DeniseViltes/Tesis/docs/informe/Entregas Parciales/2025-11-14.pdf

# Informe 7/11/2025

### Integrantes

## Sebastián Ezequiel García

Padrón: 103780
sebgarcia@fi.uba.ar

## Denise Oriana Viltes

Padrón: 106943
dviltes@fi.uba.ar

### Tutora

## Dra. Cecilia G. Galarza

cgalar@fi.uba.ar

### Cotutor

## Ing. Juan Zuloaga

jzuloaga@fi.uba.ar

Propuesta de Trabajo Profesional de Ingeniería | Año 2025

## 1. Resultados de la semana

### 1.1. Análisis térmico en el PMOS

### 1.1.1. Resistencia térmica para el encapsulado AO3401A

Se parte de la ecuación de resistencia térmica:

θja = θjc + θcs + θsa

Donde θja es la resistencia térmica entre la juntura y el ambiente, θjc entre juntura y carcasa, θcs entre carcasa y disipador, y θsa entre disipador y ambiente. La que se busca calcular es esta última.
Previamente se debe calcular únicamente θja, dado que θcs se toma como 1,5

◦C
W
por la resistencia de la pasta térmica y θjc se da en la datasheet como 125 ◦C
W .
El parámetro faltante se lo calcula como:

θja =

Tj − Ta

P cmáx

Donde Tj es la temperatura máxima de la juntura, Ta la ambiente y P cmáx la máxima potencia en el transistor. De la hoja de datos se tomó como 150 ◦C y

considerando que se utilice durante el verano, se toma la temperatura ambiente 30 ◦C. Sin embargo, la potencia es prácticamente nula en todo momento

### 1.2. PCB

Exportamos directamente de LTspice el esquemático a Kicad, arreglamos pines y asignamos huellas. Asimismo se agregan test points, y conectores.

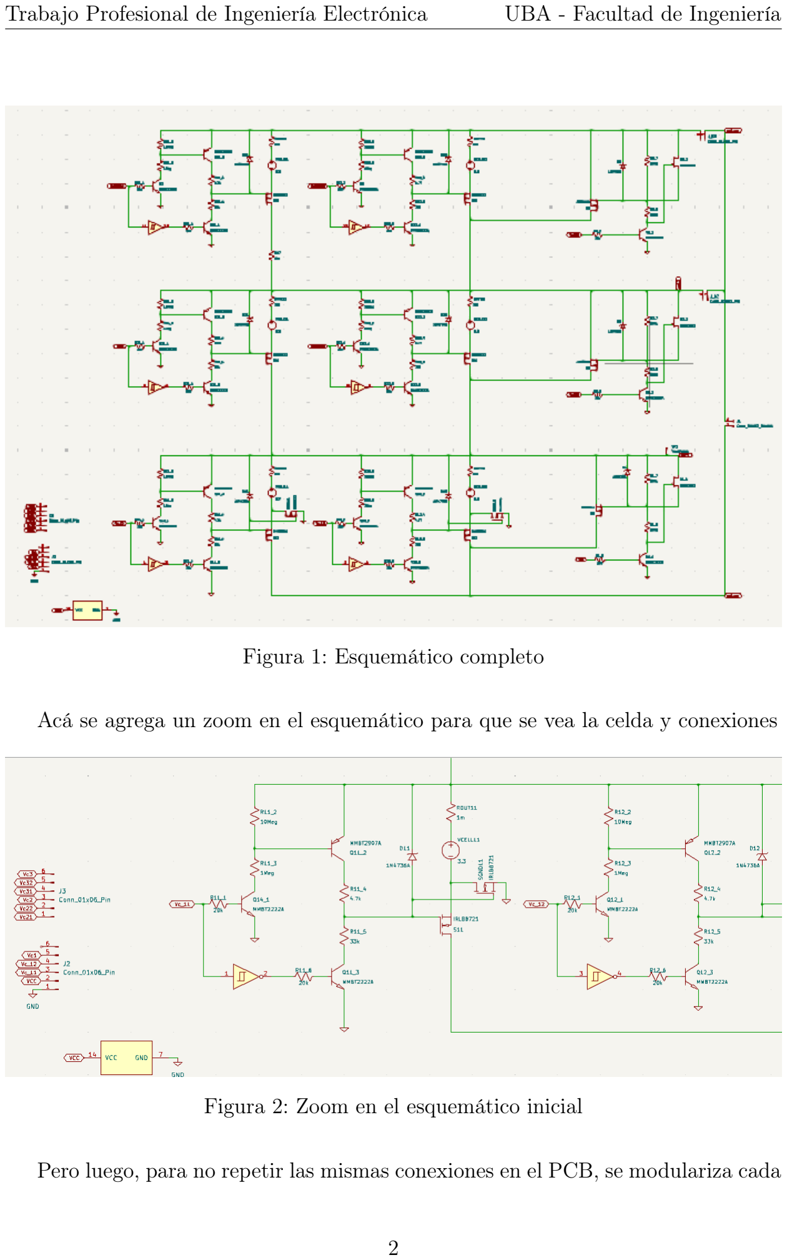
[picture p95: page 3]

Trabajo Profesional de Ingeniería Electrónica | UBA - Facultad de Ingeniería

Figura 1: Esquemático completo

Acá se agrega un zoom en el esquemático para que se vea la celda y conexiones

Figura 2: Zoom en el esquemático inicial

Pero luego, para no repetir las mismas conexiones en el PCB, se modulariza cada

2

Trabajo Profesional de Ingeniería Electrónica | UBA - Facultad de Ingeniería

switch, la propuesta de módulo es:

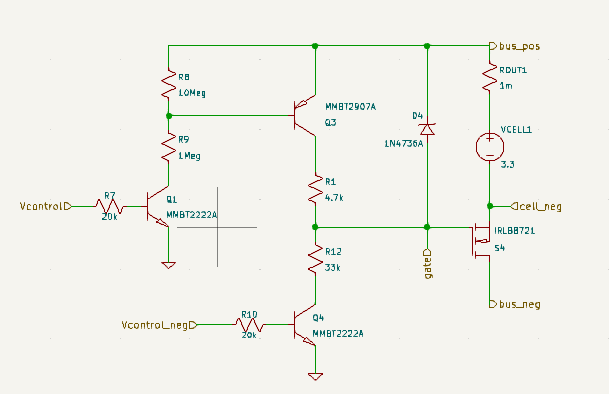
[picture p96: figure]

Figura 3: Módulo para el switch NMOS

3

Trabajo Profesional de Ingeniería Electrónica | UBA - Facultad de Ingeniería

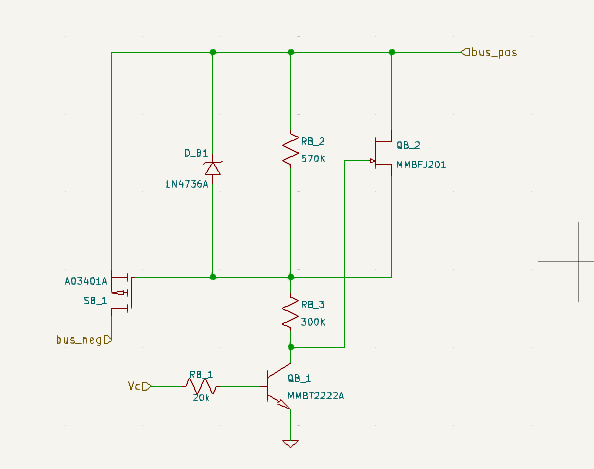
[picture p97: figure]

Figura 4: Módulo para el switch PMOS

4

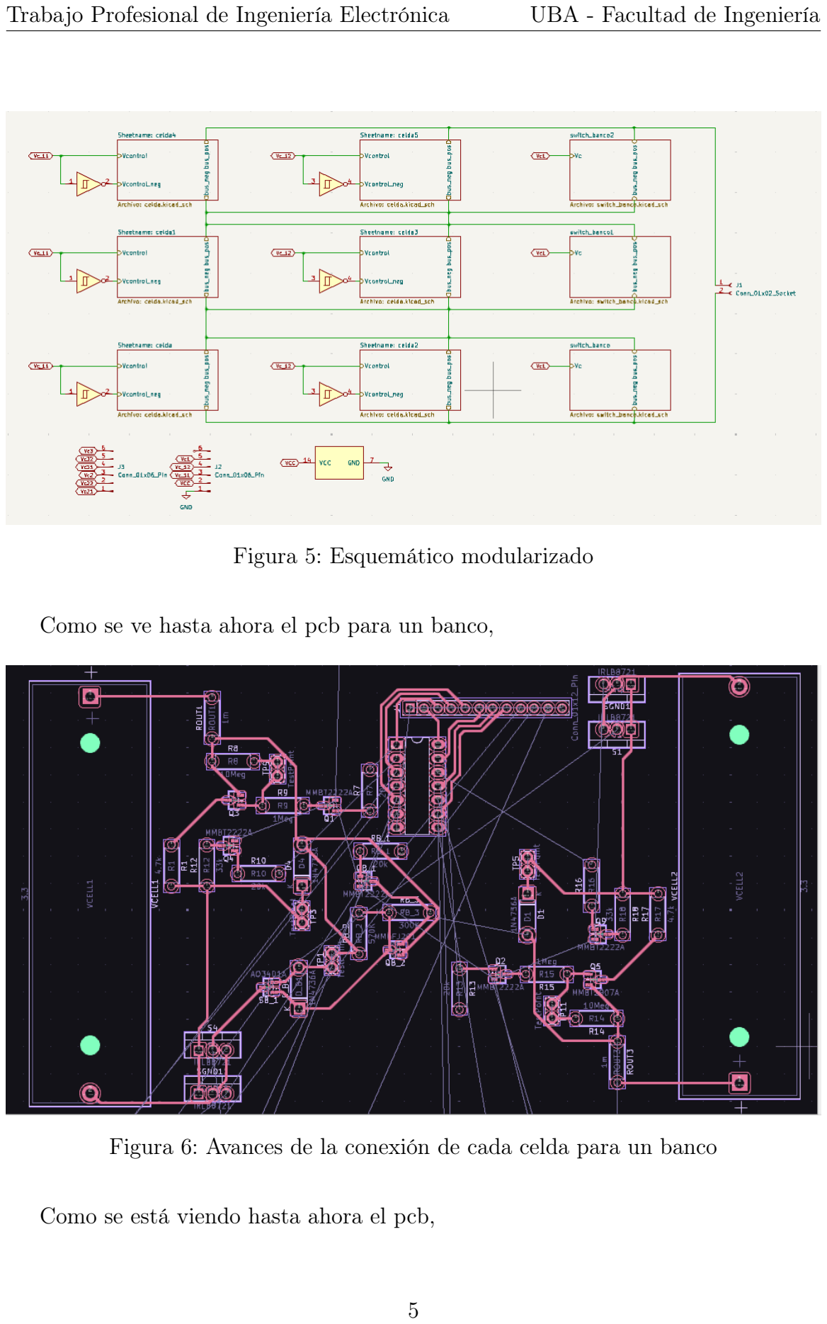
[picture p98: page 6]

Trabajo Profesional de Ingeniería Electrónica | UBA - Facultad de Ingeniería

Figura 5: Esquemático modularizado

Como se ve hasta ahora el pcb para un banco,

Figura 6: Avances de la conexión de cada celda para un banco

Como se está viendo hasta ahora el pcb,

5

Trabajo Profesional de Ingeniería Electrónica | UBA - Facultad de Ingeniería

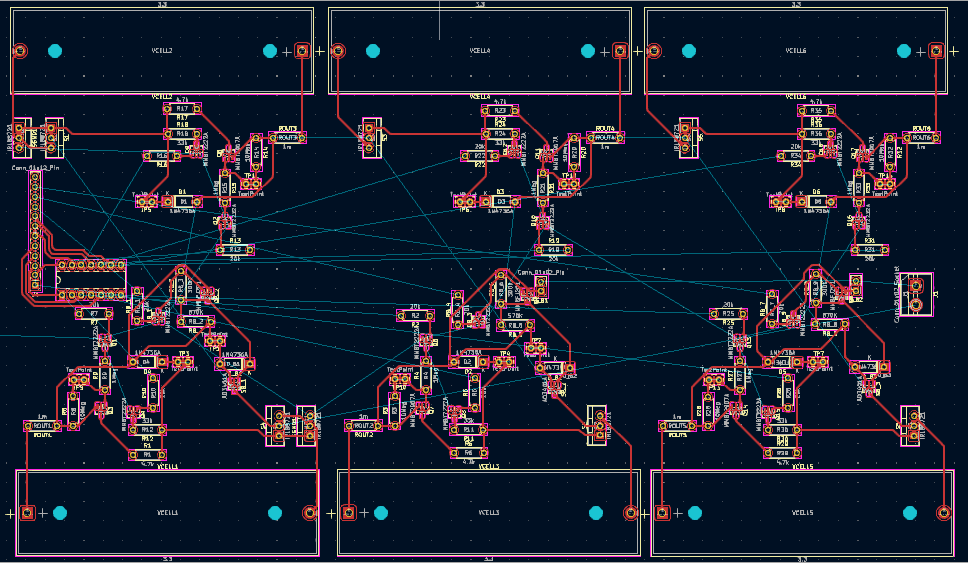
[picture p99: figure]

Figura 7: PCB entero.

6
