DeniseViltes/Tesis/docs/informe/Entregas Parciales/2025-11-28.pdf

# Informe 28/11/2025

### Integrantes

## Sebastián Ezequiel García

Padrón: 103780
sebgarcia@fi.uba.ar

## Denise Oriana Viltes

Padrón: 106943
dviltes@fi.uba.ar

### Tutora

## Dra. Cecilia G. Galarza

cgalar@fi.uba.ar

### Cotutor

## Ing. Juan Zuloaga

jzuloaga@fi.uba.ar

Propuesta de Trabajo Profesional de Ingeniería | Año 2025

## 1. Resultados de la semana

Acomodamos los elementos del pcb para que no quede tan largo, ya si obtener una versión más compacta. Para trabajar más cómodos, pasamos las pistas a un minimos de 0.6mm, siendo la mayoría de 1mm.

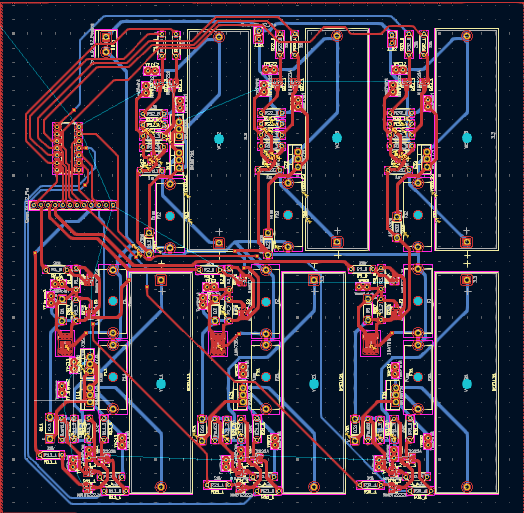
[picture p105: figure]

Figura 1: Nueva organización del pcb

Además cambiamos de capa las conexiones para los componenentes THT que solo podemos soldar de un lado, como los portapilas y portafusibles.

Trabajo Profesional de Ingeniería Electrónica | UBA - Facultad de Ingeniería

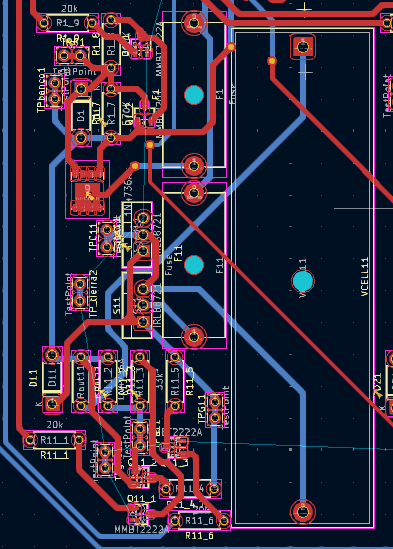
[picture p106: figure]

Figura 2: PCB de la celda 1 2

Trabajo Profesional de Ingeniería Electrónica | UBA - Facultad de Ingeniería

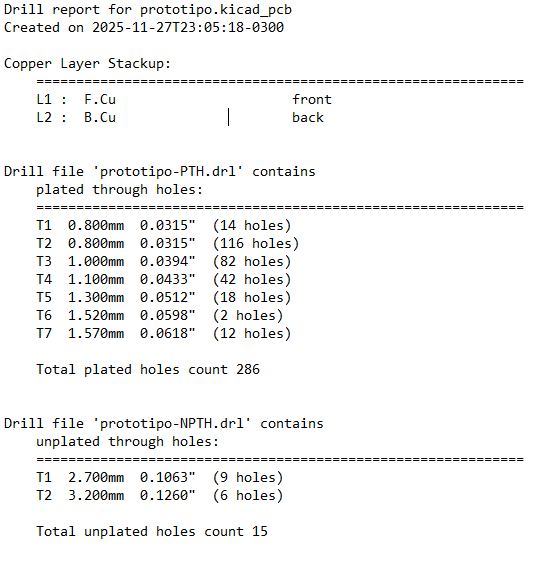
[picture p107: figure]

Figura 3: Resumen de agujeros del pcb

Cambio los agujeros:

1.0 mm ->1.1mm (pines de entrada, test points, jumpers)

2.7mm ->3.2 (portafusibles)

1.57 ->1.6 (portapilas)

3

Trabajo Profesional de Ingeniería Electrónica | UBA - Facultad de Ingeniería

1.52 ->1.6 (bornera)

Cantidad Forma | Tamaño X | Tamaño Y | Revestido
124 | Redondo 1.1000 mm 1.1000 mm PTH
116 | Redondo 0.8000 mm 0.8000 mm PTH
18 | Redondo 1.3000 mm 1.3000 mm PTH
16 | Redondo 0.8000 mm 0.8000 mm PTH
15 | Redondo 3.2000 mm 3.2000 mm NPTH
14 | Redondo 1.6000 mm 1.6000 mm PTH

Cuadro 1: Tabla de distribución de agujeros

4

Trabajo Profesional de Ingeniería Electrónica | UBA - Facultad de Ingeniería

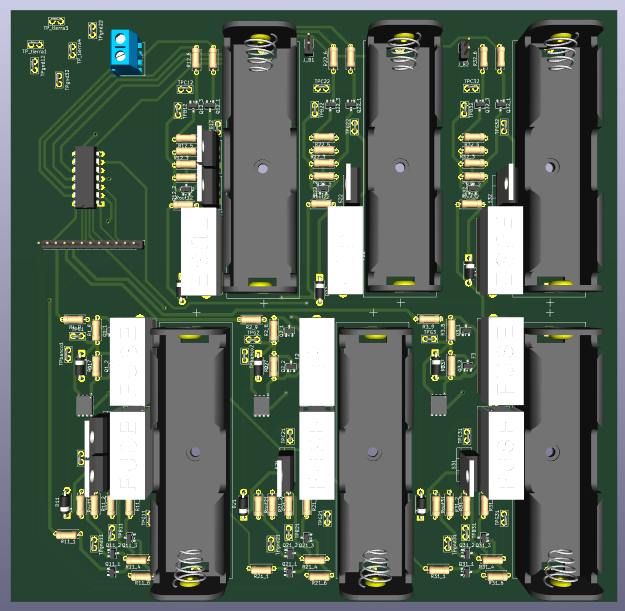
[picture p108: figure]

Figura 4: Vista superior del pcb

5

Trabajo Profesional de Ingeniería Electrónica | UBA - Facultad de Ingeniería

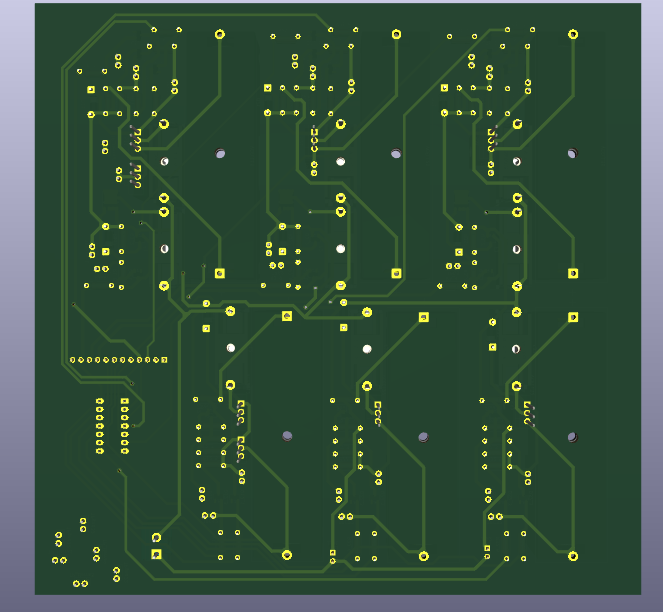
[picture p109: figure]

Figura 5: Vista inferior

6
