DeniseViltes/Tesis/docs/informe/Entregas Parciales/2026-01-16.pdf

# Informe 16/01/2026

Integrantes

## Sebastián Ezequiel García

Padrón: 103780
sebgarcia@fi.uba.ar

## Denise Oriana Viltes

Padrón: 106943
dviltes@fi.uba.ar

Tutora

## Dra. Cecilia G. Galarza

cgalar@fi.uba.ar
Cotutor

## Ing. Juan Zuloaga

jzuloaga@fi.uba.ar

Propuesta de Trabajo Profesional de Ingeniería | Año 2026

Trabajo Profesional de Ingeniería Electrónica | UBA - Facultad de Ingeniería

## 1. Carga en el circuito

Se reemplazaron las celdas por capacitores descargados de 1 µF para hacer la simulación en LTspice. Para la alimentación se pusieron en paralelo una fuente de tensión de 9,9 V y una de corriente de 500 mA.

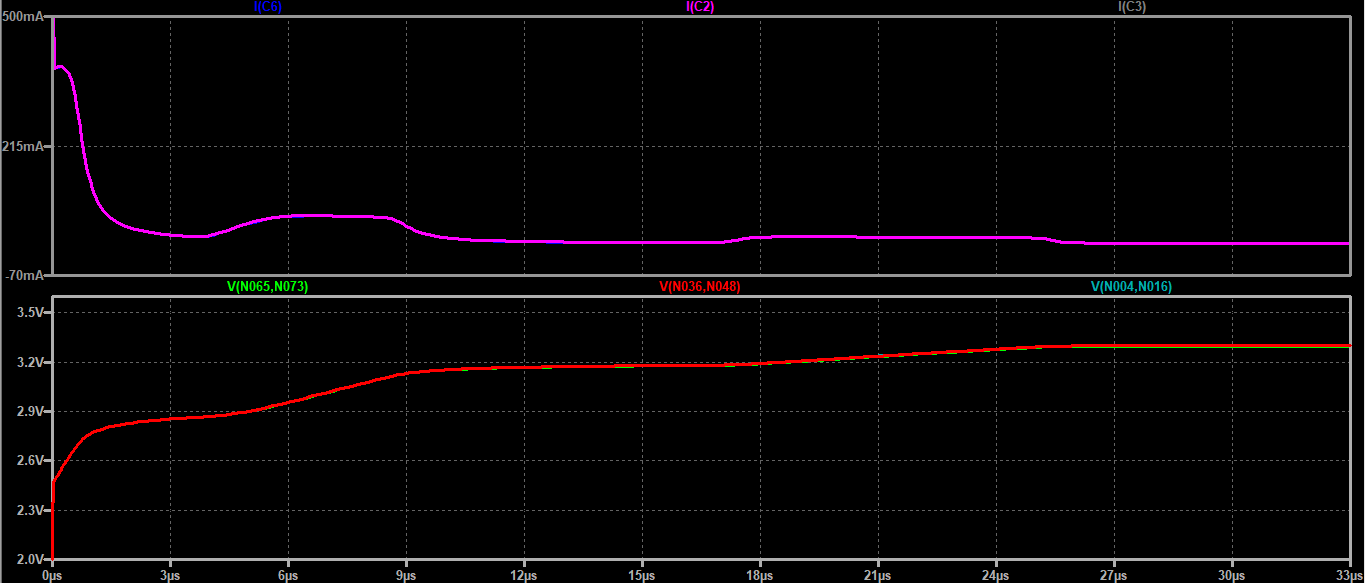
[picture p123: figure]

Figura 1: Resultado de la simulación al poner el circuito en modo carga.

Cabe destacar que se configuraron todos los switches de la celdas encendidos y todos los de los bancos apagados.

1
