DeniseViltes/Tesis/docs/informe/Entregas Parciales/2025-11-7.pdf

# Informe 7/11/2025

### Integrantes

## Sebastián Ezequiel García

Padrón: 103780
sebgarcia@fi.uba.ar

## Denise Oriana Viltes

Padrón: 106943
dviltes@fi.uba.ar

### Tutora

## Dra. Cecilia G. Galarza

cgalar@fi.uba.ar

### Cotutor

## Ing. Juan Zuloaga

jzuloaga@fi.uba.ar

Propuesta de Trabajo Profesional de Ingeniería | Año 2025

## 1. Resultados de la semana

### 1.1. Mosfet en tierra

Se observa menos oscilación, y resultados similares a resistencias altas en tierra con el beneficio de que no altera el comportamiento del circuito.
Primero lo colocacamos con gate y sources conectado a los mismos puntos que el nmos principal, pero deformaba la corriente en las celdas. Cambiamos la conexión poniendo el source a tierra y se adapta perfectamente al comportamiento de la matriz.

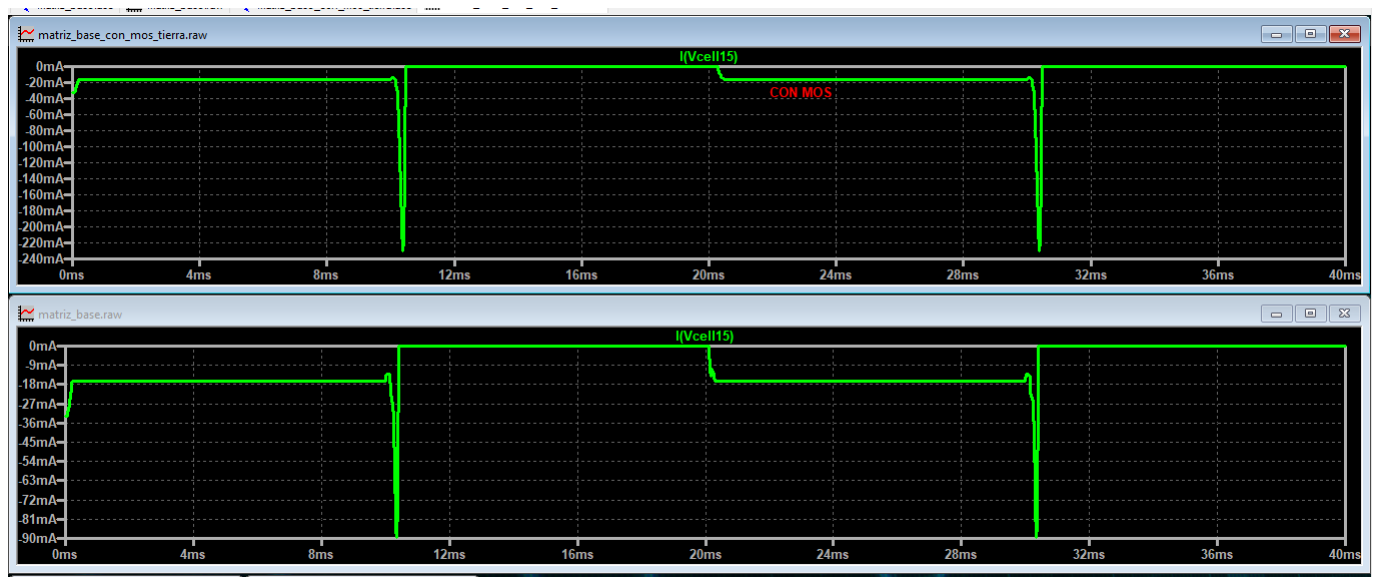
[picture p136: figure]

Figura 1: Corriente en celda intercalada

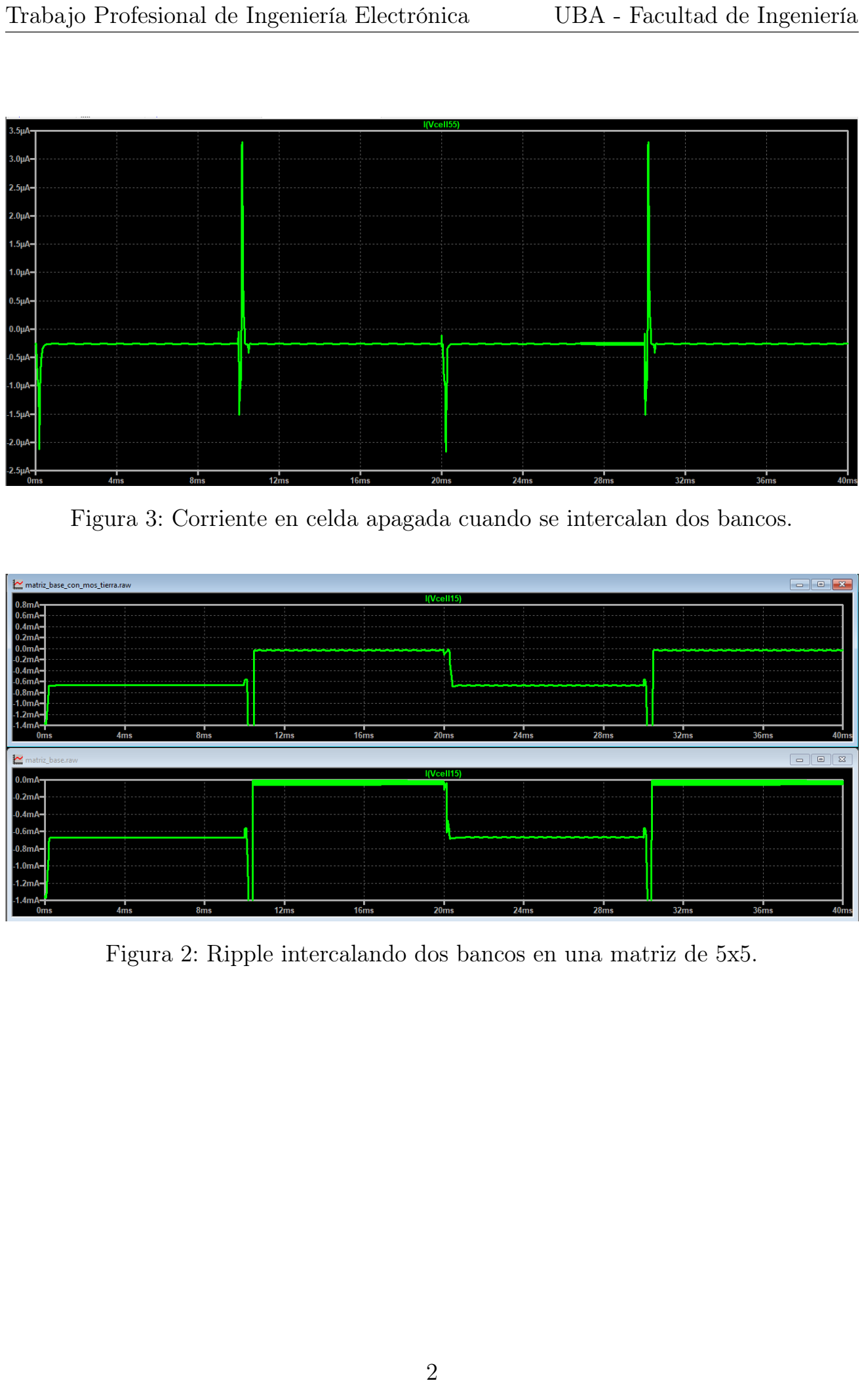
[picture p137: page 3]

Trabajo Profesional de Ingeniería Electrónica | UBA - Facultad de Ingeniería

Figura 3: Corriente en celda apagada cuando se intercalan dos bancos.

Figura 2: Ripple intercalando dos bancos en una matriz de 5x5.

2

Trabajo Profesional de Ingeniería Electrónica | UBA - Facultad de Ingeniería

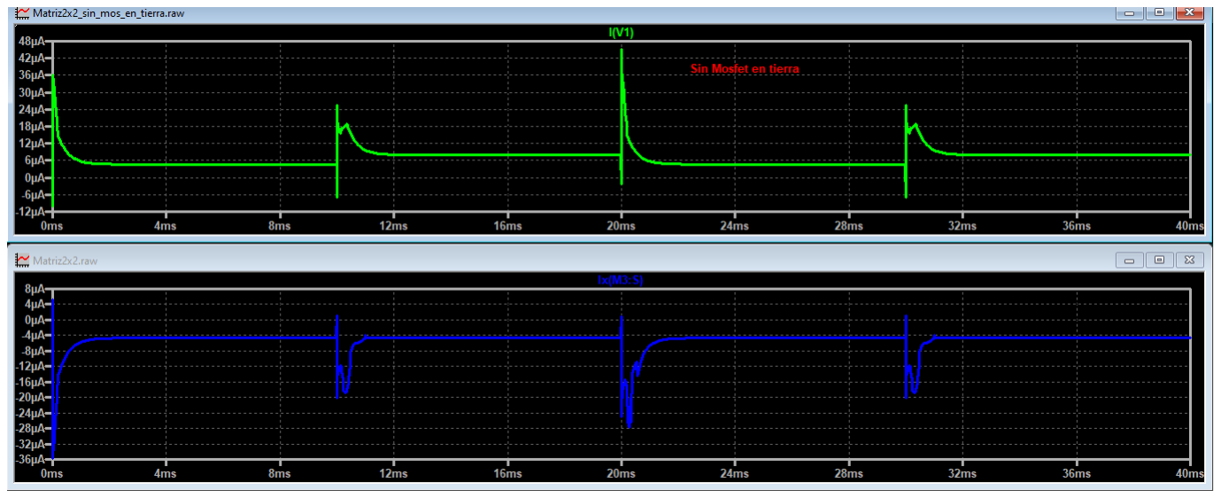
[picture p138: figure]

Figura 4: Corriente en tierra

### 1.2. Comparación de circuito con y sin inversores

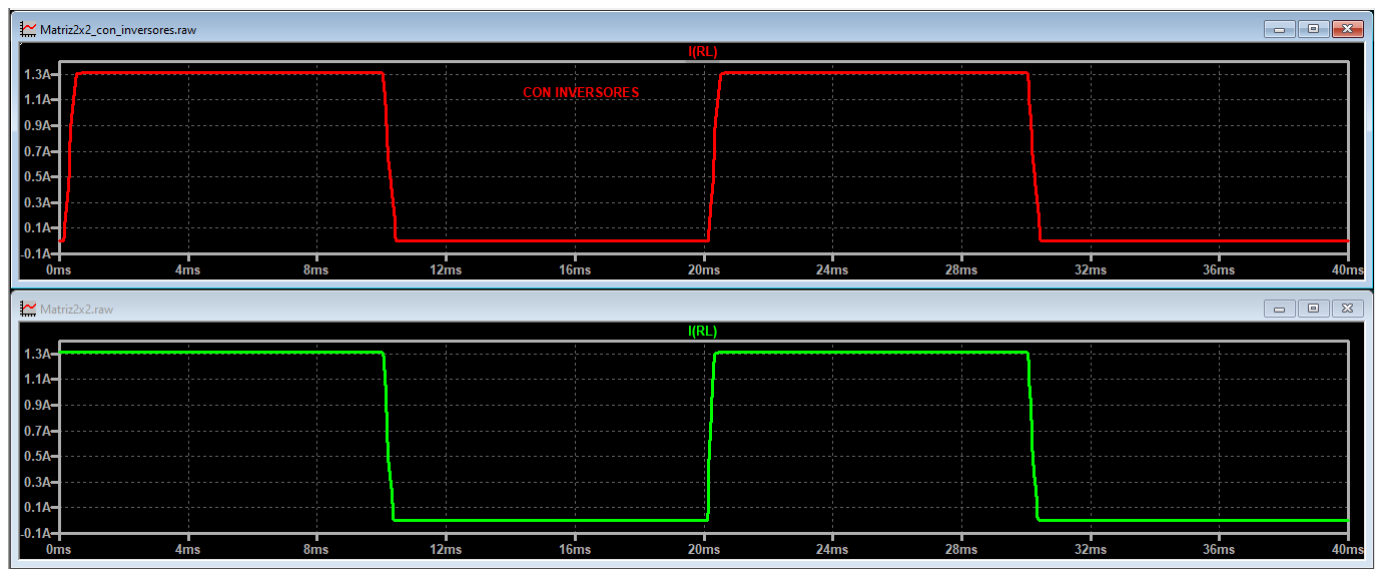
[picture p139: figure]

Figura 5: Corriente con y sin inversores para el banco 1 y 2 coordinados en prendido/apagado.

3

Trabajo Profesional de Ingeniería Electrónica | UBA - Facultad de Ingeniería

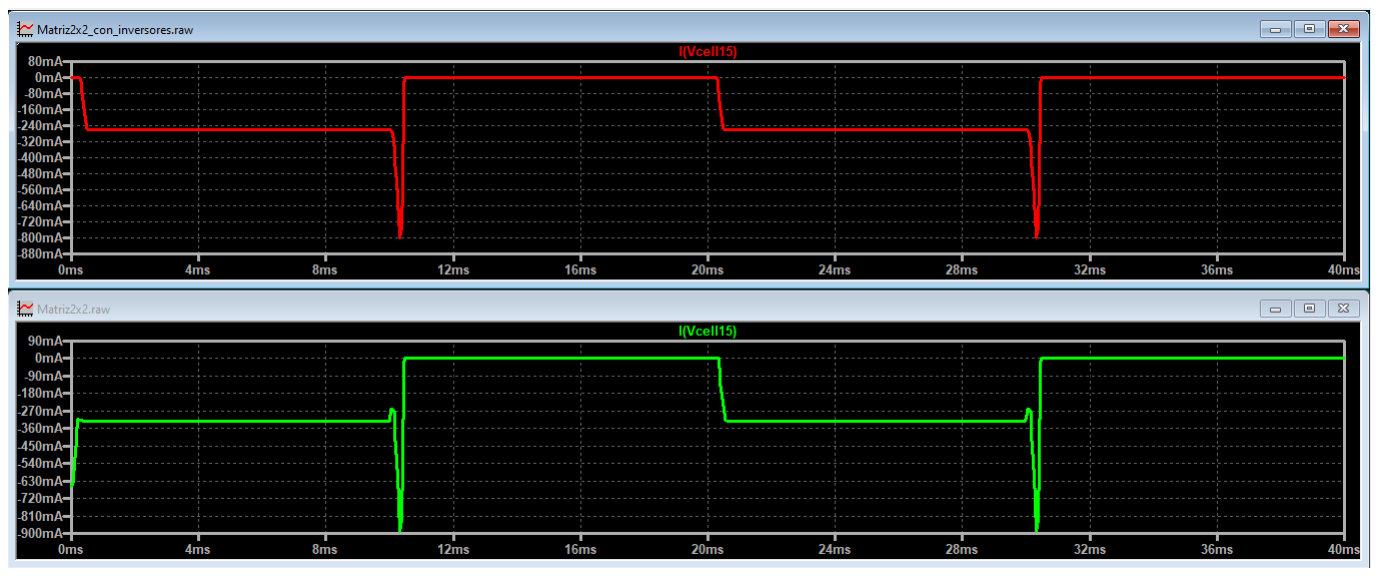
[picture p140: figure]

Figura 6: Corriente en las celdas para los bancos intercalados

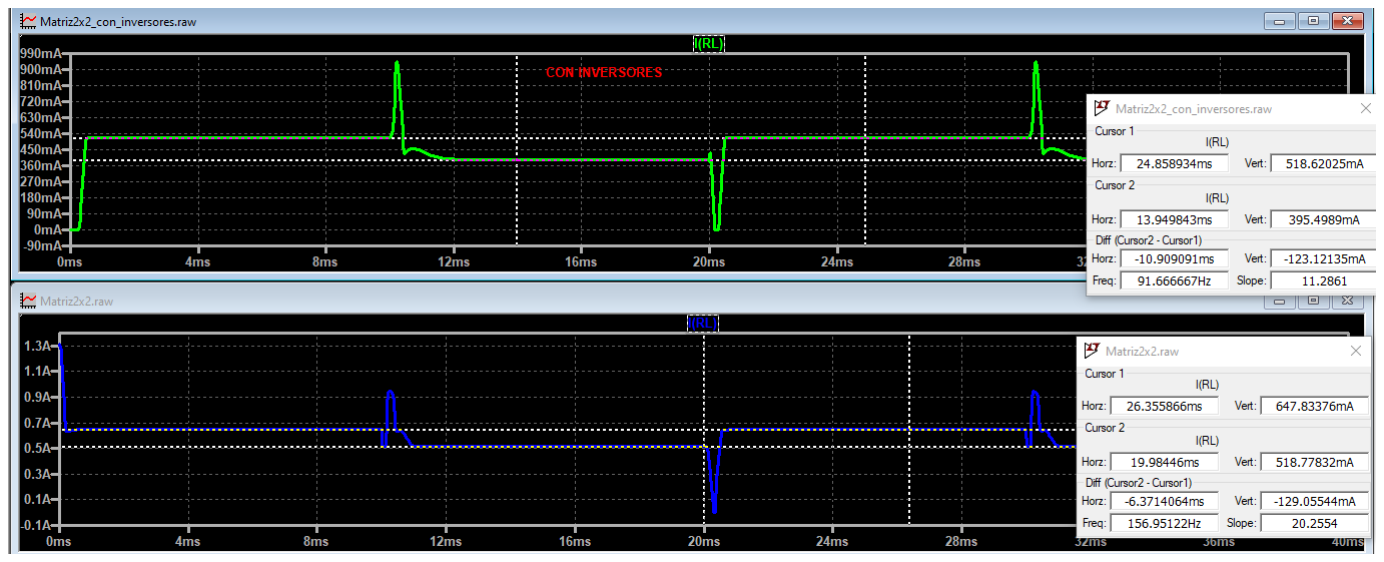
[picture p141: figure]

Figura 7: Corriente en la carga para bancos intercalados

### 1.3. Ripple

En cuanto al ripple que observamos hasta ahora

4

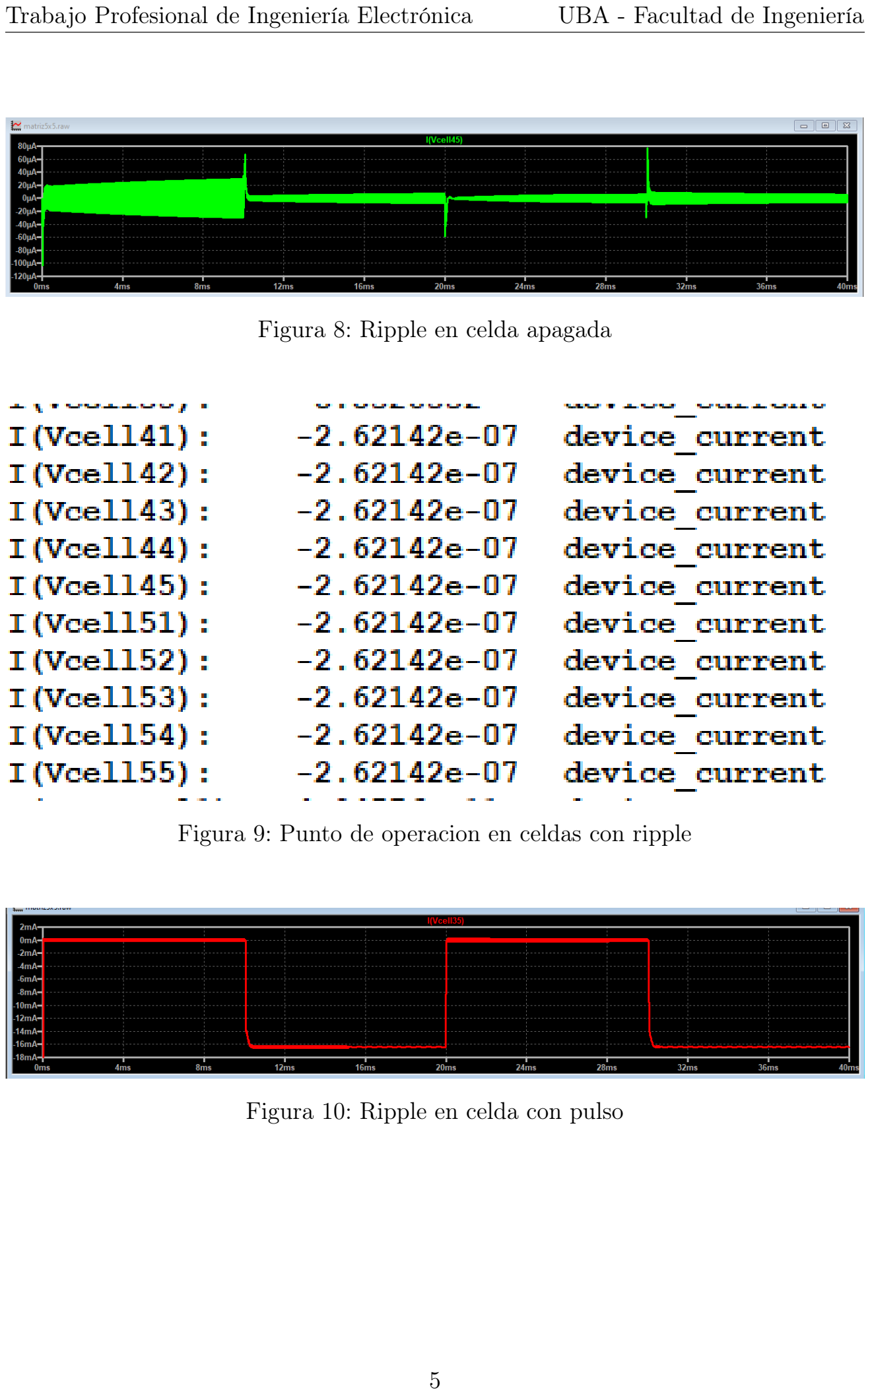
[picture p142: page 6]

Trabajo Profesional de Ingeniería Electrónica | UBA - Facultad de Ingeniería

Figura 8: Ripple en celda apagada

Figura 9: Punto de operacion en celdas con ripple

Figura 10: Ripple en celda con pulso

5

Trabajo Profesional de Ingeniería Electrónica | UBA - Facultad de Ingeniería

Figura 11: Enter Caption

### 1.4. Resistencias en el driver

Se disminuyen en un orden las resistencias en el driver, en el tbj de apagado, para permitir que haya un camino en el nmos pueda descargarse más rápido y asi evitamos poner un delay entre las fuentes del driver (al menos en simulación).

6
