DeniseViltes/Tesis/hardware/Circuito Final/Circuito externo/Pines controlador.xlsx

2 | PC10 | CLK | LATCH | PC11 | 1 | 2 | PC9 | S0 | S1 | PC8 | 1 | UART | Pines GPIO: | Pines ADC:
4 | PC12 | D1 |  | PD2 | 3 | 4 | PB8 |  | S2 | PC6 | 3 | ADC | B0 | OUT_ADC1
6 | VDD |  |  | E5V | 5 | 6 | PB9 |  | salida_adc_4 | PC5 | 5 | GPIO | B1 | bus_pos1
8 | BOOT0 |  |  | GND | 7 | 8 | AVDD |  |  | U5V | 7 | Potencia | B2 | bus_neg1
10 | - |  |  | - | 9 | 10 | GND |  |  | - | 9 | Reset | CLK_S | OUT_ADC2
12 | - |  |  | 3.3V | 11 | 12 | PA5/PB13 | banco4_med | D4 | PA12 | 11 | No usar | CLK_L | bus_pos2
14 | PA13 |  |  | Reset | 13 | 14 | PA6/PB14 | medicion_corriente_descarga | D3 | PA11 | 13 |  | D1 | bus_neg2
16 | PA14 |  |  | 3.3V | 15 | 16 | PA7/PB15 | banco3_med |  | PB12 | 15 |  | D2 | OUT_ADC3
18 | PA15 |  | vcc stm | 5V | 17 | 18 | PB6 |  |  | PB11 | 17 |  | D3 | bus_pos3
20 | GND |  |  | GND | 19 | 20 | PC7 |  |  | GND | 19 |  | D4 | bus_neg3
22 | PB7 |  |  | GND | 21 | 22 | PA9 |  |  | PB2 | 21 |  |  | OUT_ADC4
24 | PC13 | D2 |  | VIN | 23 | 24 | PA8 |  |  | PB1 | 23 |  |  | bus_pos4
26 | PC14 |  |  | - | 25 | 26 | PB10 |  |  | PB15/PA7 | 25 |  |  | bus_neg4
28 | PC15 |  | salida_adc_1 | PA0 | 27 | 28 | PB4 |  |  | PB14/PA6 | 27
30 | PD0 |  | banco1_med | PA1 | 29 | 30 | PB5 |  |  | PB13/PA5 | 29
32 | PD1 |  | ADC4 | PA4 | 31 | 32 | PB3 |  |  | AGND | 31
34 | VDD |  |  | PB0 | 33 | 34 | PA10 | llave de emergencia | salida_adc_3 | PC4 | 33
36 | PC2 | salida_adc_2 | ADC11 | PC1/PB9 | 35 | 36 | PA2 |  |  | - | 35
38 | PC3 | banco2_med | medicion_corriente_de_carga | PC0/PB8 | 37 | 38 | PA3 |  |  | - | 37
