DeniseViltes/Tesis/hardware/Circuito Final/Switch banco - Torre/pines_entrada.xlsx

VCC | CLOCK | GND | BUS NEG | BUS POS | BIT 2 | BIT 1
DATA | LATCH | GND | BUS NEG | BUS POS | SALIDA ADC | BIT 0
