DeniseViltes/Tesis/docs/burocracia/Acta de acuerdo.pdf

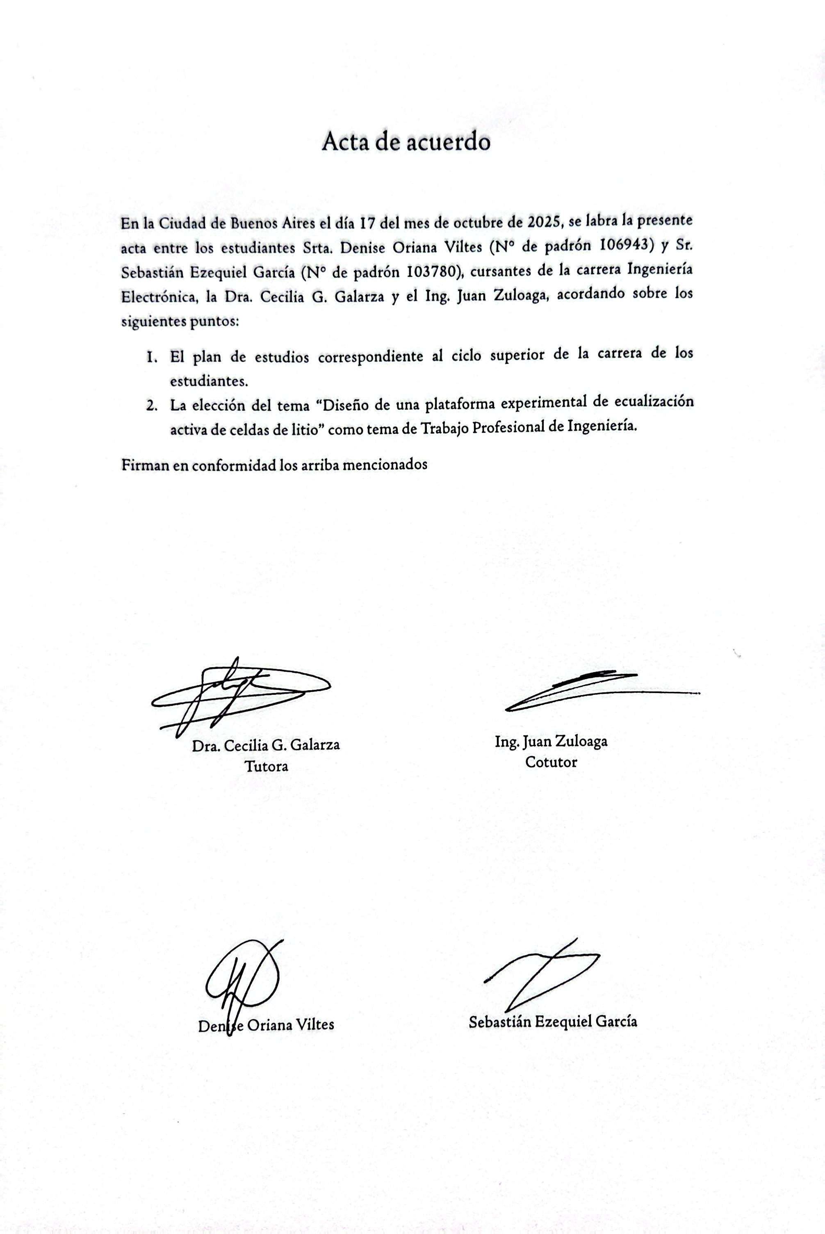
[picture p148: page 1]
