DeniseViltes/Tesis/codigo/firmware/Controlador/BluePill - STM32F103 - Pinout.jpg

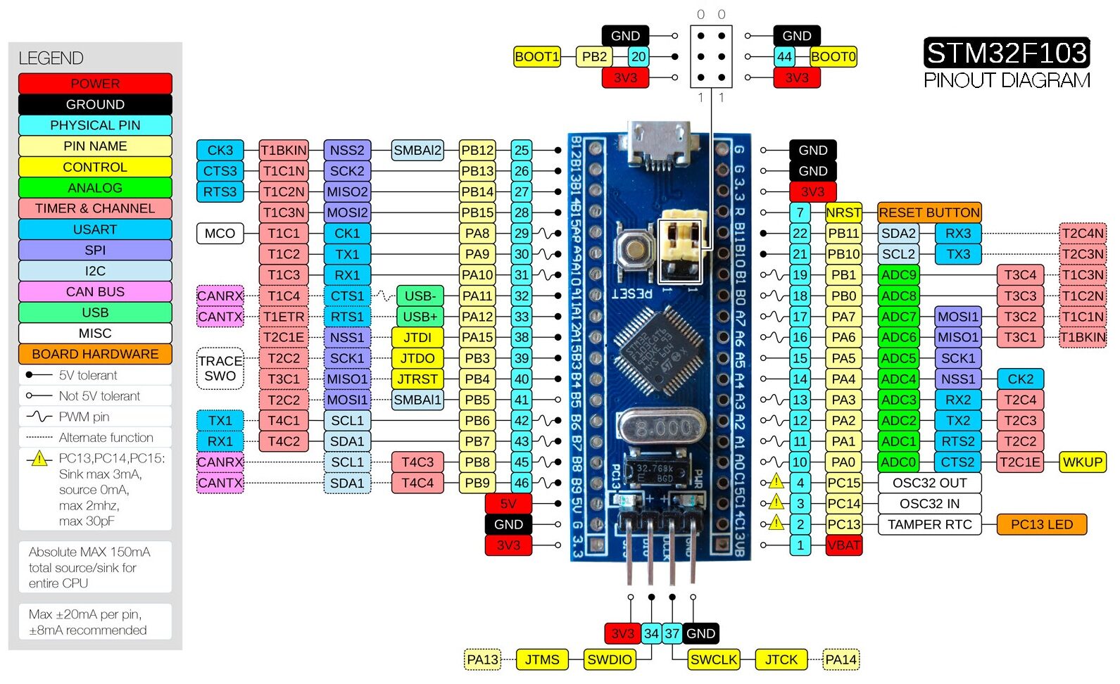
codigo/firmware/Controlador/BluePill - STM32F103 - Pinout.jpg
