DeniseViltes/Tesis/codigo/firmware/Controlador/Prototipo/documentacion/01_funcionamiento_general.png

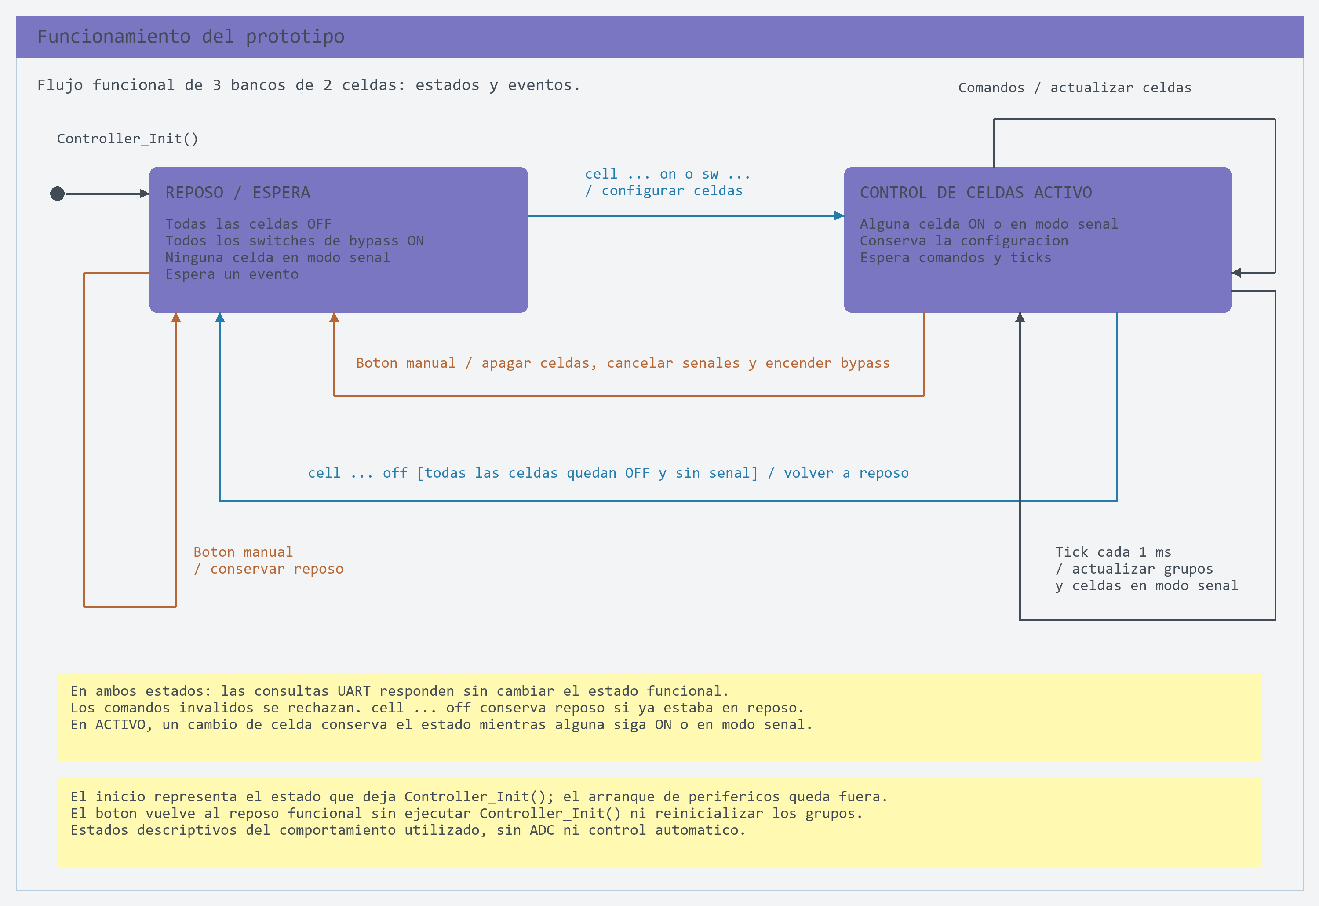
codigo/firmware/Controlador/Prototipo/documentacion/01_funcionamiento_general.png
