DeniseViltes/Tesis/codigo/firmware/Controlador/Prototipo/documentacion/02_estados_celda.png

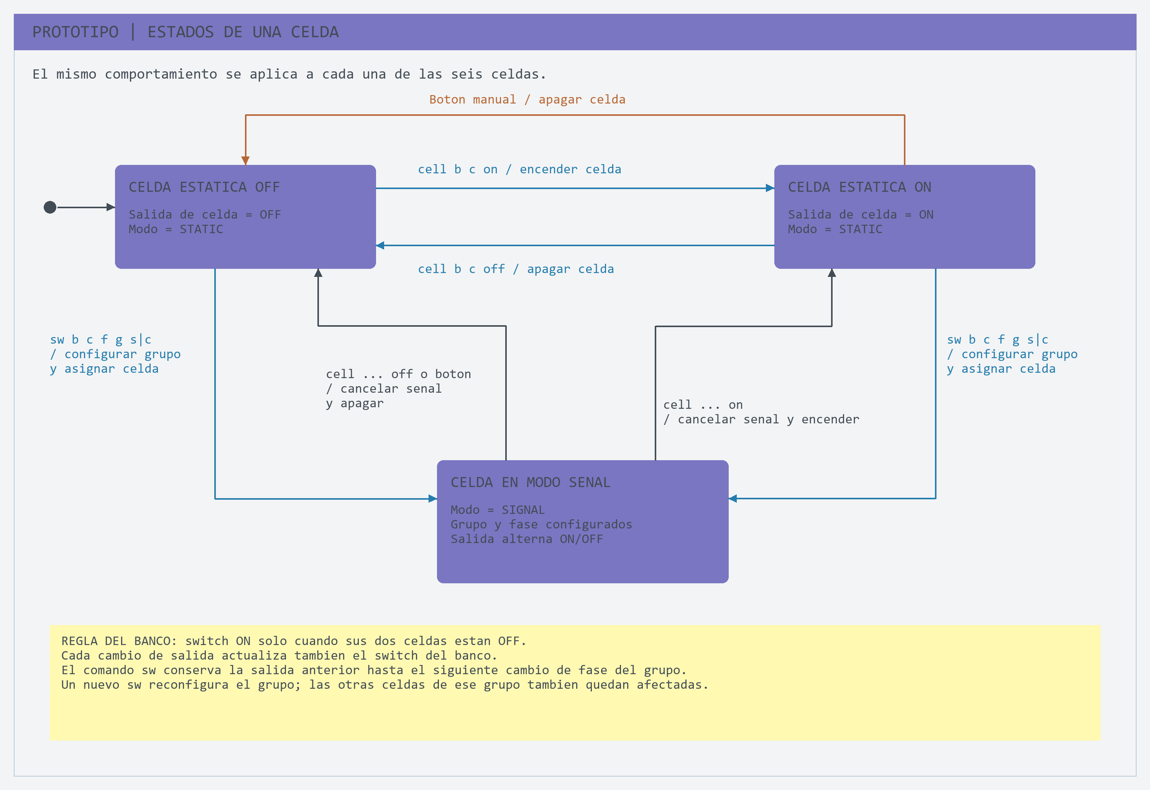
codigo/firmware/Controlador/Prototipo/documentacion/02_estados_celda.png
