DeniseViltes/Tesis/codigo/firmware/Controlador/Prototipo/documentacion/03_generador_grupo.png

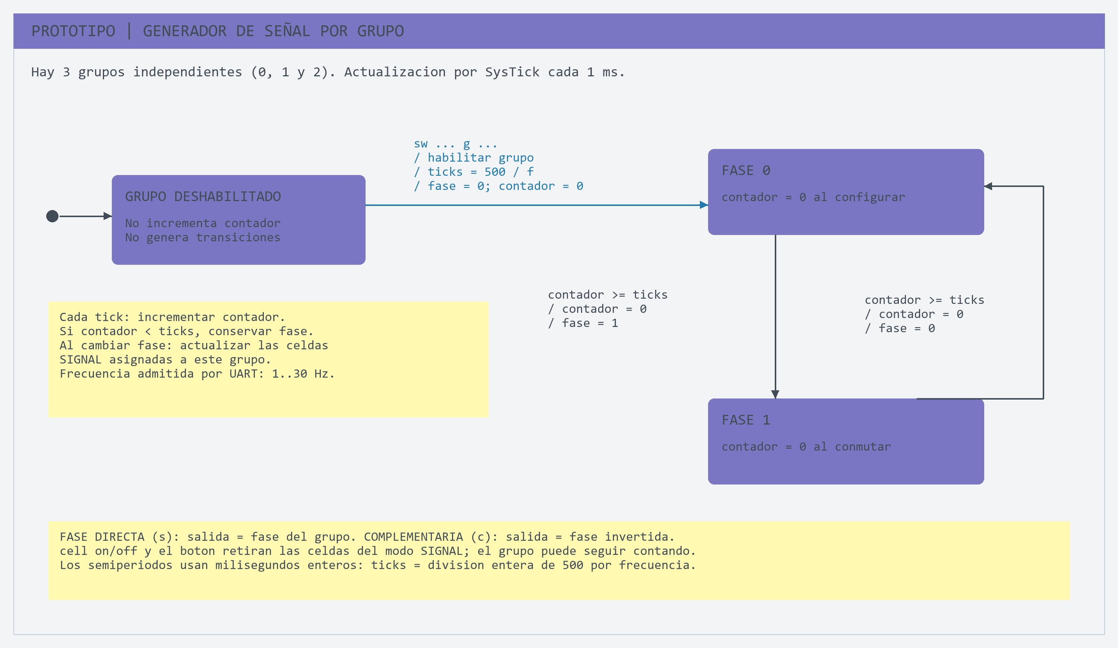
codigo/firmware/Controlador/Prototipo/documentacion/03_generador_grupo.png
