DeniseViltes/Tesis/docs/datasheets/PHiLIP-NUCLEOF103RB-PINOUT.png

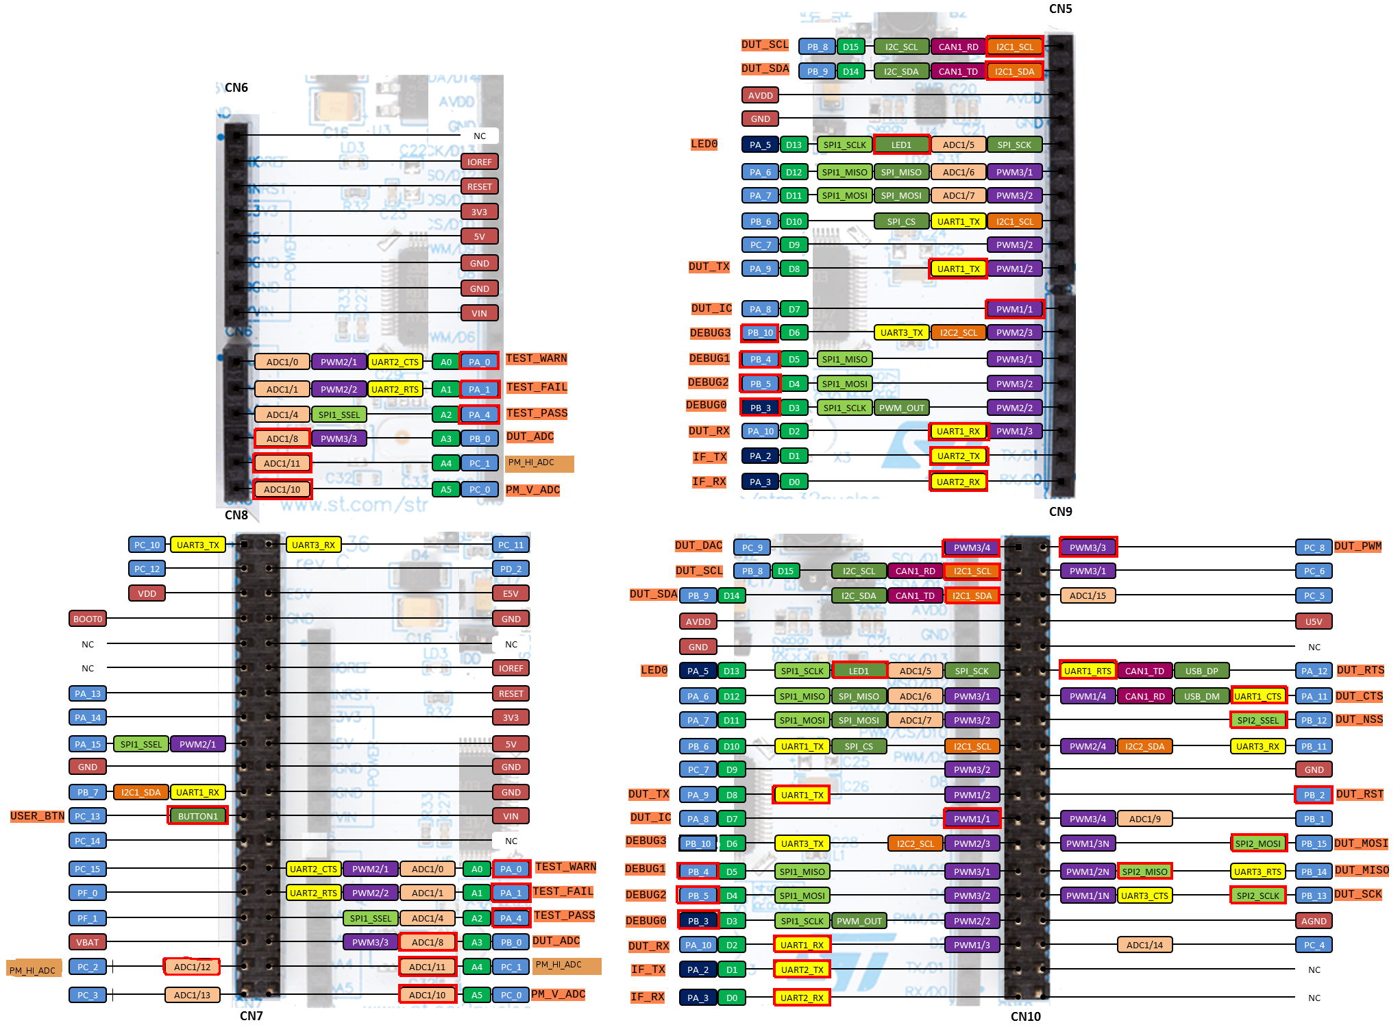
docs/datasheets/PHiLIP-NUCLEOF103RB-PINOUT.png
