DeniseViltes/Tesis/docs/informe/CFA.jpeg

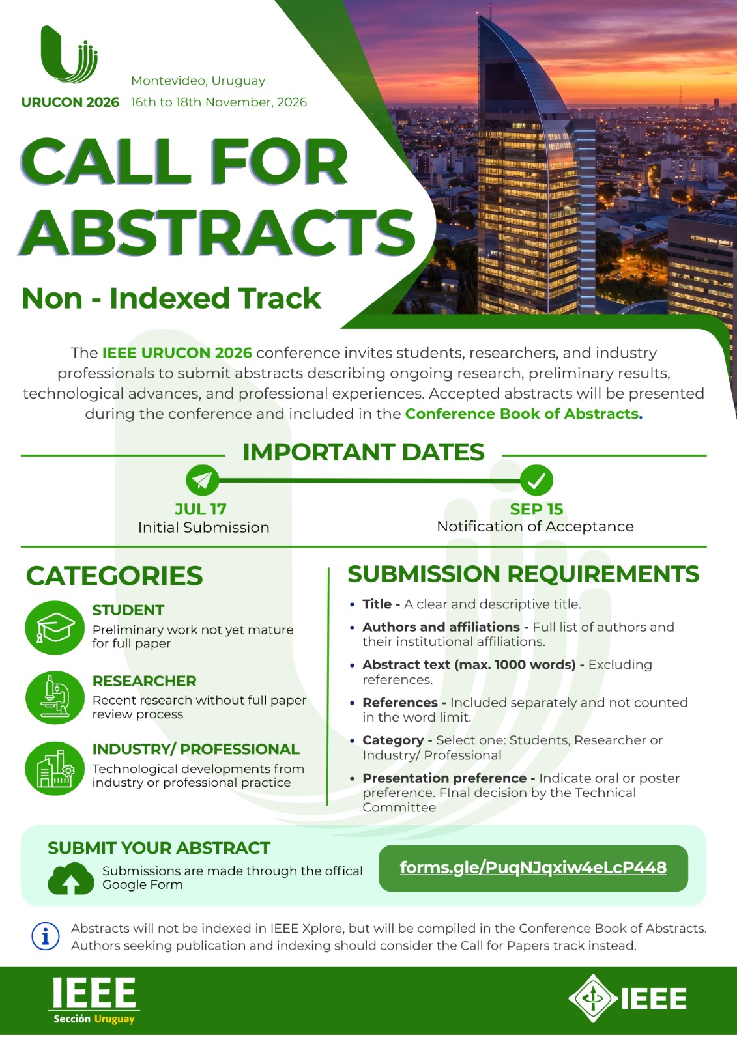
docs/informe/CFA.jpeg
