DeniseViltes/Tesis/docs/informe/Informe_Final/Imágenes/Diseño final/diagrama_logico_SR.png

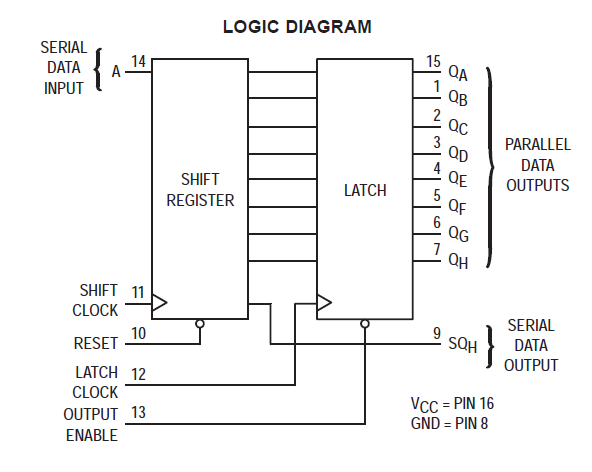
docs/informe/Informe_Final/Imágenes/Diseño final/diagrama_logico_SR.png
