DeniseViltes/Tesis/docs/informe/Informe_Final/Imágenes/Diseño final/pinout SR.png

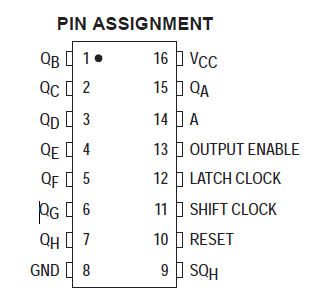
docs/informe/Informe_Final/Imágenes/Diseño final/pinout SR.png
