DeniseViltes/Tesis/docs/Papers/para leer/Captura_2.jpg

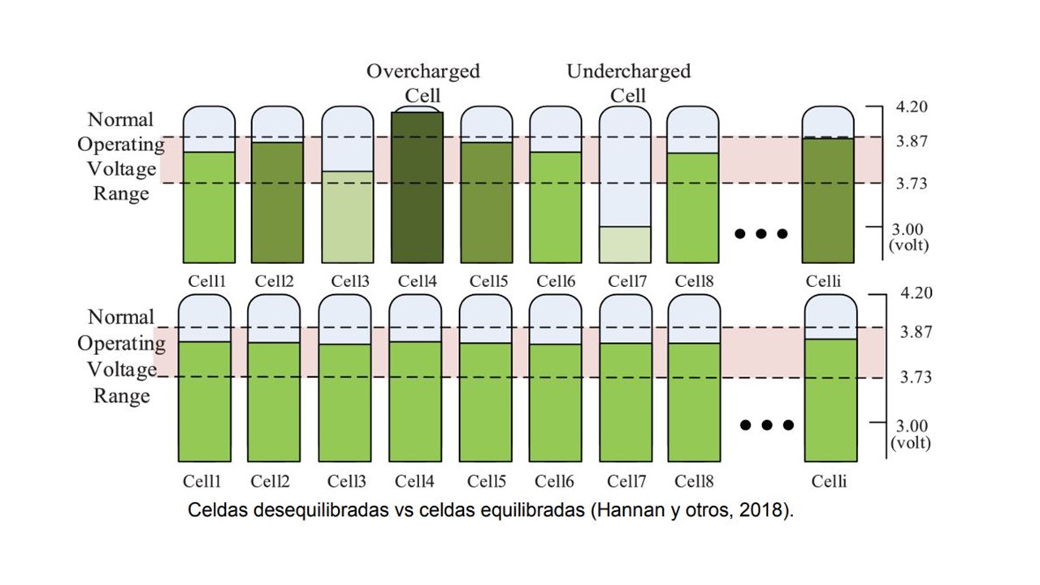
docs/Papers/para leer/Captura_2.jpg
