DeniseViltes/Tesis/hardware/PCB/Modelos 3D/Cable plano dimensiones 3D.png

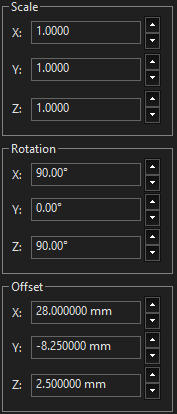
hardware/PCB/Modelos 3D/Cable plano dimensiones 3D.png
