DeniseViltes/Tesis/hardware/PCB/Modelos 3D/Fusible dimensiones 3D.png

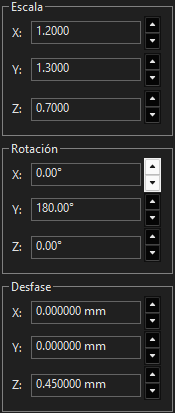
hardware/PCB/Modelos 3D/Fusible dimensiones 3D.png
