DeniseViltes/Tesis/Ltspice/proyectos/circuito_modular/version_2x2-b1on_b2on.png

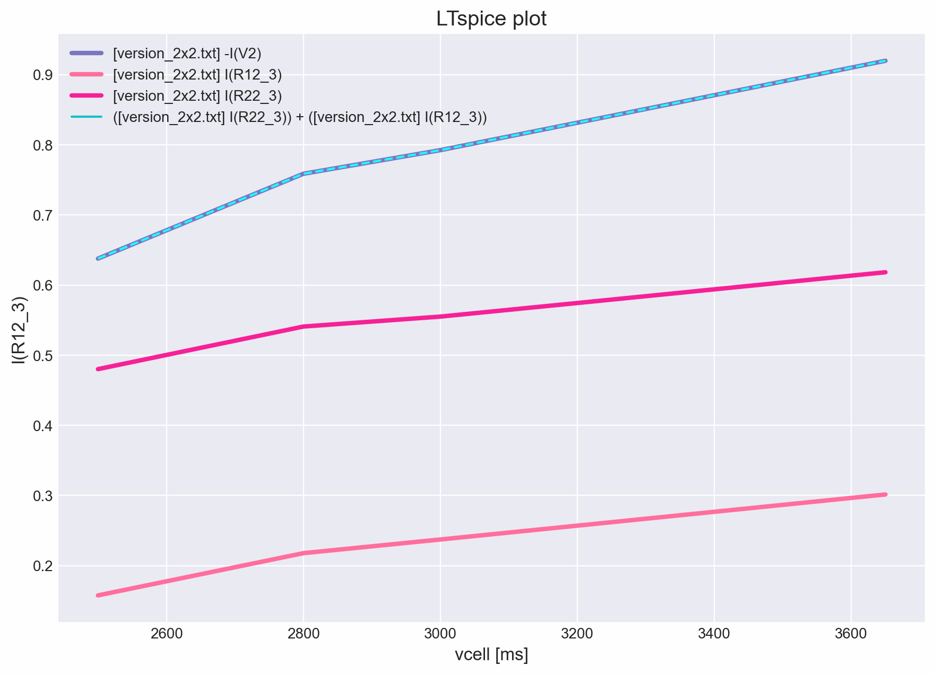
Ltspice/proyectos/circuito_modular/version_2x2-b1on_b2on.png
