DeniseViltes/Tesis/Ltspice/proyectos/matriz_2x2/runs/fugas_en_tierra/corriente_en_celda.png

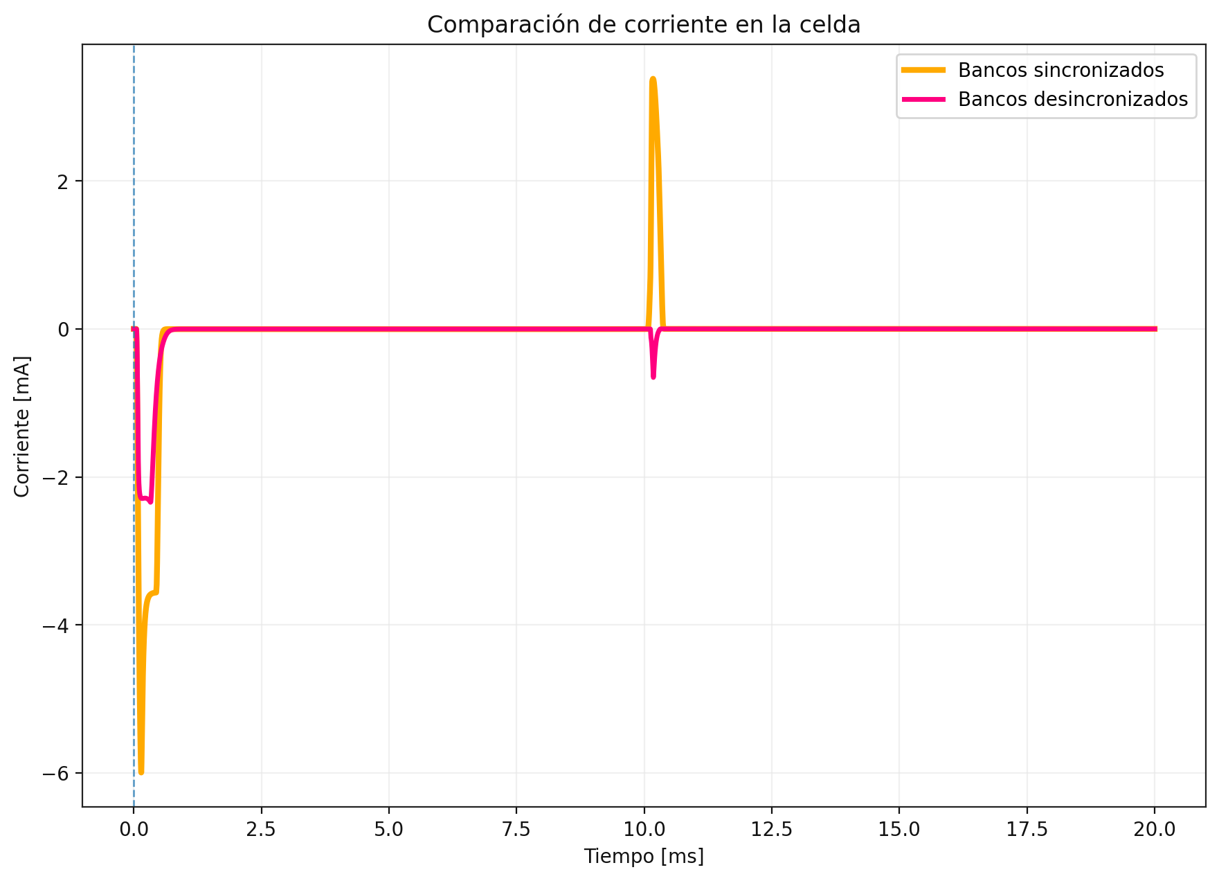
Ltspice/proyectos/matriz_2x2/runs/fugas_en_tierra/corriente_en_celda.png
