DeniseViltes/Tesis/Ltspice/proyectos/matriz_2x2/runs/fugas_en_tierra/corriente_en_la_tierra.png

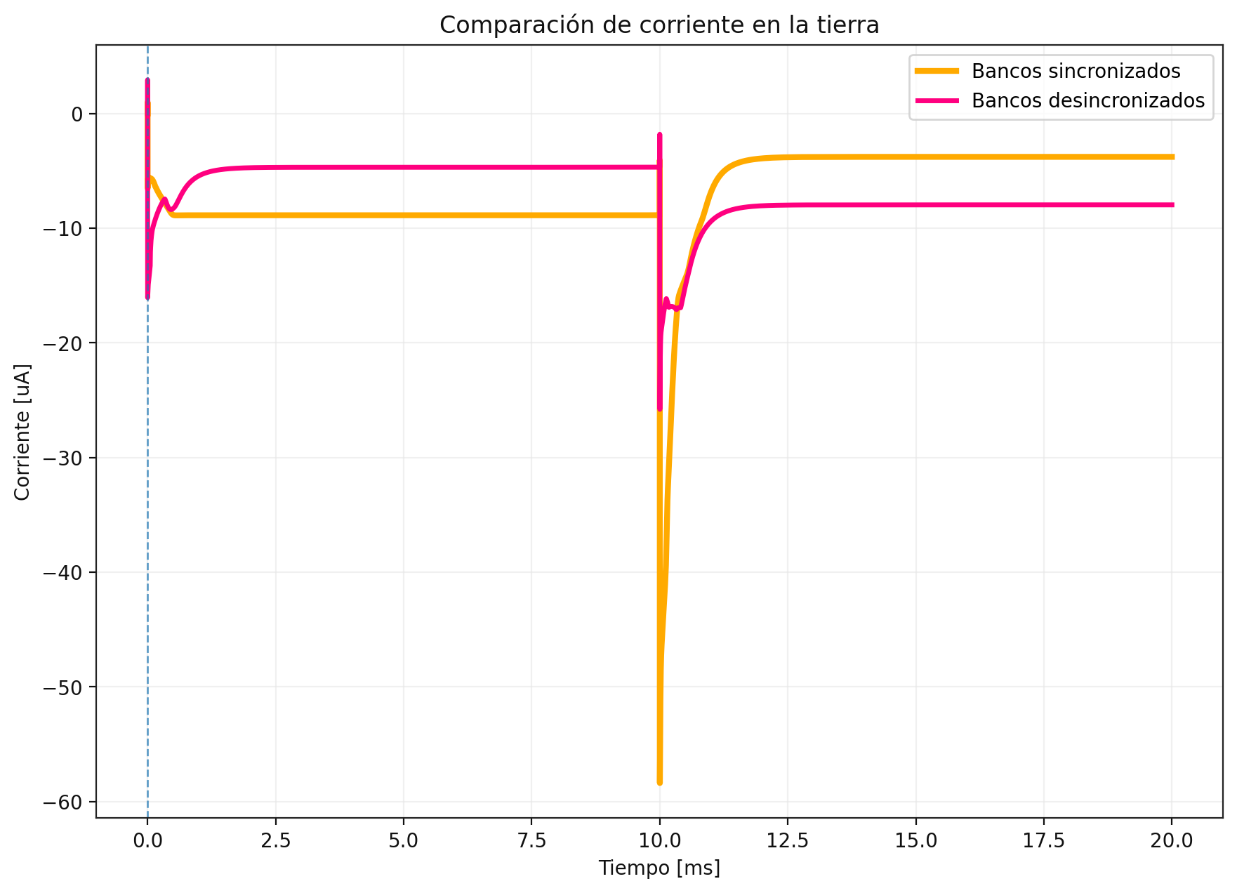
Ltspice/proyectos/matriz_2x2/runs/fugas_en_tierra/corriente_en_la_tierra.png
