DeniseViltes/Tesis/Ltspice/proyectos/matriz_2x2/runs/fugas_en_tierra/tension_en_la_salida.png

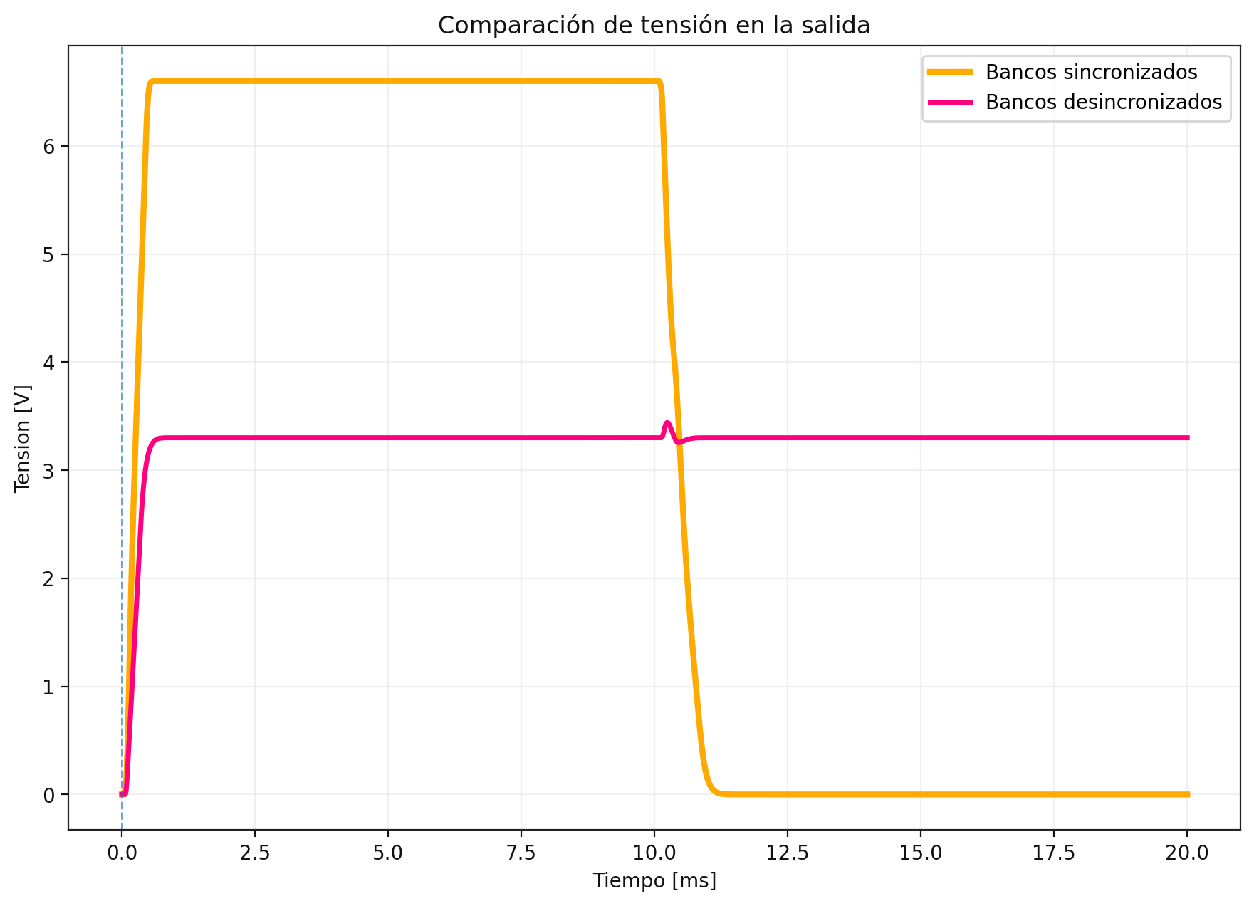
Ltspice/proyectos/matriz_2x2/runs/fugas_en_tierra/tension_en_la_salida.png
