DeniseViltes/Tesis/Ltspice/proyectos/matriz_2x2/runs/mosfet_en_tierra/corriente en la celda 25.png

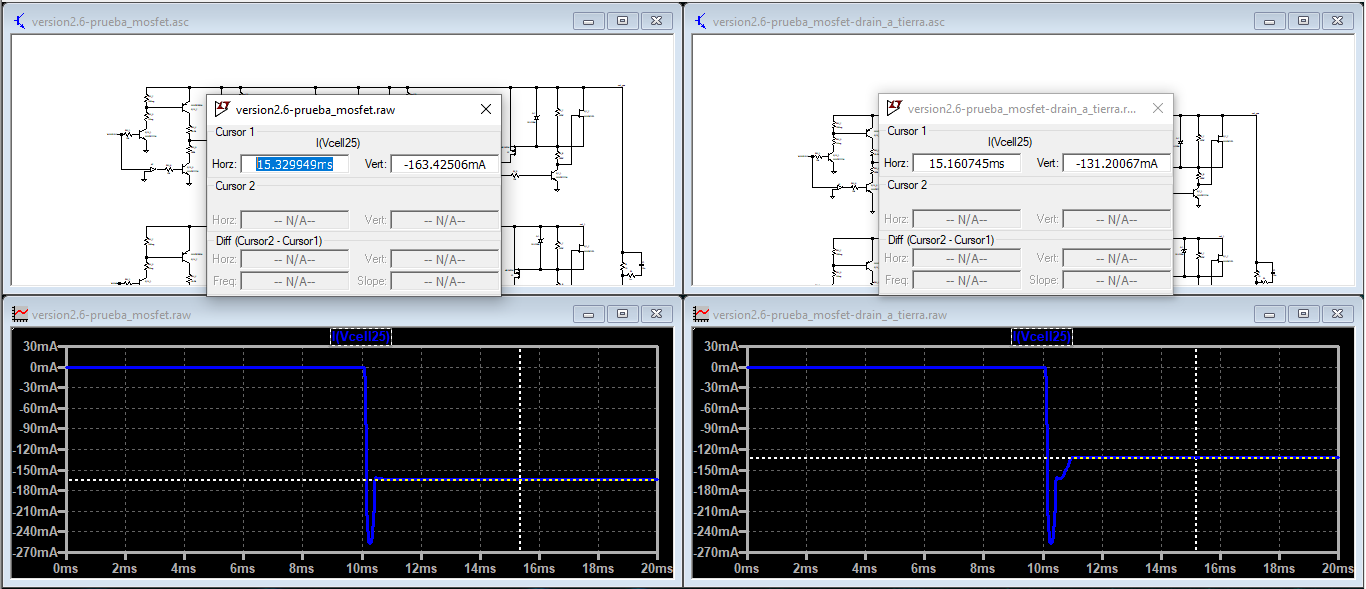
Ltspice/proyectos/matriz_2x2/runs/mosfet_en_tierra/corriente en la celda 25.png
