DeniseViltes/Tesis/media/Curvas/version1.0_corriente y tension.png

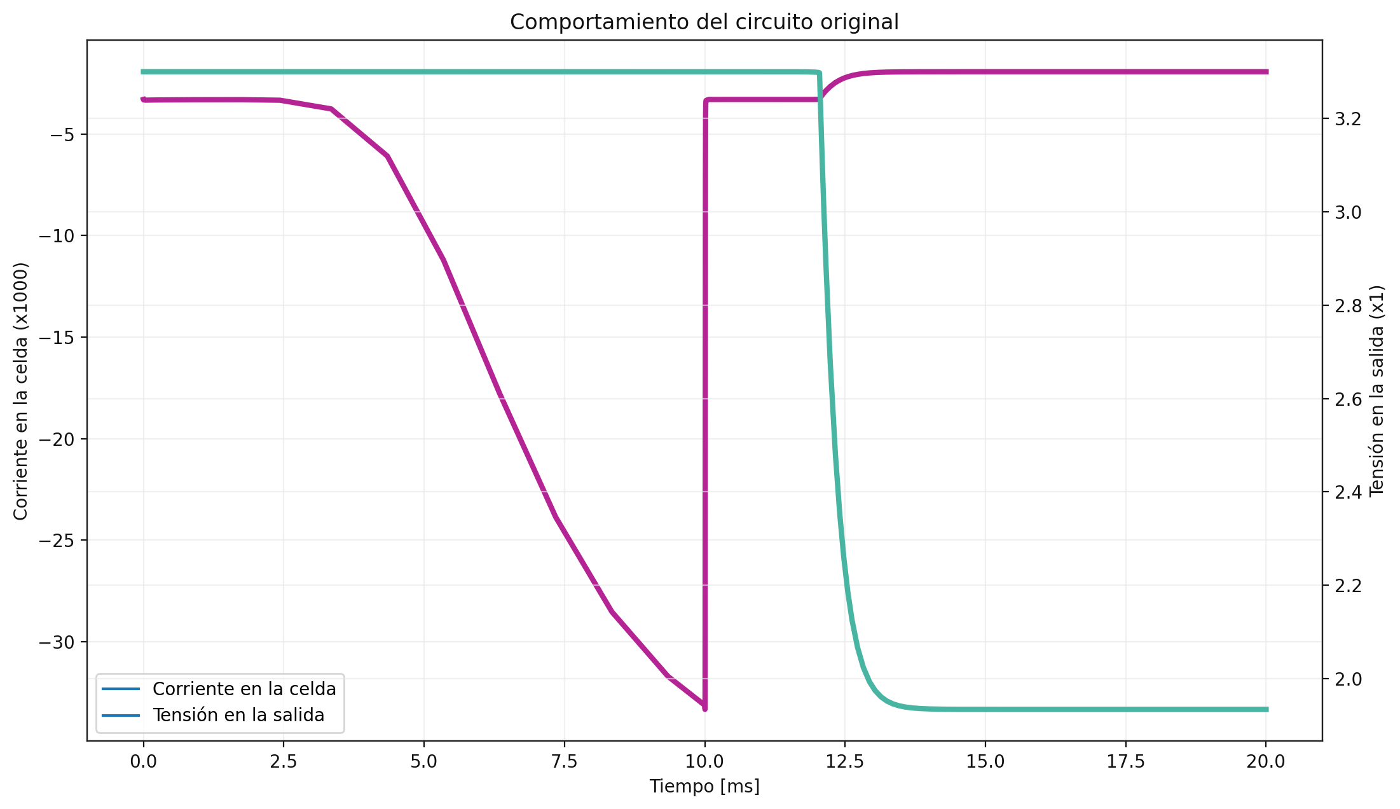
media/Curvas/version1.0_corriente y tension.png
