DeniseViltes/Tesis/media/Esquematicos/circuit.png

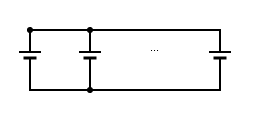
media/Esquematicos/circuit.png
