DeniseViltes/Tesis/media/Esquematicos/Circuito - Con mosfet en la tierra.png

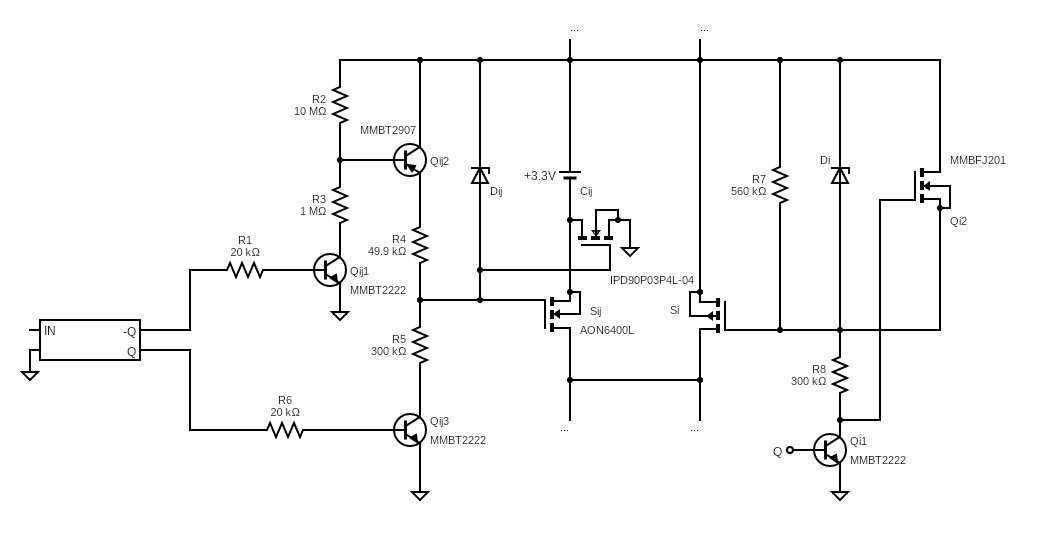
media/Esquematicos/Circuito - Con mosfet en la tierra.png
