DeniseViltes/Tesis/media/Esquematicos/Detalle - Con tierra en la celda.png

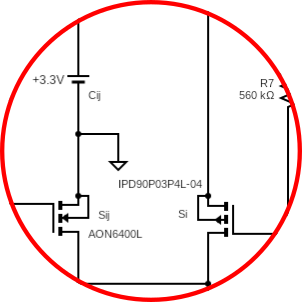
media/Esquematicos/Detalle - Con tierra en la celda.png
