DeniseViltes/Tesis/media/Esquematicos/pmos.png

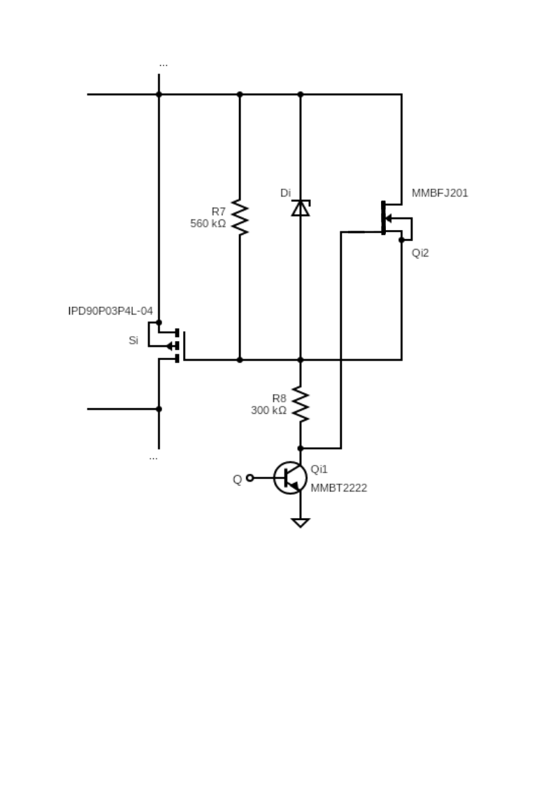
media/Esquematicos/pmos.png
