DeniseViltes/Tesis/media/Latex/Diseño del circuito/1MAS-2MENOS-tensión_de_salida.png

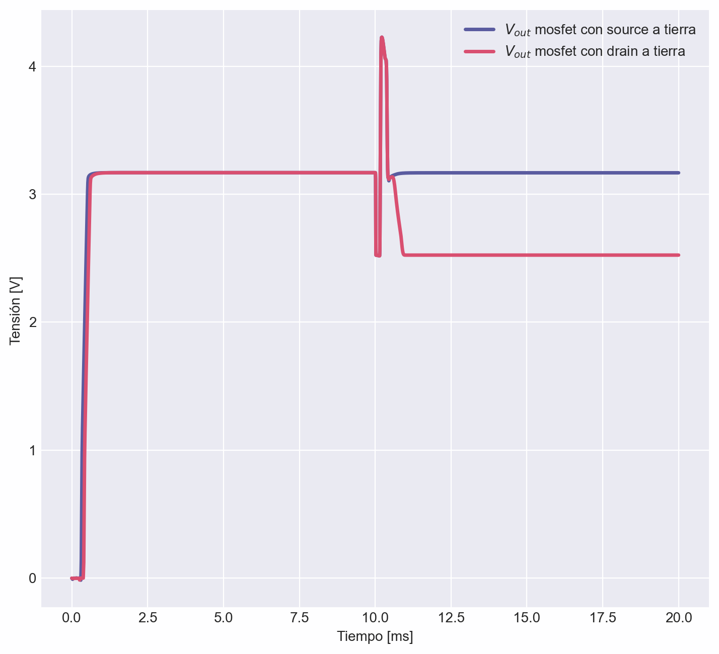
media/Latex/Diseño del circuito/1MAS-2MENOS-tensión_de_salida.png
