DeniseViltes/Tesis/media/Latex/Diseño del circuito/Circuito - Banco Apagado.png

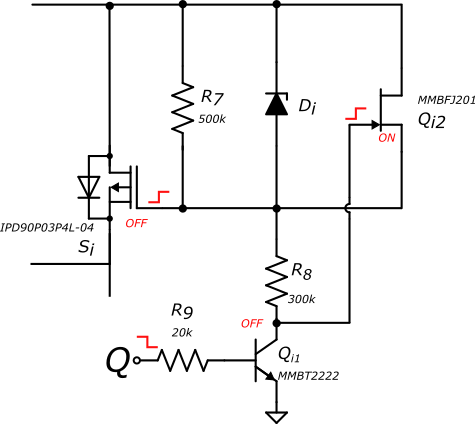
media/Latex/Diseño del circuito/Circuito - Banco Apagado.png
