DeniseViltes/Tesis/media/Latex/Diseño del circuito/Circuito - Celda Apagada.png

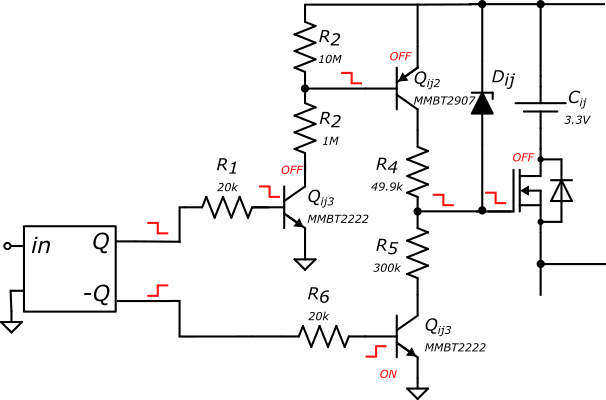
media/Latex/Diseño del circuito/Circuito - Celda Apagada.png
