DeniseViltes/Tesis/media/Latex/Diseño del circuito/Circuito - Original.png

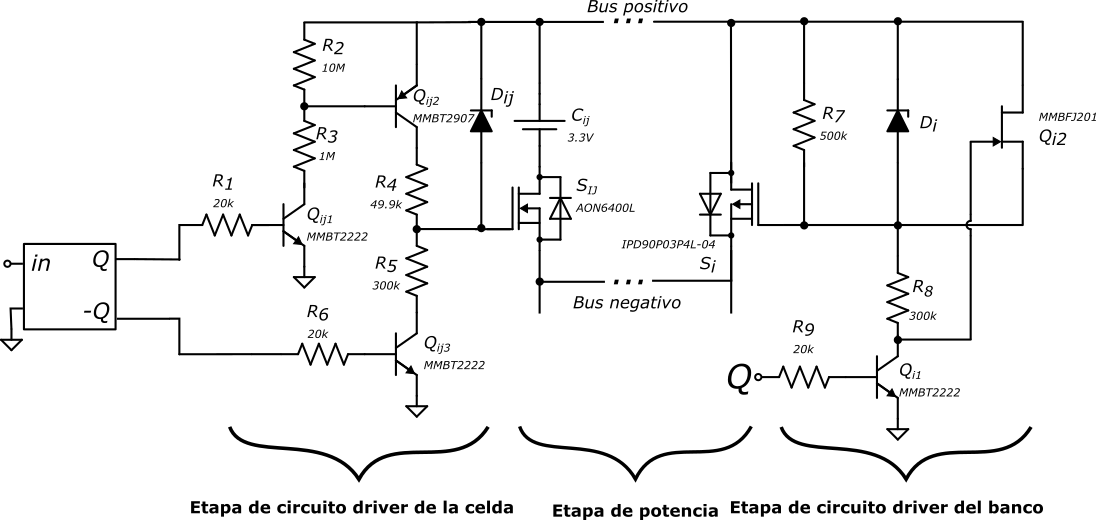
media/Latex/Diseño del circuito/Circuito - Original.png
