DeniseViltes/Tesis/media/Latex/Diseño del circuito/Corriente celda switch - Con zoom y sin delay.png

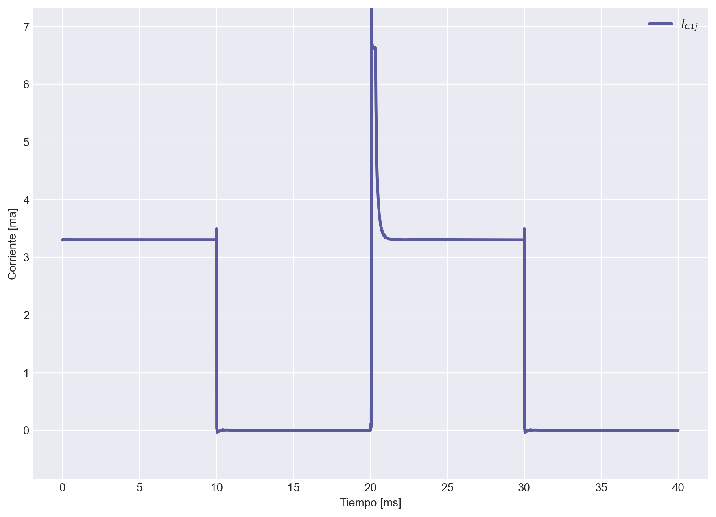
media/Latex/Diseño del circuito/Corriente celda switch - Con zoom y sin delay.png
