DeniseViltes/Tesis/media/Latex/Diseño del circuito/Corriente celda switch - Sin delay.png

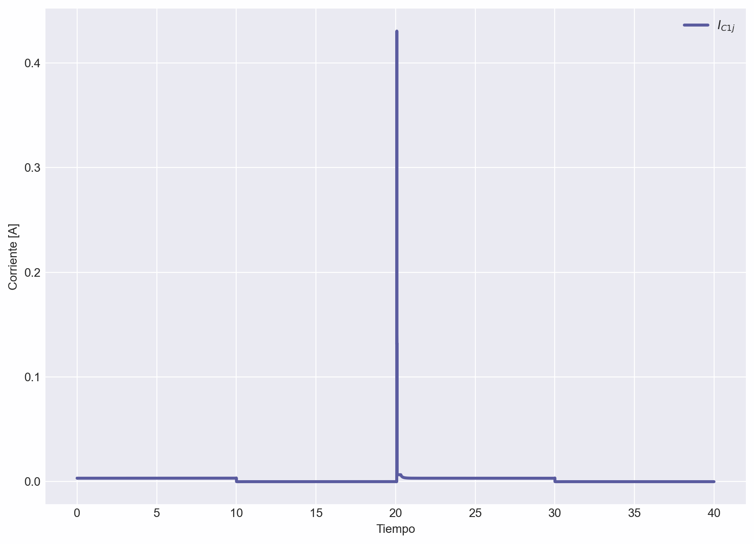
media/Latex/Diseño del circuito/Corriente celda switch - Sin delay.png
