DeniseViltes/Tesis/media/Latex/Diseño del circuito/Detalle - Con resistencia en tierra.png

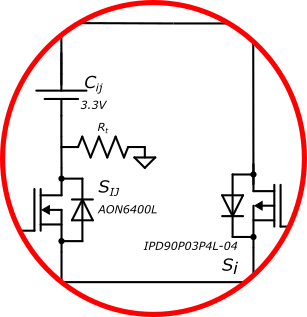
media/Latex/Diseño del circuito/Detalle - Con resistencia en tierra.png
