DeniseViltes/Tesis/media/Latex/Diseño del circuito/Esquema_bateria.png

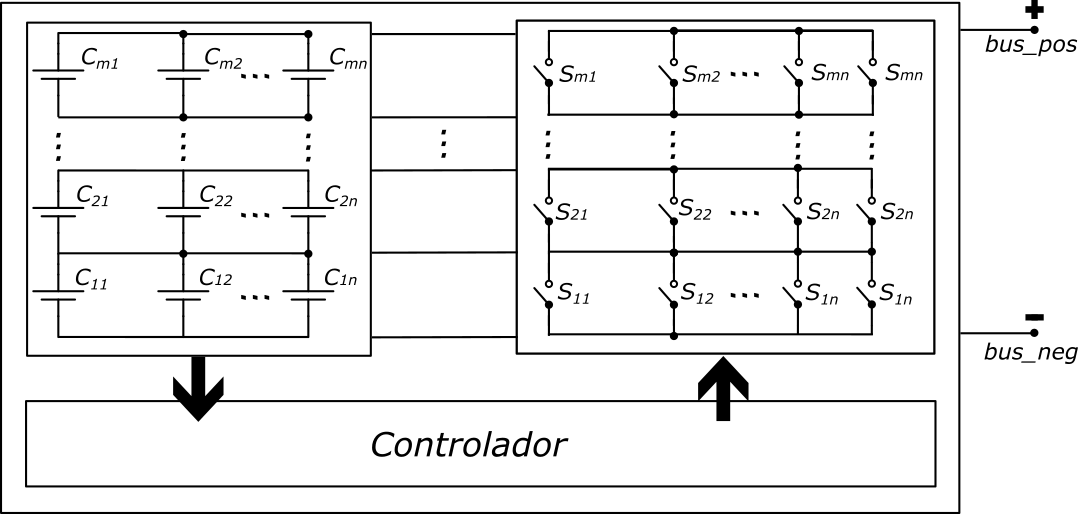
media/Latex/Diseño del circuito/Esquema_bateria.png
