DeniseViltes/Tesis/media/Latex/Diseño del circuito/Matriz de celdas.png

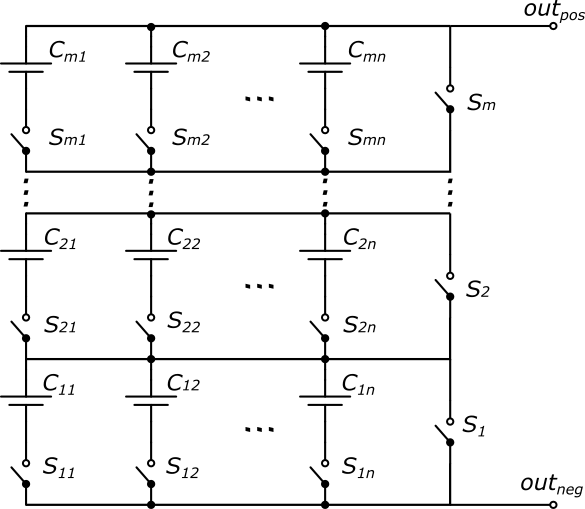
media/Latex/Diseño del circuito/Matriz de celdas.png
