DeniseViltes/Tesis/media/Latex/Diseño del circuito/mediciones para distintas resistencias/1MAS_2MAS-RL_10-corriente_en_tierra.png

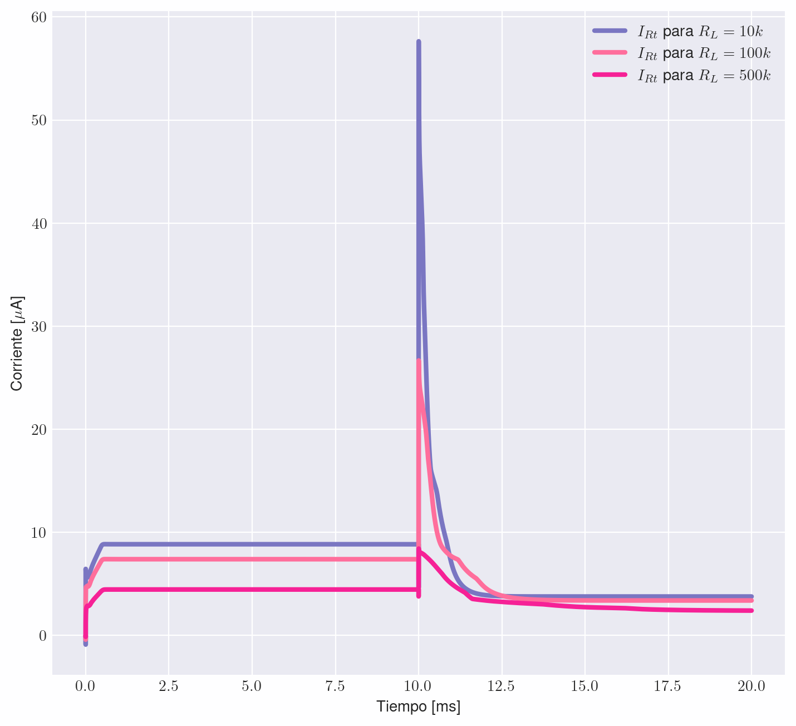
media/Latex/Diseño del circuito/mediciones para distintas resistencias/1MAS_2MAS-RL_10-corriente_en_tierra.png
