DeniseViltes/Tesis/media/Latex/Diseño del circuito/mediciones para distintas resistencias/1MAS_2MAS-RL_10-tension_salida.png

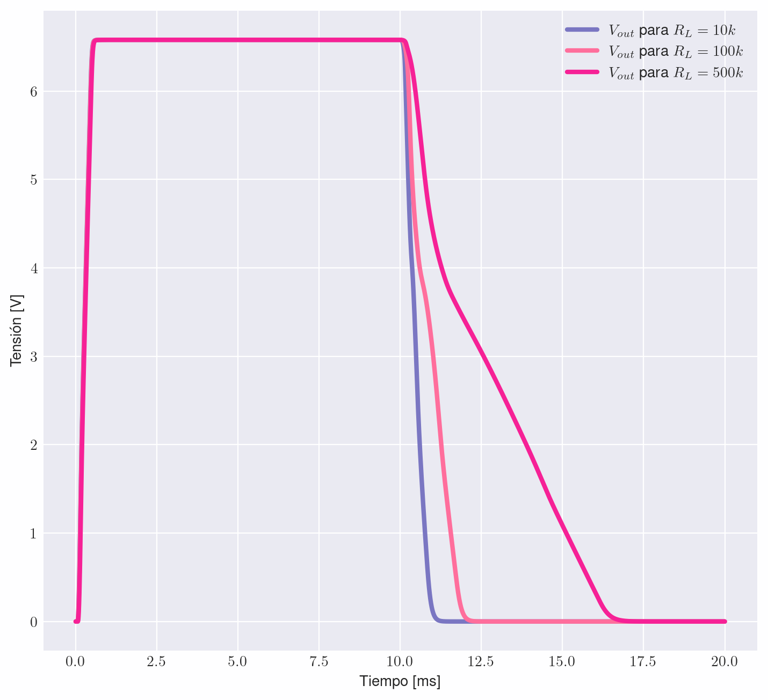
media/Latex/Diseño del circuito/mediciones para distintas resistencias/1MAS_2MAS-RL_10-tension_salida.png
