DeniseViltes/Tesis/media/Latex/Diseño del circuito/mediciones para distintas resistencias/1MAS_2MENOS-RL_10_tension-salida.png

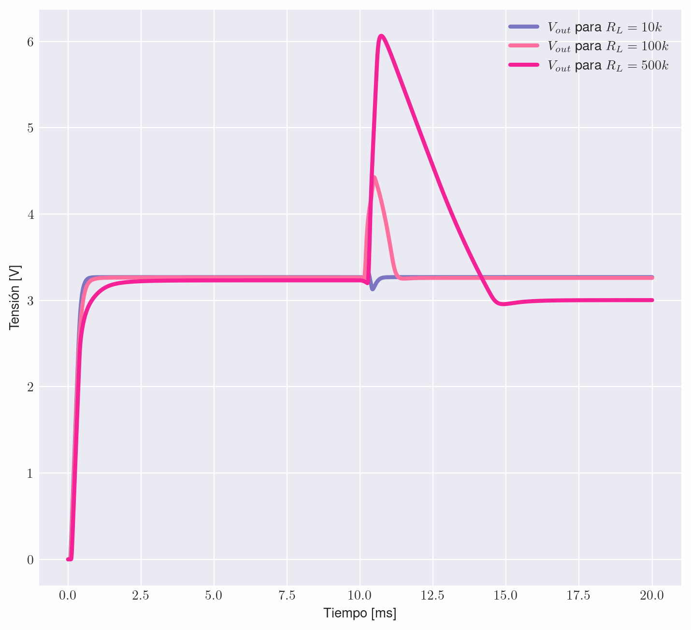
media/Latex/Diseño del circuito/mediciones para distintas resistencias/1MAS_2MENOS-RL_10_tension-salida.png
