DeniseViltes/Tesis/media/Latex/Diseño del circuito/Picos Corriente - Ambos cerrados.png

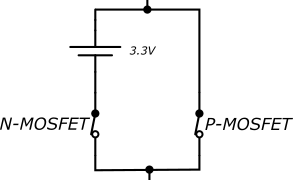
media/Latex/Diseño del circuito/Picos Corriente - Ambos cerrados.png
