DeniseViltes/Tesis/media/Latex/Diseño del circuito/Picos Corriente - PMOS cerrado.png

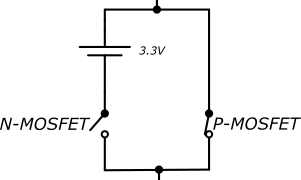
media/Latex/Diseño del circuito/Picos Corriente - PMOS cerrado.png
