DeniseViltes/Tesis/media/Latex/Diseño del circuito/RL_10-corriente_celda.png

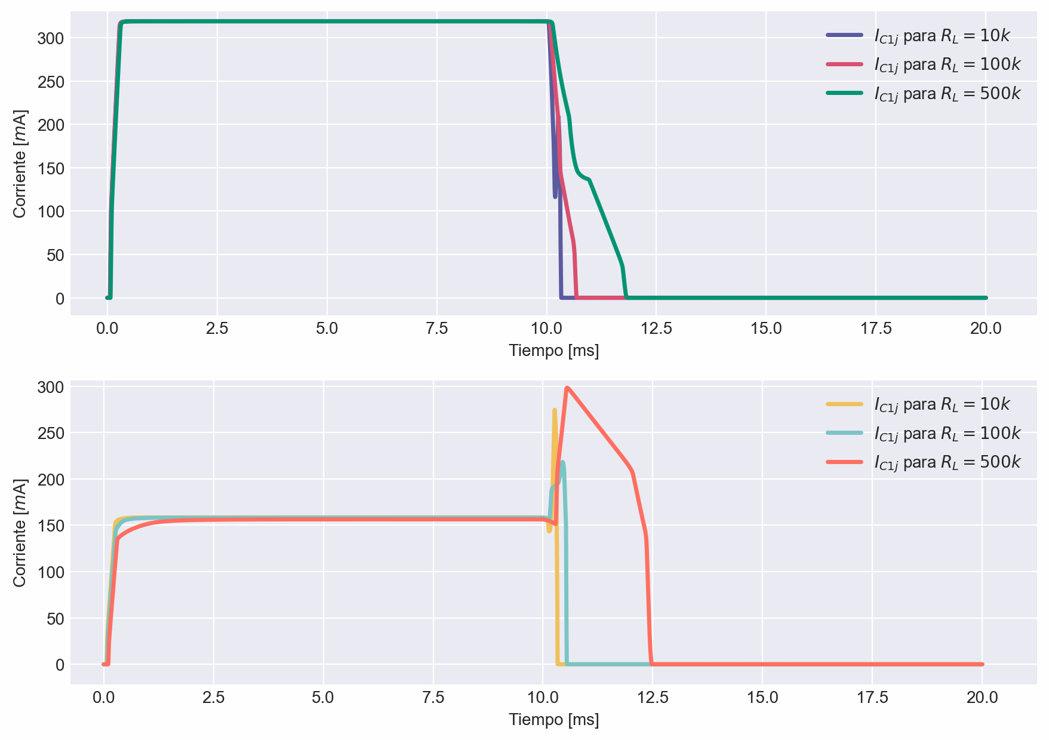
media/Latex/Diseño del circuito/RL_10-corriente_celda.png
