DeniseViltes/Tesis/media/Latex/Diseño del circuito/RL_10-corriente_en_tierra.png

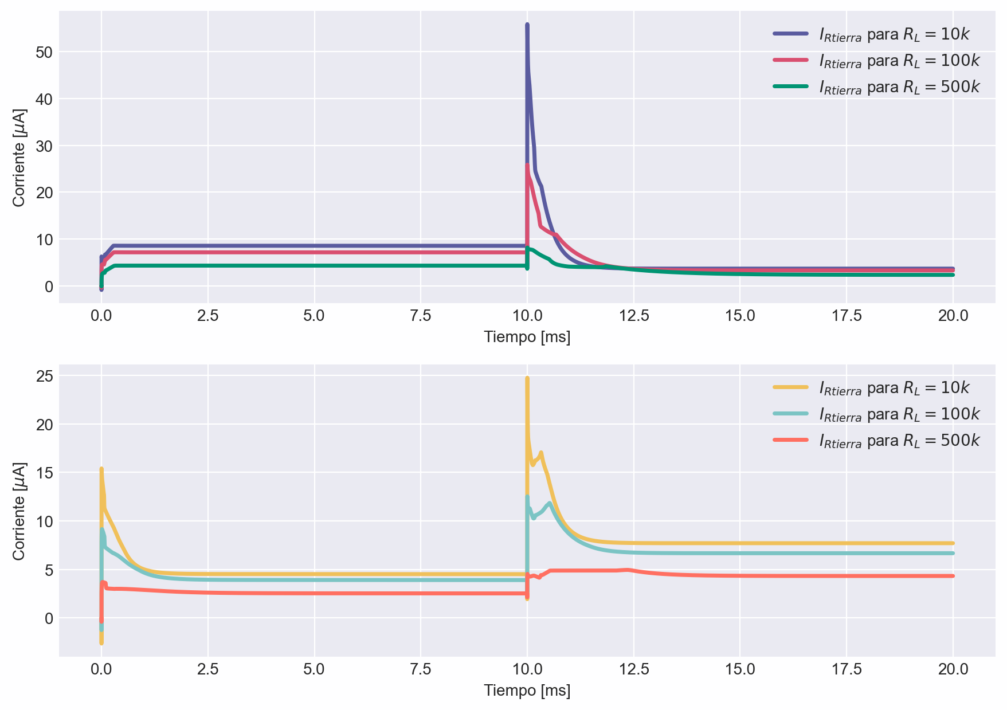
media/Latex/Diseño del circuito/RL_10-corriente_en_tierra.png
