DeniseViltes/Tesis/media/Latex/Diseño del circuito/RL_10-tension_salida.png

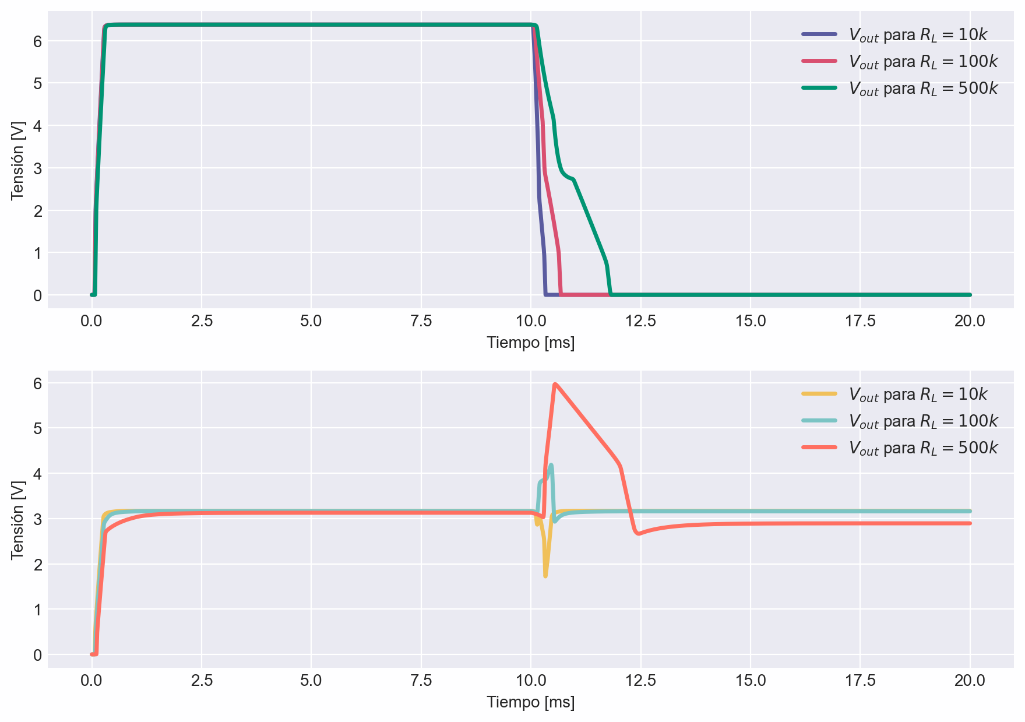
media/Latex/Diseño del circuito/RL_10-tension_salida.png
