DeniseViltes/Tesis/media/Latex/Diseño del circuito/RL_10_corriente_en_tierra.png

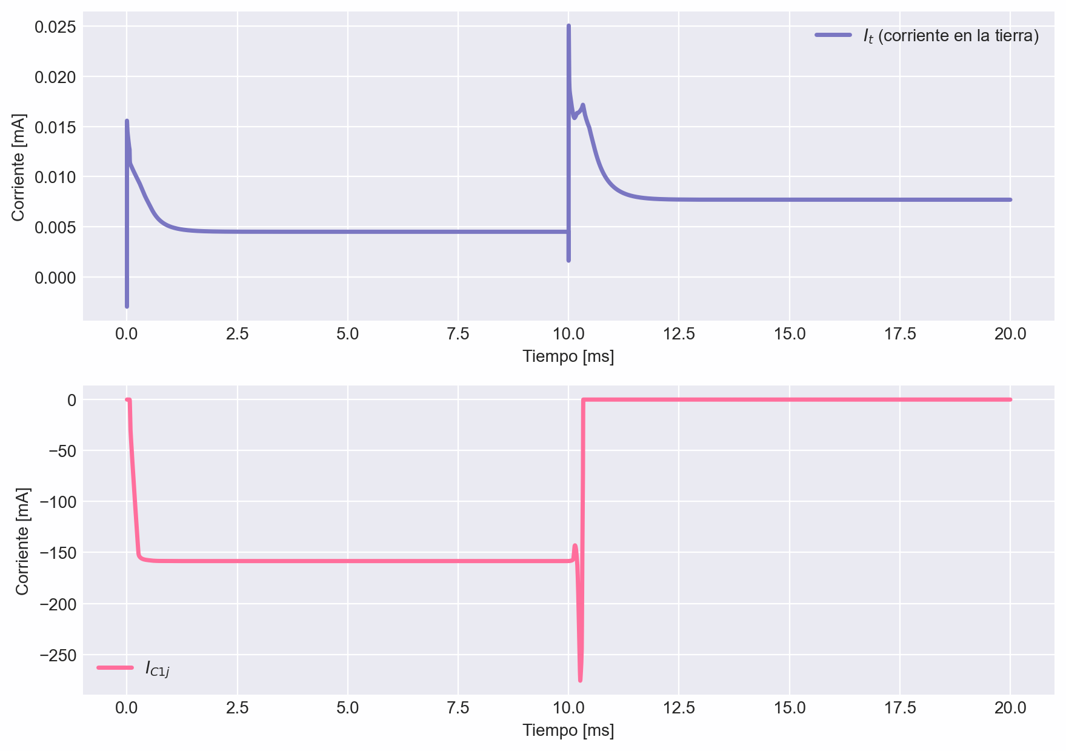
media/Latex/Diseño del circuito/RL_10_corriente_en_tierra.png
