DeniseViltes/Tesis/media/Latex/Diseño del circuito/salida_con_y_sin_cap.png

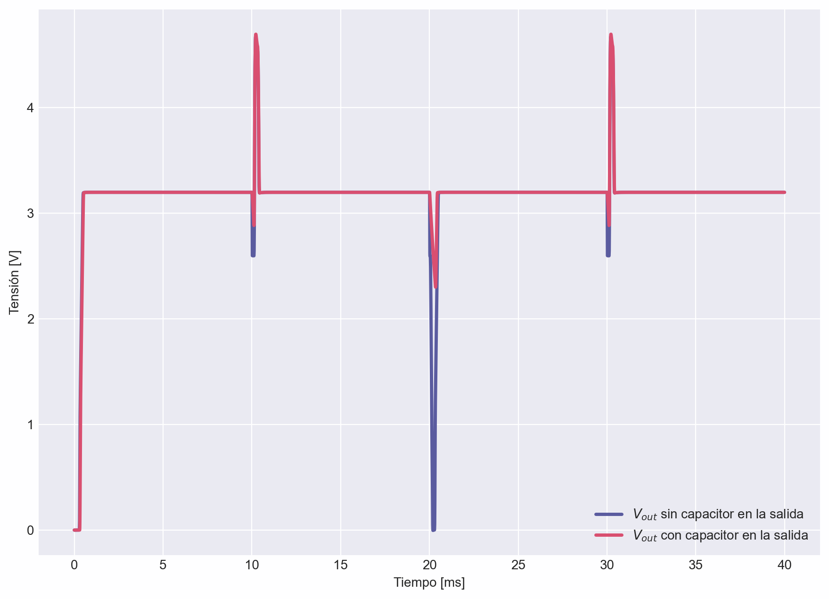
media/Latex/Diseño del circuito/salida_con_y_sin_cap.png
