DeniseViltes/Tesis/media/Latex/Introducción/Diagrama de flujos global - Metodología de trabajo.png

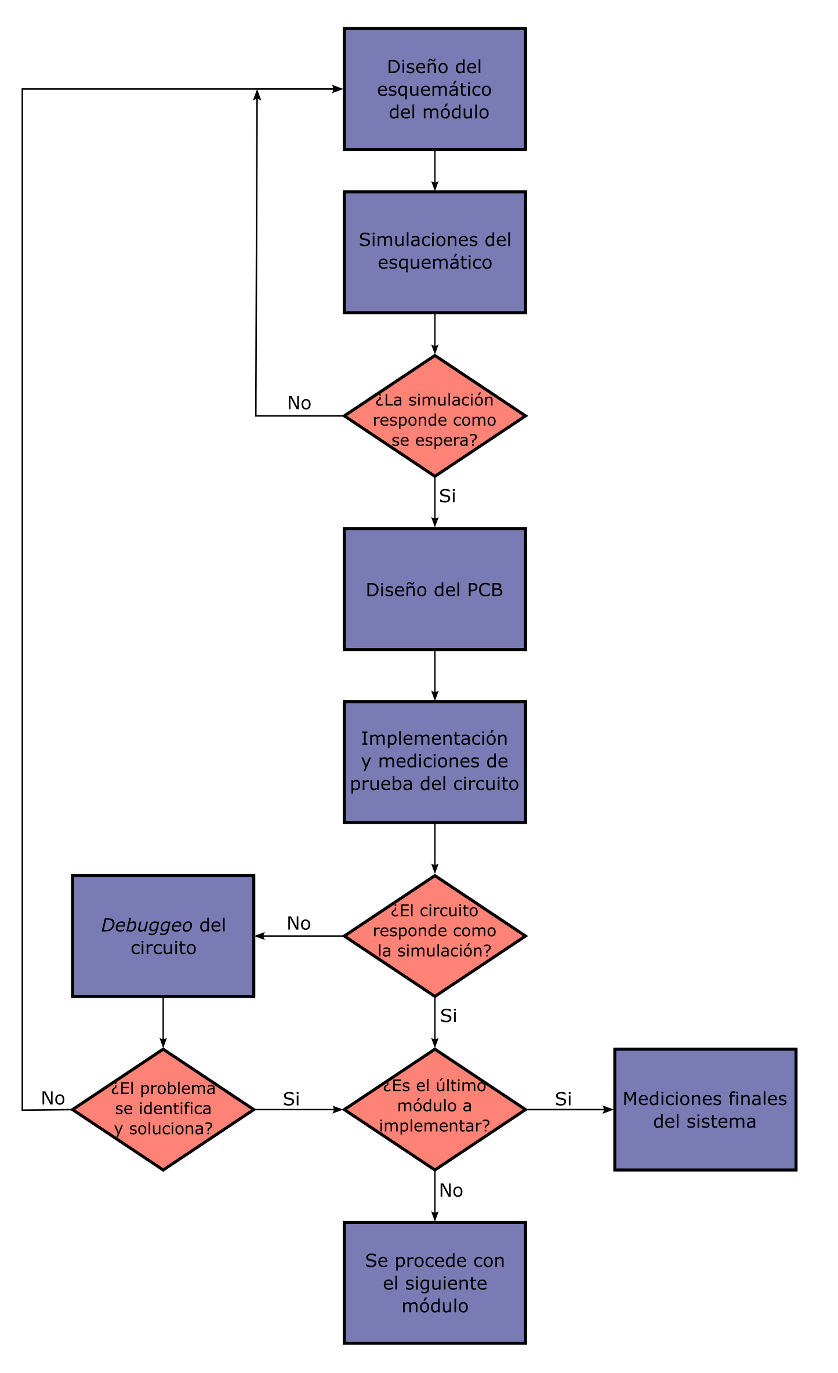
media/Latex/Introducción/Diagrama de flujos global - Metodología de trabajo.png
