DeniseViltes/Tesis/media/Latex/Introducción/Diagrama de flujos implementación - Metodología de trabajo.png

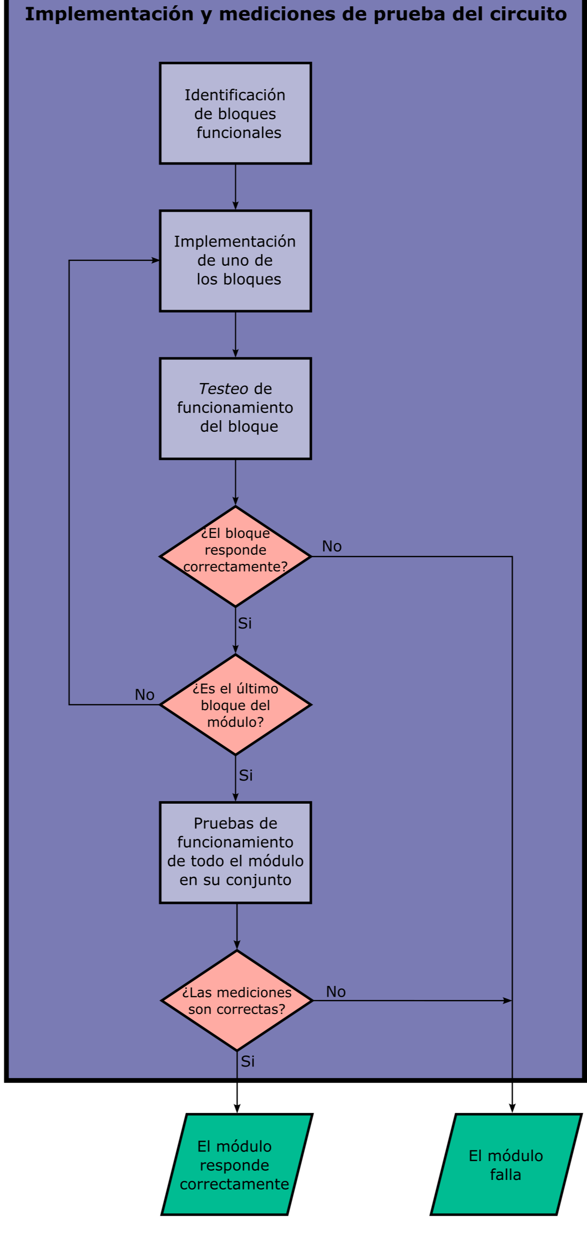
media/Latex/Introducción/Diagrama de flujos implementación - Metodología de trabajo.png
