DeniseViltes/Tesis/media/Latex/Prototipo/bloque-banco.png

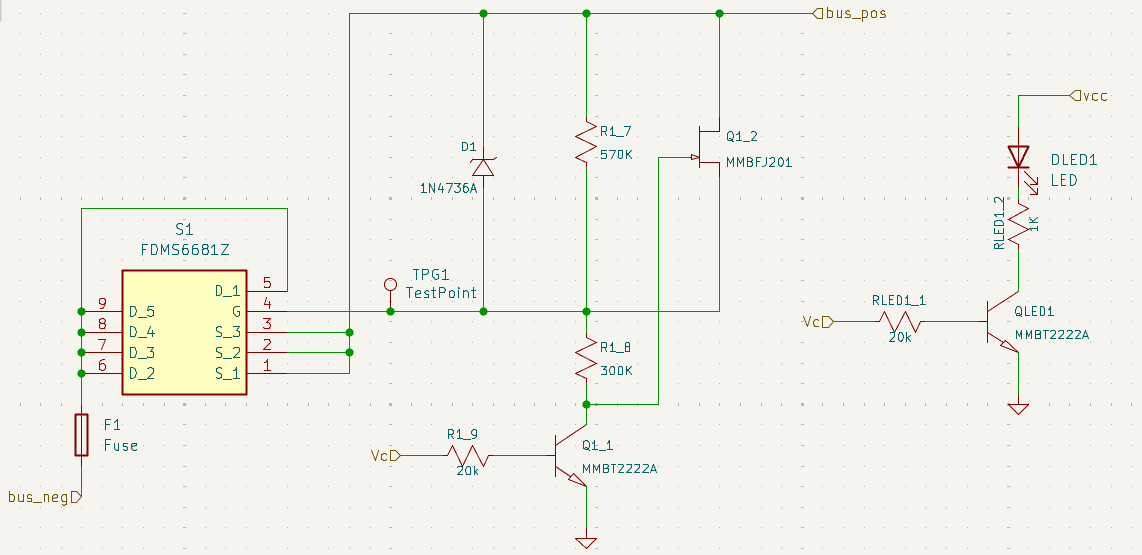
media/Latex/Prototipo/bloque-banco.png
