DeniseViltes/Tesis/media/Latex/Prototipo/bloque-celda.png

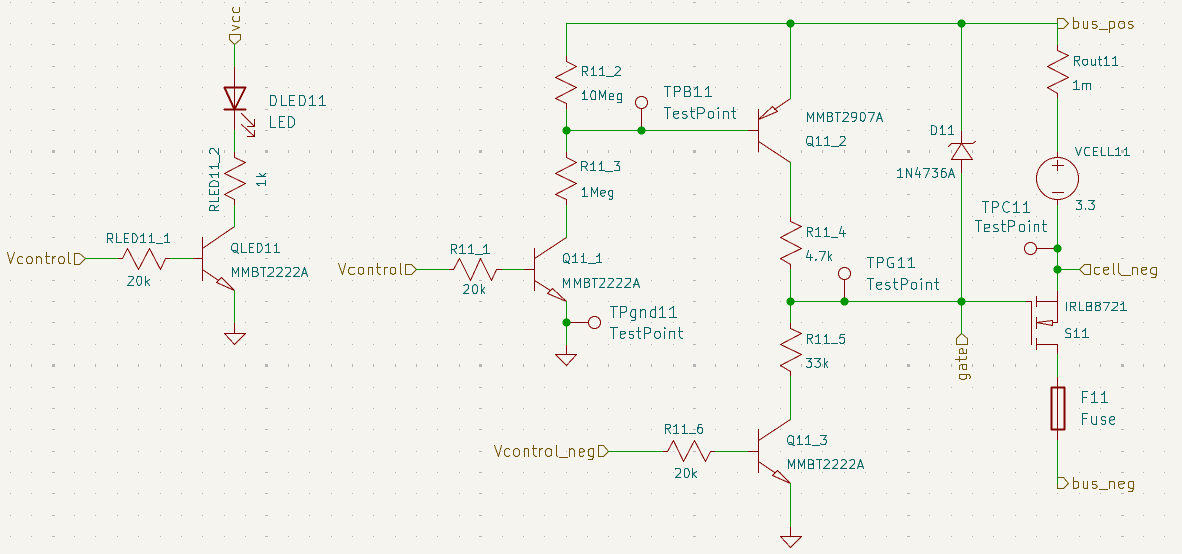
media/Latex/Prototipo/bloque-celda.png
