DeniseViltes/Tesis/media/Latex/Prototipo/bloques.png

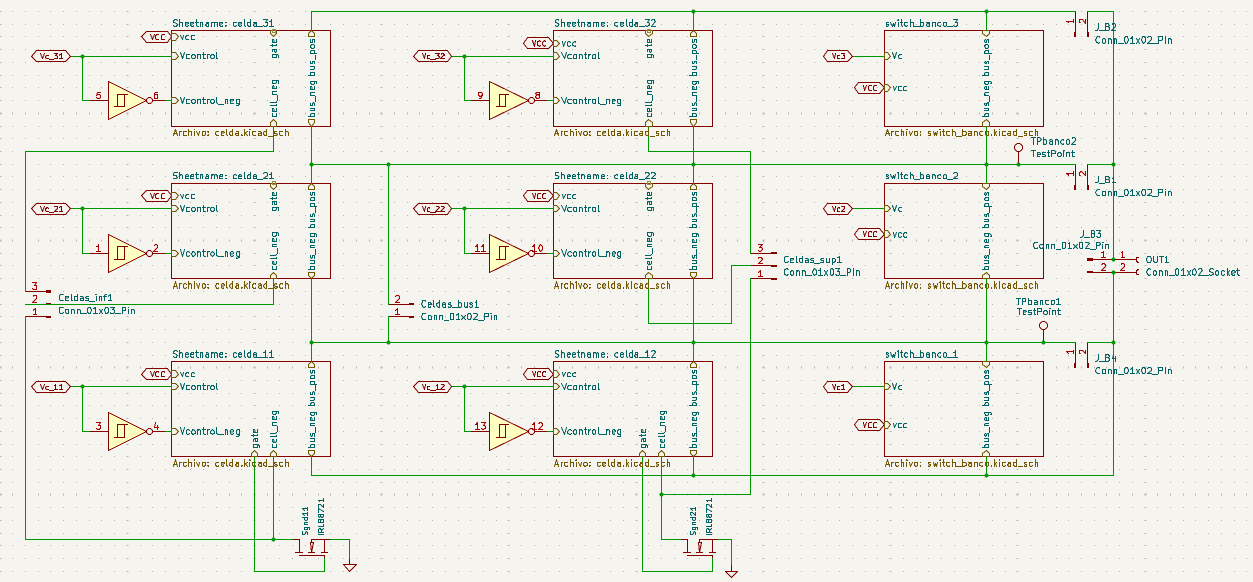
media/Latex/Prototipo/bloques.png
