DeniseViltes/Tesis/media/Latex/Prototipo/Esquematico prototipo.png

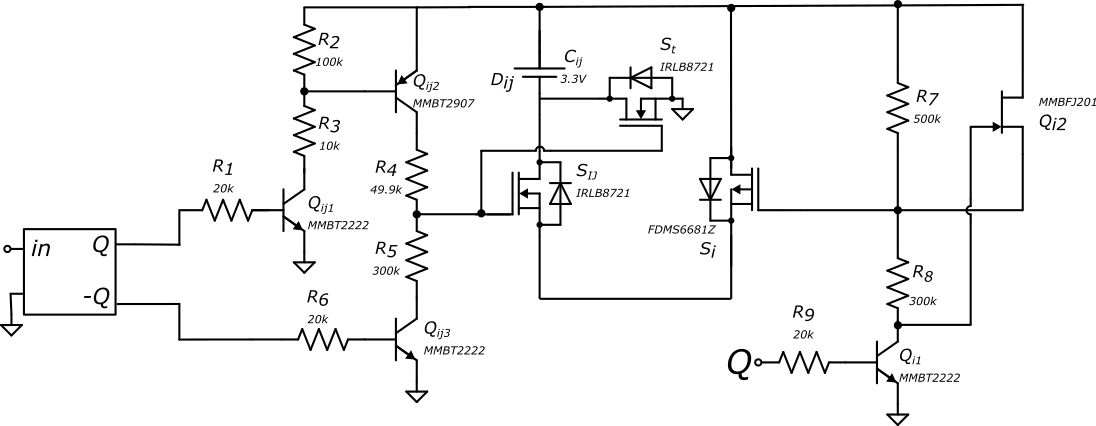
media/Latex/Prototipo/Esquematico prototipo.png
