DeniseViltes/Tesis/media/Latex/Prototipo/organización-prototipo.png

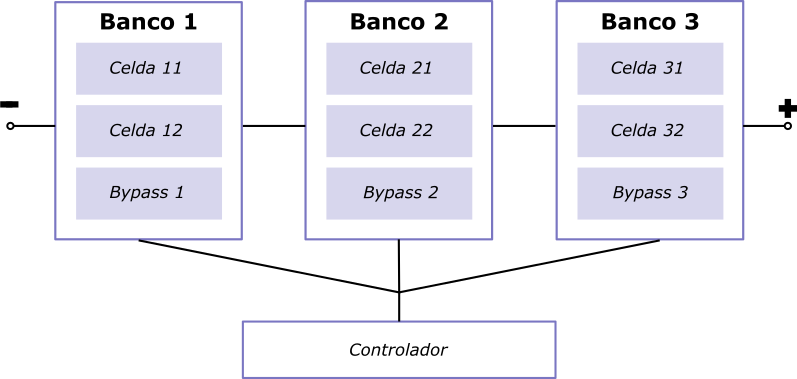
media/Latex/Prototipo/organización-prototipo.png
