DeniseViltes/Tesis/media/Latex/Prototipo/prototipo_3d_FRONT.png

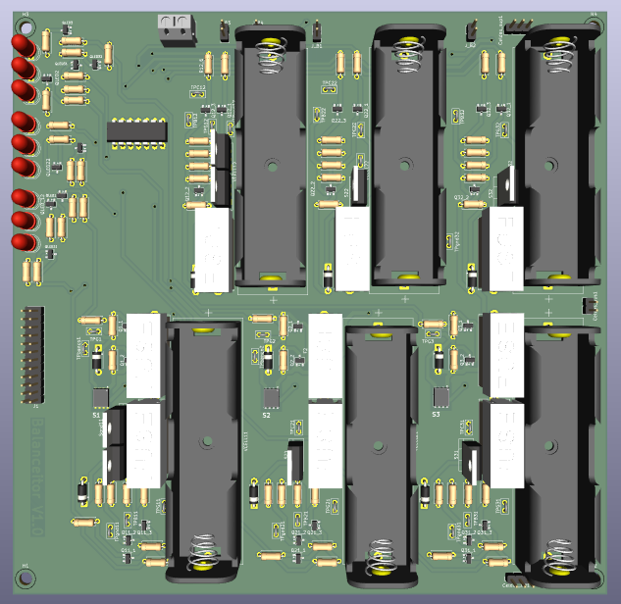
media/Latex/Prototipo/prototipo_3d_FRONT.png
