DeniseViltes/Tesis/media/Latex/Prototipo/prototipo_3d_ISOMETRICA.png

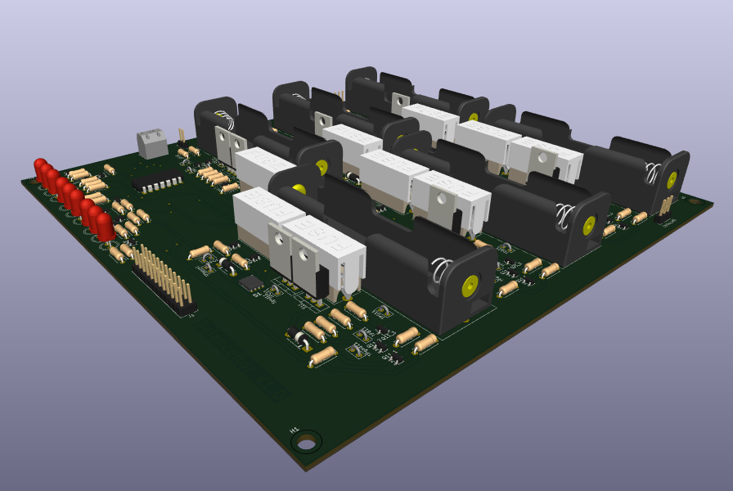
media/Latex/Prototipo/prototipo_3d_ISOMETRICA.png
