DeniseViltes/Tesis/media/Latex/Prototipo/prototipo_PCB.png

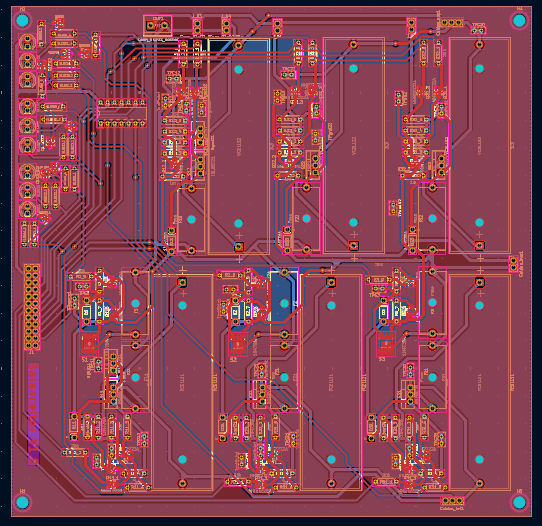
media/Latex/Prototipo/prototipo_PCB.png
