DeniseViltes/Tesis/media/Latex/Prototipo/sistema_completo.png

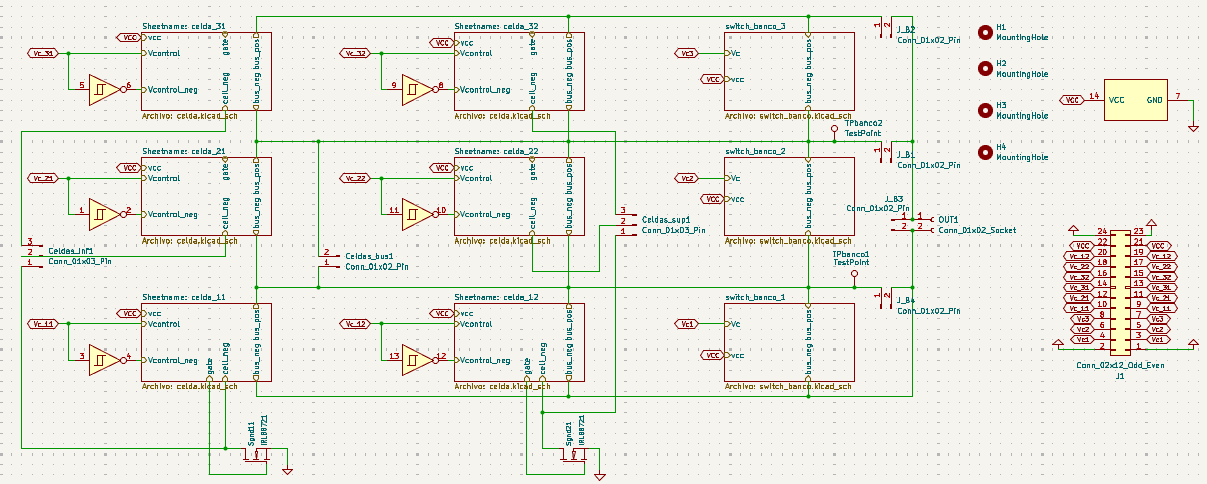
media/Latex/Prototipo/sistema_completo.png
