DeniseViltes/Tesis/media/Latex/Prototipo/sw_bancos_sincronizados.png

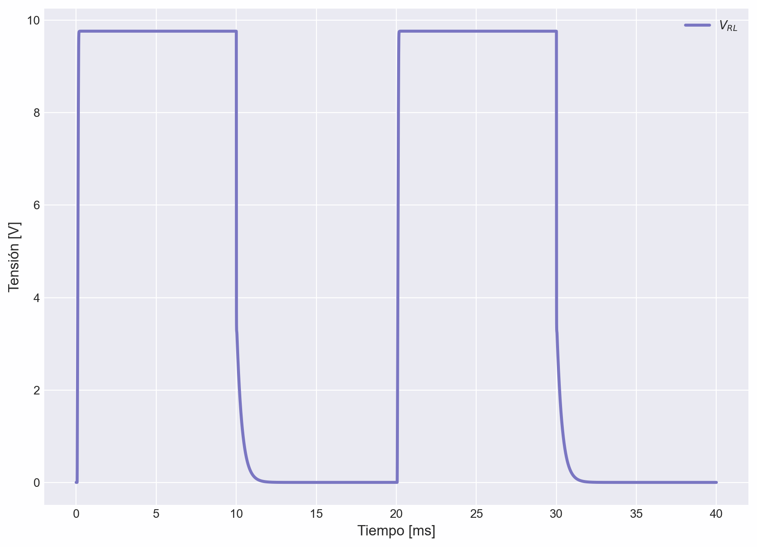
media/Latex/Prototipo/sw_bancos_sincronizados.png
