DeniseViltes/Tesis/media/Latex/Prototipo/sw_entre_celdas.png

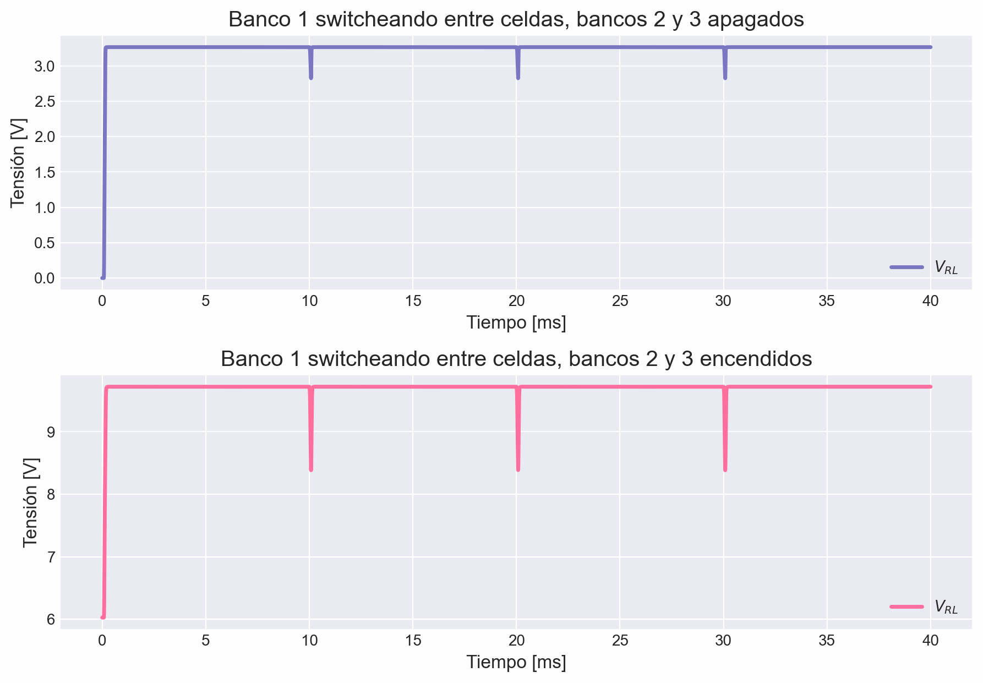
media/Latex/Prototipo/sw_entre_celdas.png
