DeniseViltes/Tesis/media/Latex/Prototipo/tensiones de salida.png

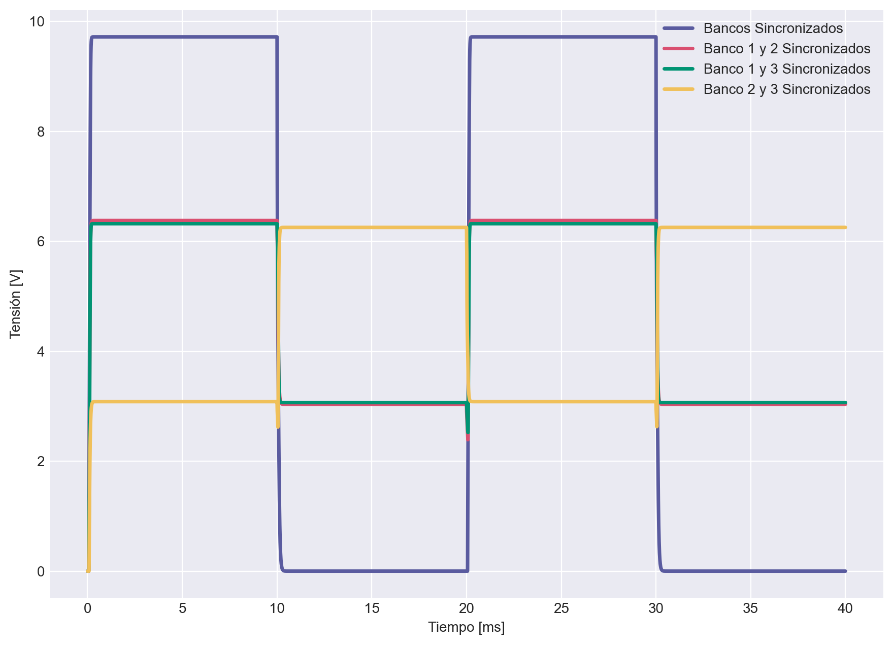
media/Latex/Prototipo/tensiones de salida.png
