DeniseViltes/Tesis/media/Latex/Prototipo/Trace-Width-Calculator.jpg

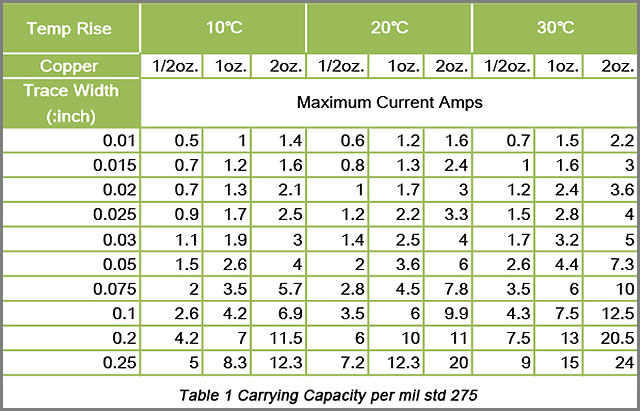
media/Latex/Prototipo/Trace-Width-Calculator.jpg
