DeniseViltes/Tesis/media/PCB/WhatsApp Image 2026-02-02 at 17.44.40.jpeg

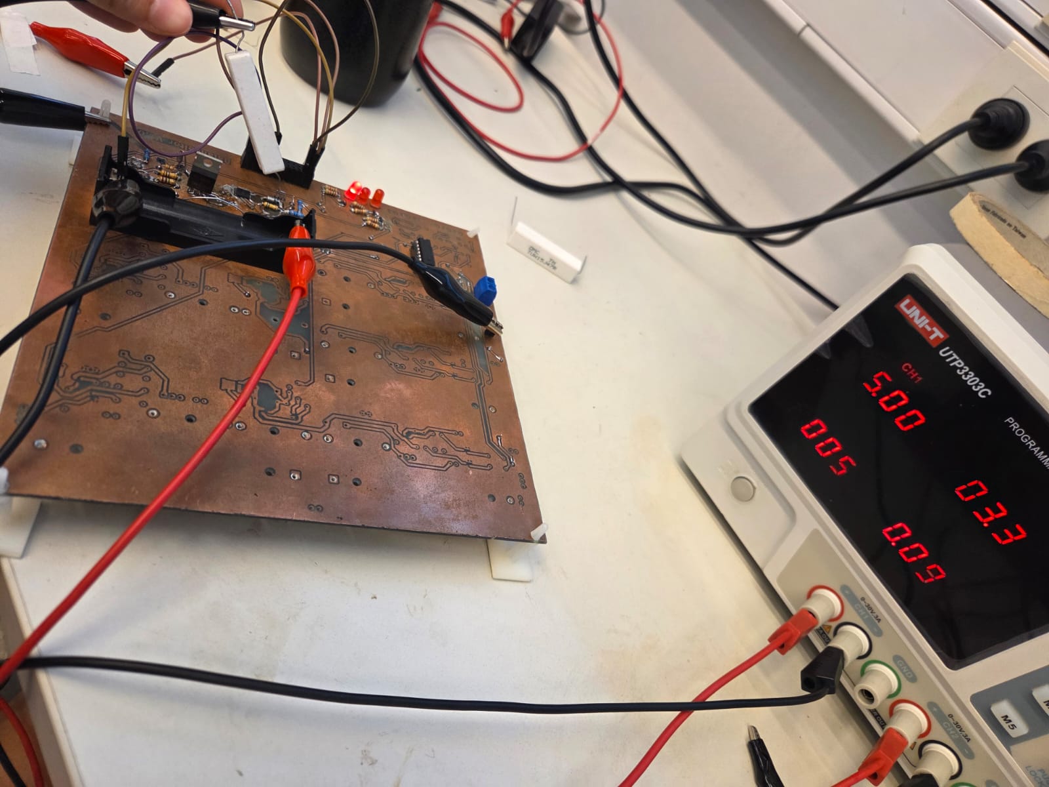
media/PCB/WhatsApp Image 2026-02-02 at 17.44.40.jpeg
