DeniseViltes/Tesis/media/Pila dibujito - Blanco y negro.png

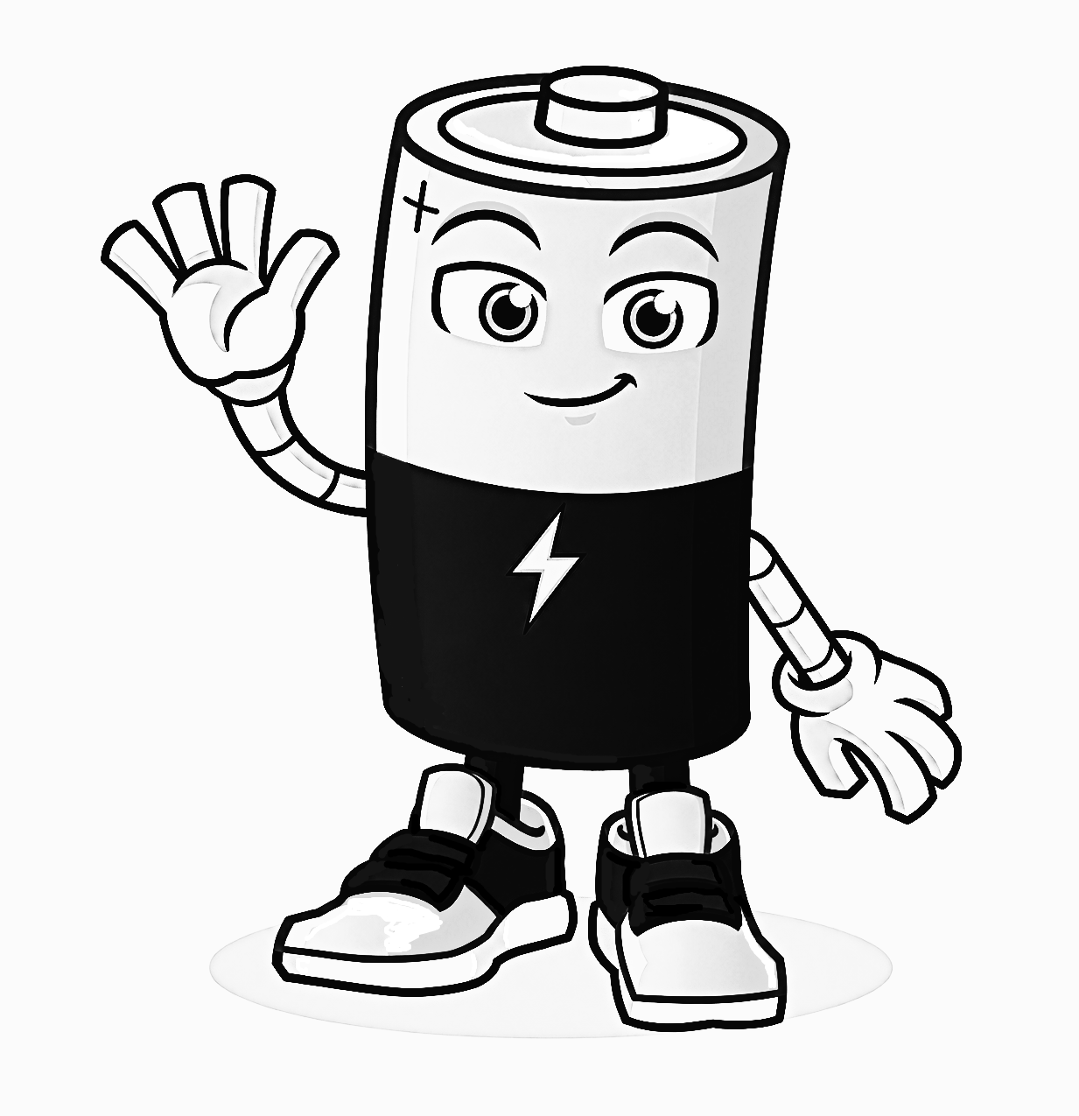
media/Pila dibujito - Blanco y negro.png
