DeniseViltes/Tesis/media/Pila dibujito.png

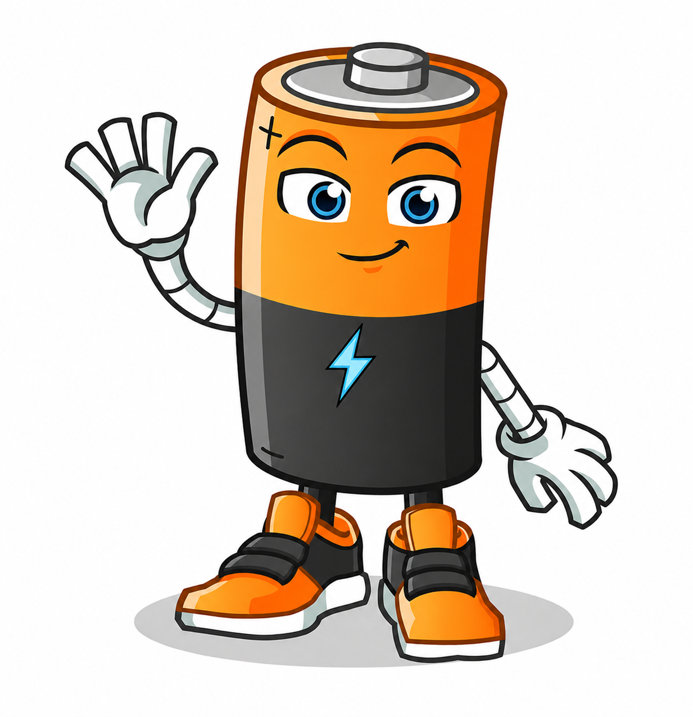
media/Pila dibujito.png
