DeniseViltes/Tesis/media/Simbolos/Circuito - Original.png

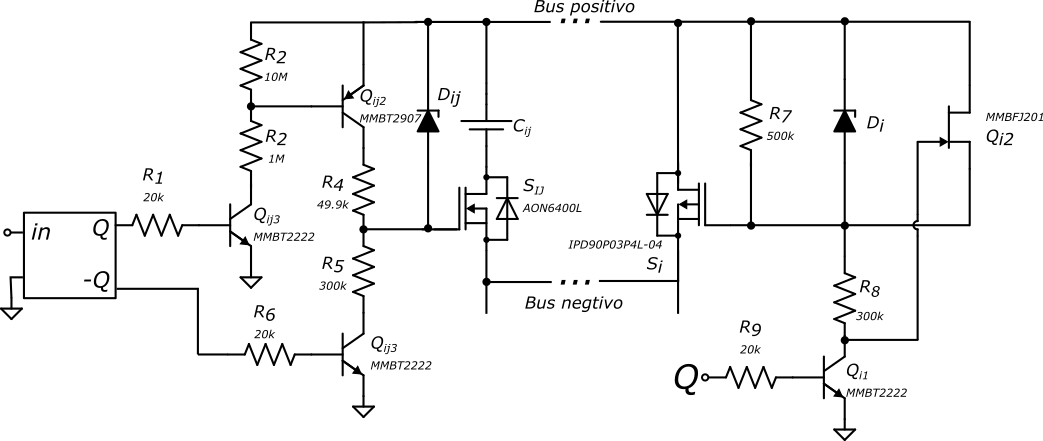
media/Simbolos/Circuito - Original.png
