DeniseViltes/Tesis/media/Simbolos/images/image1.png

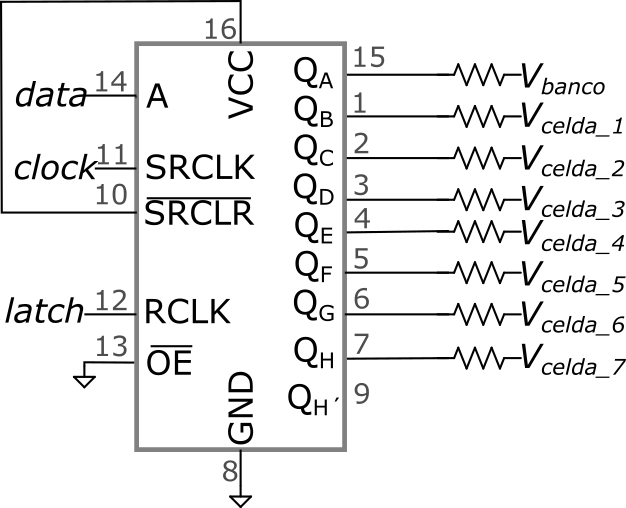
media/Simbolos/images/image1.png
