DeniseViltes/Tesis/Mediciones/Circuito final/Celda 2.1/Mediciones 2.1 con resistores corregidos.png

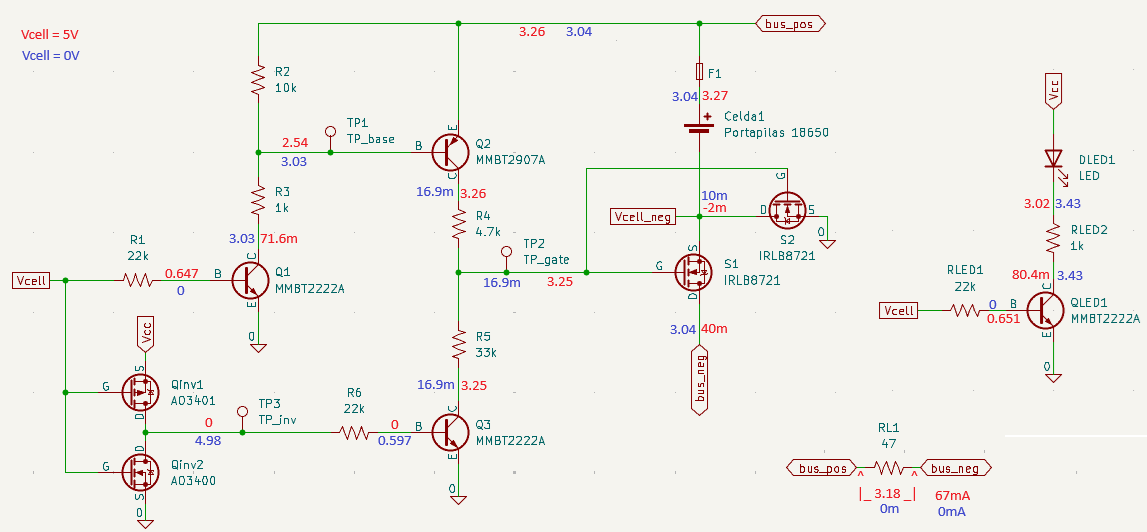
Mediciones/Circuito final/Celda 2.1/Mediciones 2.1 con resistores corregidos.png
