DeniseViltes/Tesis/Mediciones/Circuito final/Shift Register/74HC595-Shift-Register-Pinout-610x424.png

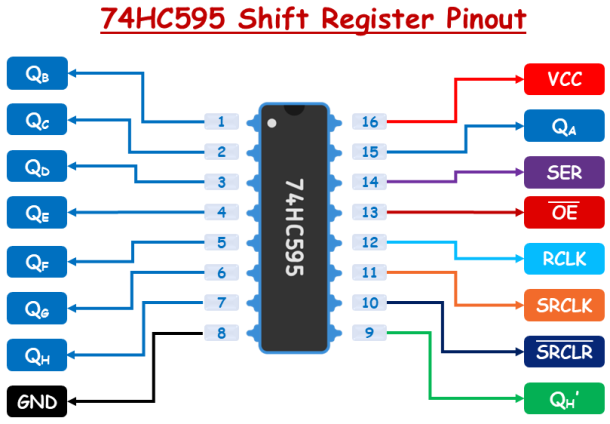
Mediciones/Circuito final/Shift Register/74HC595-Shift-Register-Pinout-610x424.png
