DeniseViltes/Tesis/Mediciones/Circuito final/Shift Register/74HC595-Shift-Register-Working-Data-Latched.png

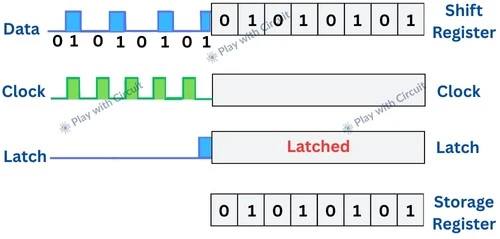
Mediciones/Circuito final/Shift Register/74HC595-Shift-Register-Working-Data-Latched.png
