DeniseViltes/Tesis/Mediciones/Circuito final/Shift Register/Captura de pantalla 2026-05-20 122244.png

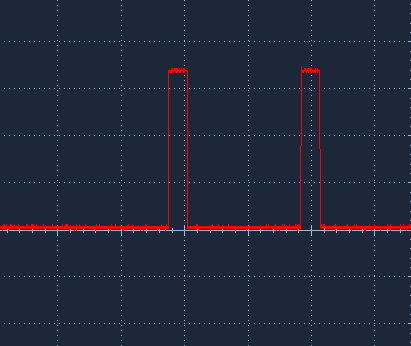
Mediciones/Circuito final/Shift Register/Captura de pantalla 2026-05-20 122244.png
