DeniseViltes/Tesis/Mediciones/Circuito final/Shift Register/Captura de pantalla 2026-05-20 125704.png

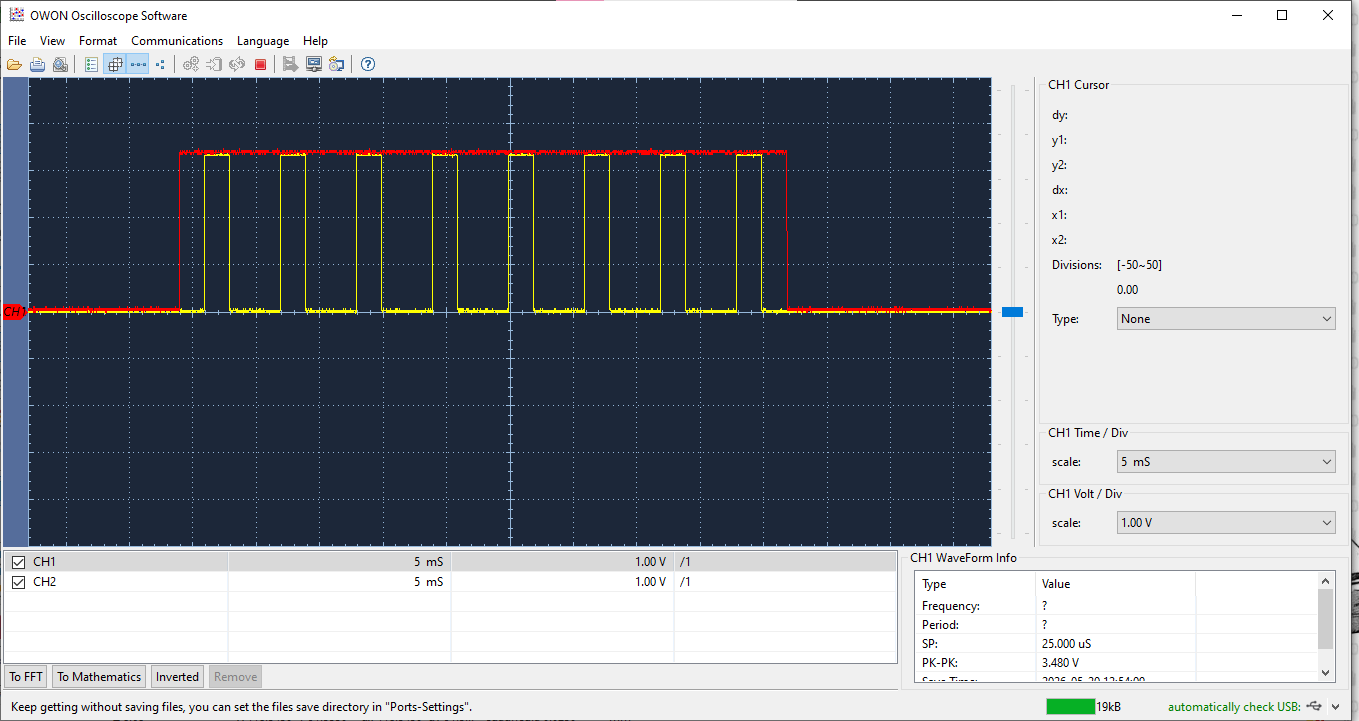
Mediciones/Circuito final/Shift Register/Captura de pantalla 2026-05-20 125704.png
