DeniseViltes/Tesis/Mediciones/Circuito final/Switching de 1 banco/sw - 2 bancos - 1 celda cada - sin delays en el control.png

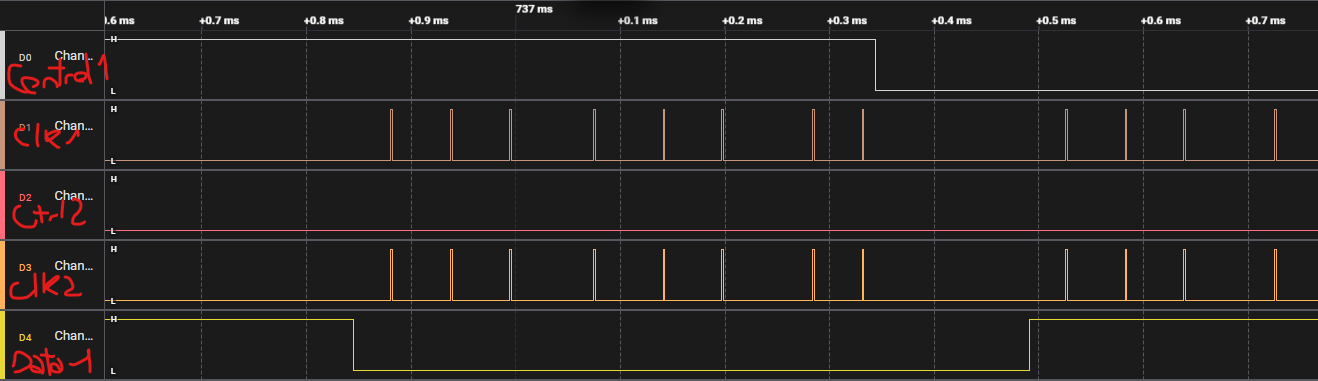
Mediciones/Circuito final/Switching de 1 banco/sw - 2 bancos - 1 celda cada - sin delays en el control.png
