DeniseViltes/Tesis/Mediciones/Circuito final/Switching de 2 bancos/sw logico - salida SR celdas - 2 bancos - 1 celda c u - con delay entre señales - ancho entre pulsos clk.png

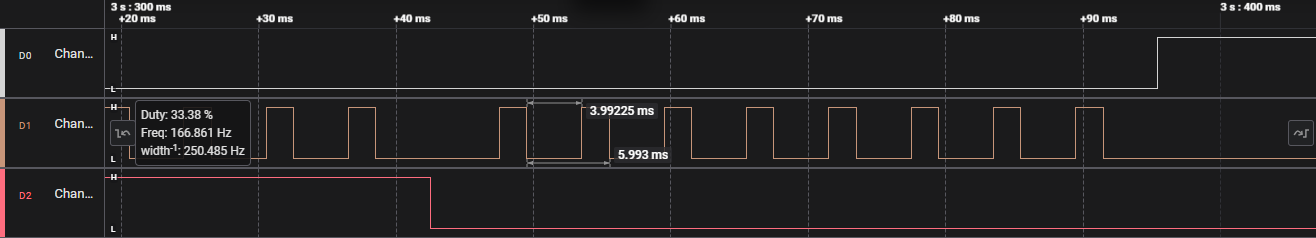
Mediciones/Circuito final/Switching de 2 bancos/sw logico - salida SR celdas - 2 bancos - 1 celda c u - con delay entre señales - ancho entre pulsos clk.png
