DeniseViltes/Tesis/Mediciones/Circuito final/Switching de 2 bancos/sw logico - salida SR celdas - 2 bancos - 1 celda c u - sin delay en el SR entre señales - con zoom 2.png

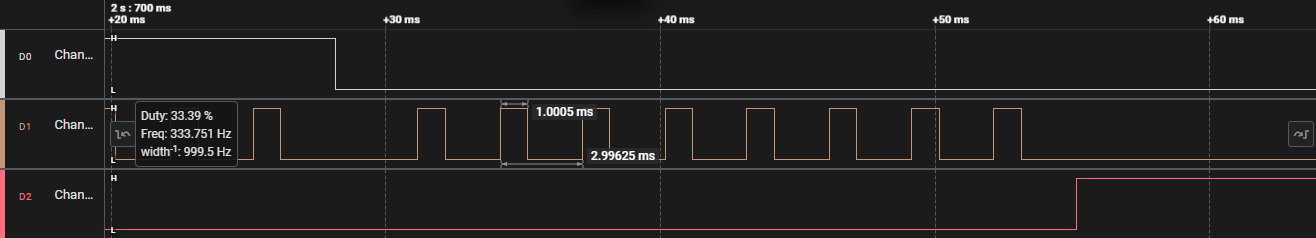
Mediciones/Circuito final/Switching de 2 bancos/sw logico - salida SR celdas - 2 bancos - 1 celda c u - sin delay en el SR entre señales - con zoom 2.png
