DeniseViltes/Tesis/Mediciones/Notes_260204_163819.jpg

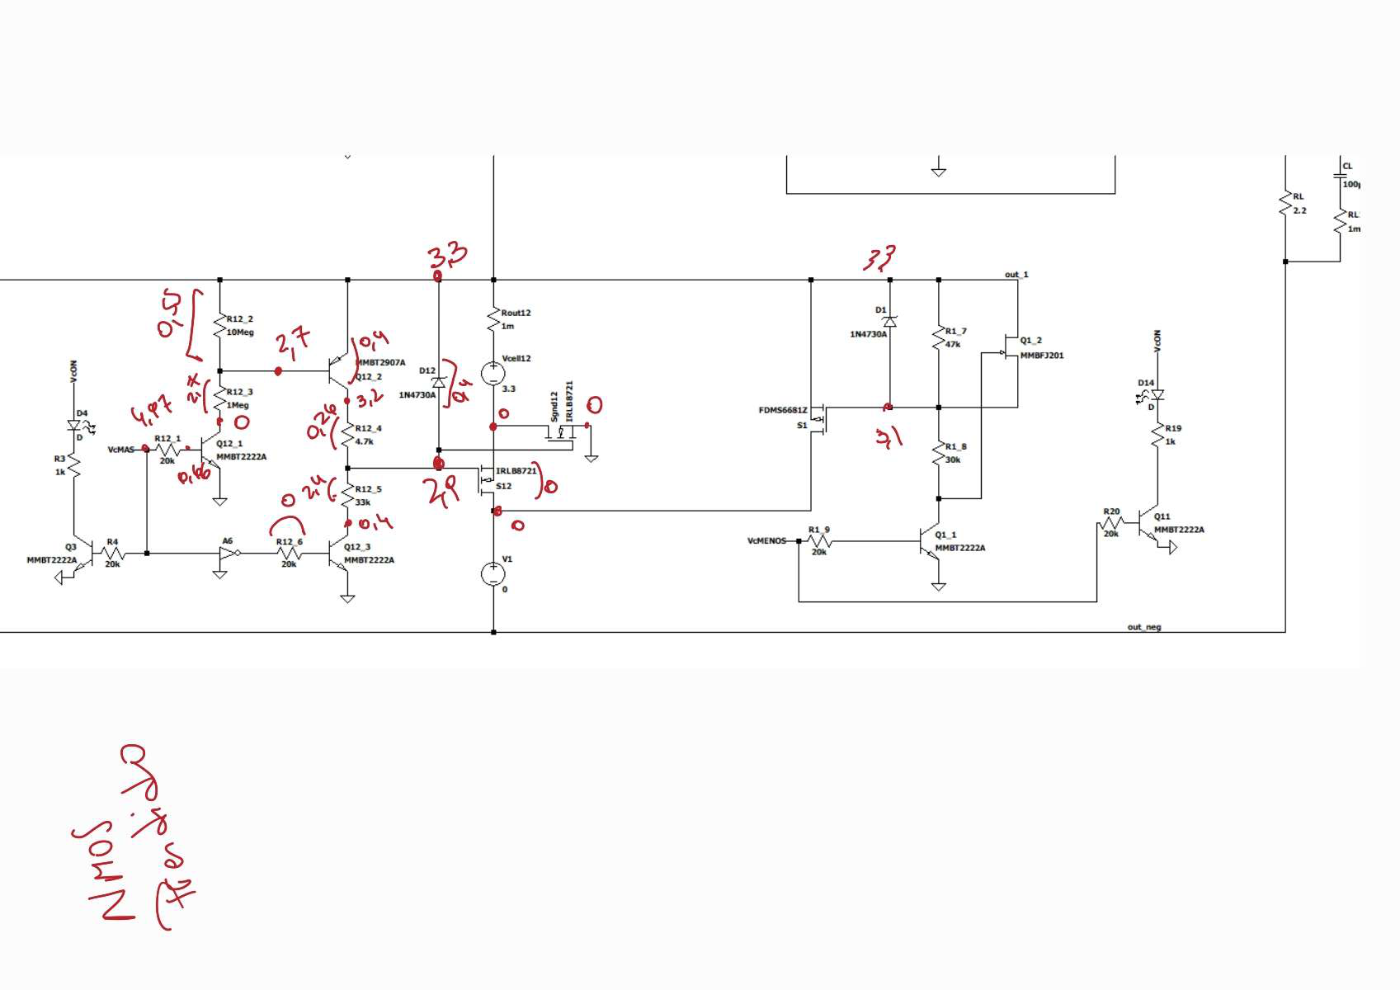
Mediciones/Notes_260204_163819.jpg
