DeniseViltes/Tesis/Mediciones/Prototipo/20-2-2026/fragmento del paper sobre las tierras.png

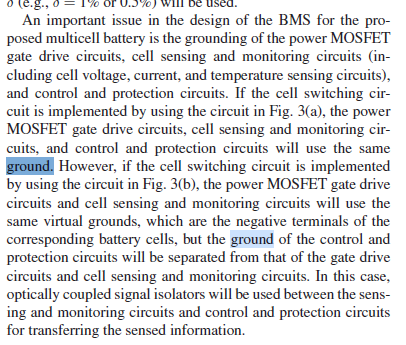
Mediciones/Prototipo/20-2-2026/fragmento del paper sobre las tierras.png
