DeniseViltes/Tesis/Mediciones/Prototipo/27-3-2026/273_260330_140249.jpg

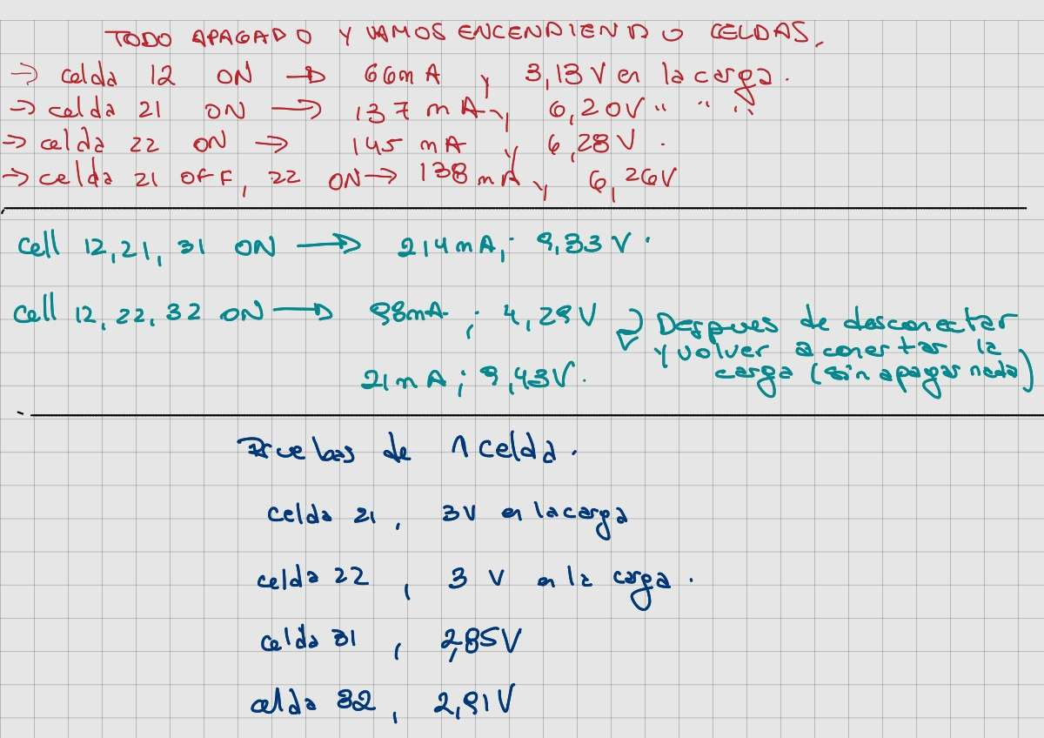
Mediciones/Prototipo/27-3-2026/273_260330_140249.jpg
