DeniseViltes/Tesis/docs/compras/prototipo.xlsx

Reference | Qty | Value | Cantidad | Componentes | Precio por unidad | Precio total | Footprint | Datasheet
 |  |  | 2 | Zocalo DIP 14 | 3.6 | 7.2
A1 | 1 | ~ | 12 | Diodo zener 1N4730A | 0.26 | 0.52 | Package_DIP:DIP-14_W7.62mm_LongPads | http://www.ti.com/lit/gpn/sn74HC14
D1,D2,D3,D4,D5,D6,D_B1,D_B2,D_B3 | 9 | 1N4730 | 8 | Fusible cerámico 3.1A 5x20mm | 0 | 0 | Diode_THT:D_DO-41_SOD81_P7.62mm_Horizontal
 |  |  | 8 | Portafusible para fusible de 5x20mm |  | 0
F1,F2,F3,F4,F5,F6 | 6 | Fuse | 20 | TBJ MMBT2222A |  | 0 | Huellas:Fuseholder_Cylinder-5x20mm_Schurter_0031_8201_Horizontal_Open | ~
Q1,Q2,Q4,Q6,Q8,Q9,Q10,Q12,Q13,Q15,Q16,Q18,QB_1,QB_3,QB_5 | 15 | MMBT2222A | 10 | TBJ MMBT2907A | 0.25 | 5 | Package_TO_SOT_SMD:SOT-23-3
Q3,Q5,Q7,Q11,Q14,Q17 | 6 | MMBT2907A | 4 | PMOS FDMS6681Z | 0.4 | 4 | Package_TO_SOT_SMD:SOT-23-3
Q20,Q21,SB_1 | 3 | FDMS6681Z | 5 | JFET MMBFJ201 | 5 | 20 | FDMS6681Z | https://www.onsemi.com/pub/Collateral/FDMS6681Z-D.PDF
QB_2,QB_4,QB_6 | 3 | MMBFJ201 | 10 | NMOS IRLB8721 | 2.2 | 11 | Package_TO_SOT_SMD:SOT-23-3
S1,S2,S3,S4,S5,S6,SGND1,SGND11 | 8 | IRLB8721 | 6 | Portapila 18650 para pcb (sin cables) | 2.7 | 27 | Package_TO_SOT_THT:TO-220-3_Vertical
VCELL1,VCELL2,VCELL3,VCELL4,VCELL5,VCELL6 | 6 | 3.3 | 5 | Jumper |  | 0 | Huellas:BatteryHolder_MPD_BK-18650-PC2
J_B1,J_B2 | 2 | Conn_01x02_Pin | 20 | Resistencia carbon 1/4W de 20k |  | 0 | Connector_PinHeader_2.54mm:PinHeader_1x02_P2.54mm_Vertical | ~
 |  |  | 2 | Capacitor Tantalio 16V 1uF, 10uF, 100uF
 |  |  | 2 | Capacitor electrolitico 50V 1000uF
 |  |  | 4 | soportes
 |  |  | 9 | LEDs
 |  |  | 1 | bornera |  | 0
 |  |  | 1m | alambre
 |  |  | 2 | 74AHC14 (DIP 14)
 |  |  | 10 | Resistencia carbon 1/4W de 570k,300k, 0 ohm
 |  |  | 10 | Mmbt2222A
 |  |  | 1 | tira doble de pines hembra
 |  |  | 1 | Portafusible para fusible de 5x20mm
 |  |  |  | estaño
 |  |  |  | cables
 |  |  | 2 | Amplificador de instrumentación
 |  |  | 18 | tornillos m3 + tuercas
 |  |  |  | 74AHC14 (DIP 14)
 |  |  | 2 | Fusible cerámico 3.1A 5x20mm
 |  |  | 8 | Portafusible para fusible de 5x20mm
 |  |  | 8 | Portapila 18650 para pcb (sin cables)
 |  |  | 6 | Resistencia carbon 1/4W de 570k,300k, 0 ohm
 |  |  | 10 | Amplificador de instrumentación
 |  |  | 1
