DeniseViltes/Tesis/hardware/PCB/Modelos 3D/Celda 18650.stp

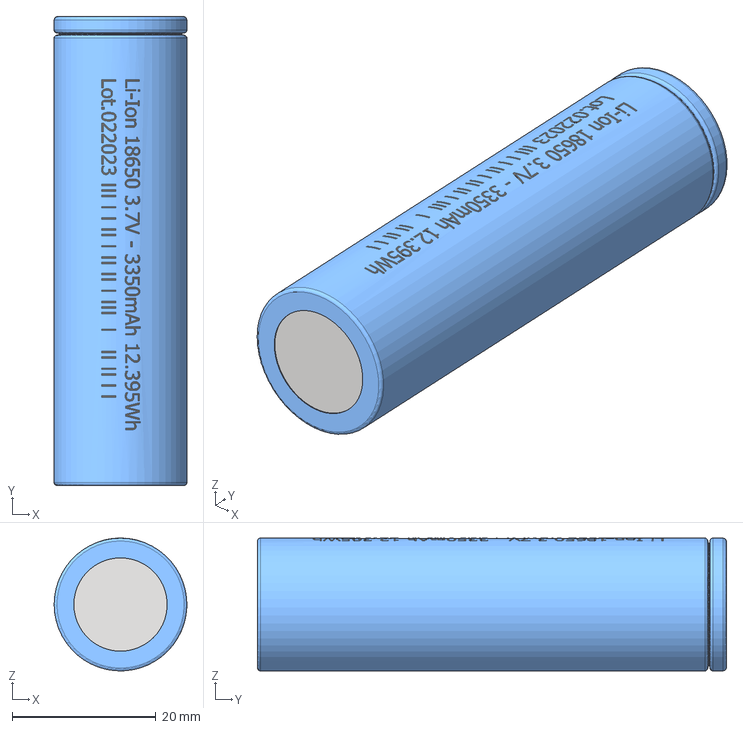
[picture p250: CAD file, 2026-09-13]
hardware/PCB/Modelos 3D/Celda 18650.stp
18.5 x 65.3 x 18.5 mm
