DeniseViltes/Tesis/hardware/PCB/Modelos 3D/Pin hembra largo 1x6.STEP

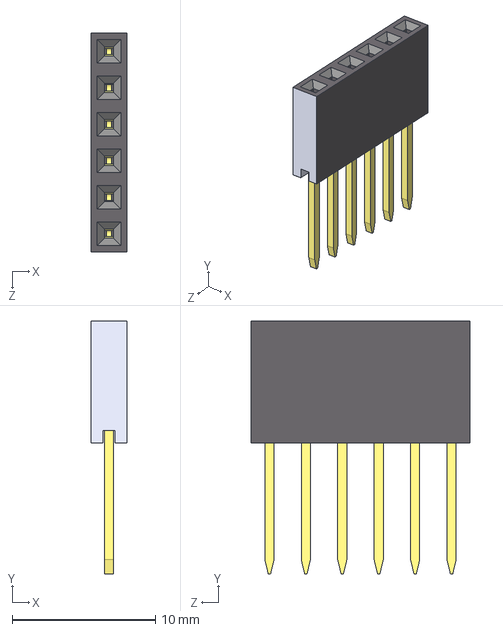
[picture p258: CAD file, 2026-07-14]
hardware/PCB/Modelos 3D/Pin hembra largo 1x6.STEP
2.54 x 17.6 x 15.2 mm
