DeniseViltes/Tesis/hardware/PCB/Modelos 3D/Pin hembra largo 1x7.STEP

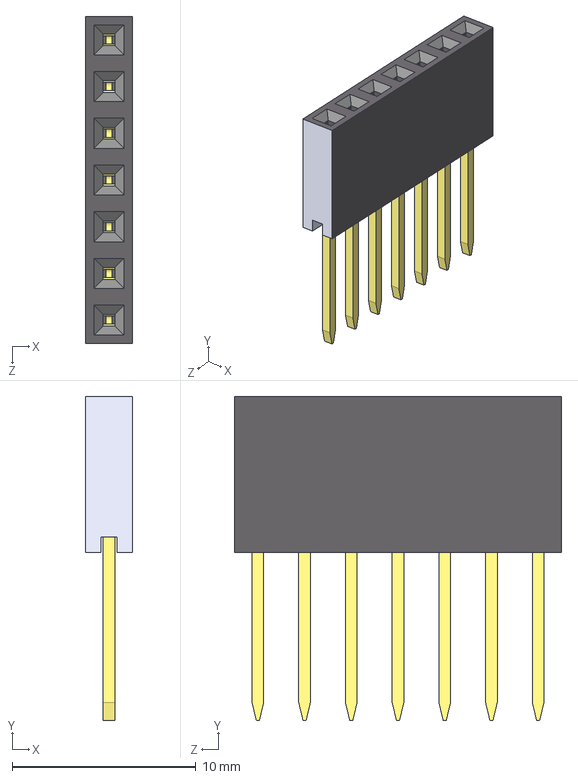
[picture p259: CAD file, 2026-07-14]
hardware/PCB/Modelos 3D/Pin hembra largo 1x7.STEP
2.54 x 17.6 x 17.8 mm
