DeniseViltes/Tesis/hardware/PCB/Modelos 3D/Pin hembra largo 1x4.STEP

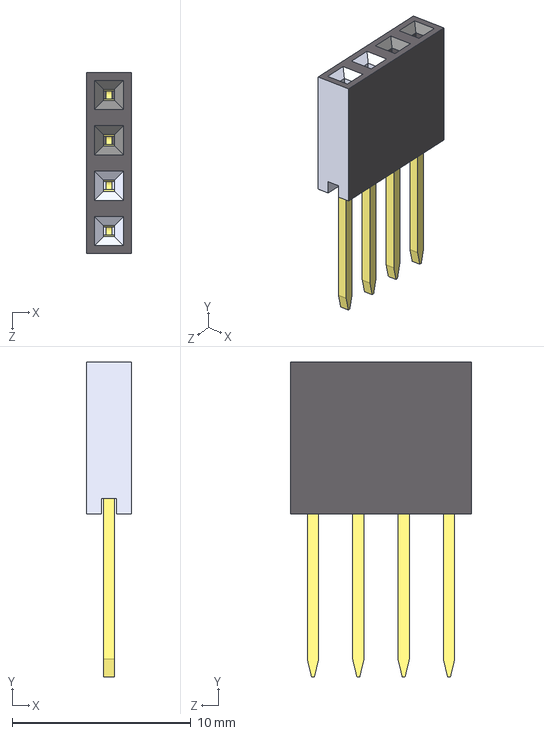
[picture p260: CAD file, 2026-07-14]
hardware/PCB/Modelos 3D/Pin hembra largo 1x4.STEP
2.54 x 17.6 x 10.2 mm
