DeniseViltes/Tesis/hardware/PCB/Modelos 3D/Portafusible.stp

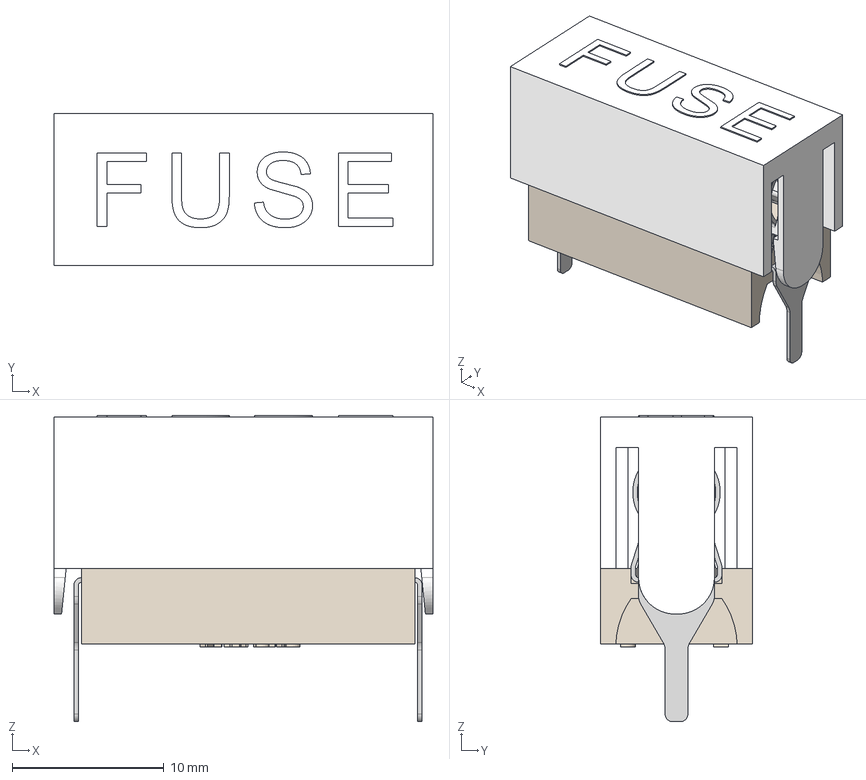
[picture p261: CAD file, 2025-11-19]
hardware/PCB/Modelos 3D/Portafusible.stp
25.0 x 10.0 x 20.2 mm
fuse_base
fuse_crimp x 2
fuse_top
