DeniseViltes/Tesis/hardware/PCB/Modelos 3D/FDMS6681Z.step

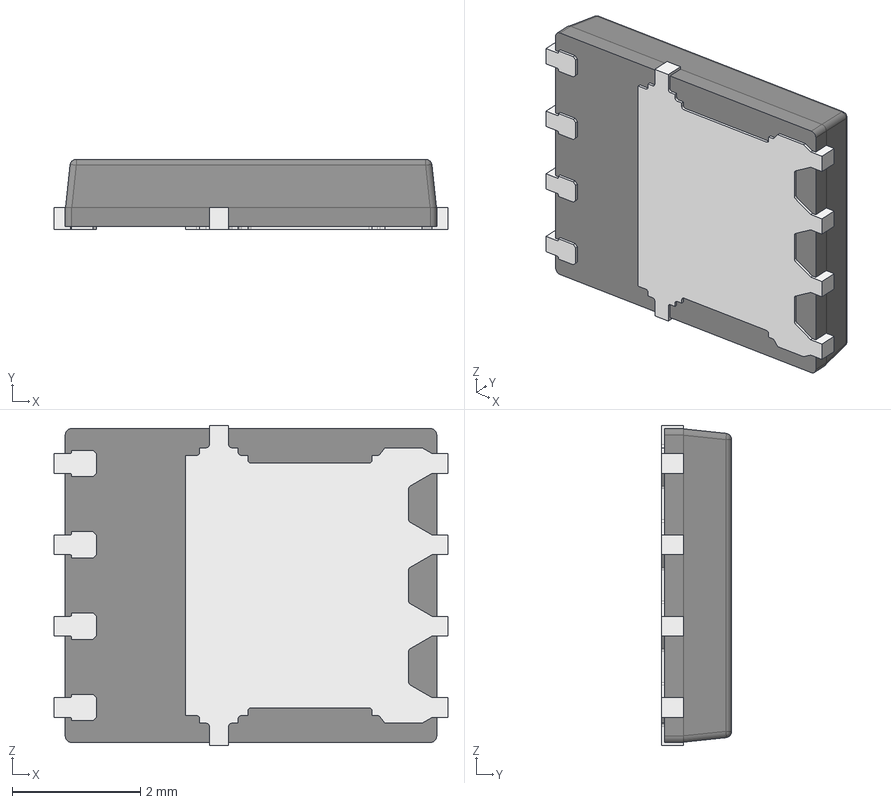
[picture p262: CAD file, 2025-11-19]
hardware/PCB/Modelos 3D/FDMS6681Z.step
6.15 x 1.10 x 5.00 mm
