DeniseViltes/Tesis/hardware/PCB/Modelos 3D/Portapilas 18650.STEP

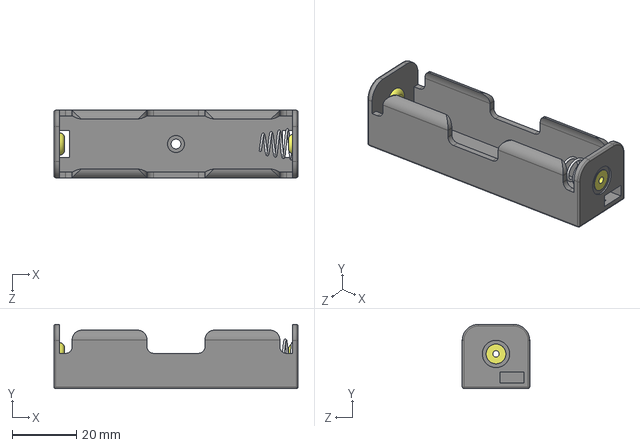
[picture p263: CAD file, 2025-11-19]
hardware/PCB/Modelos 3D/Portapilas 18650.STEP
75.9 x 20.0 x 21.0 mm
