DeniseViltes/Tesis/media/Instrucciones de uso/Manual - Celda en banco.png

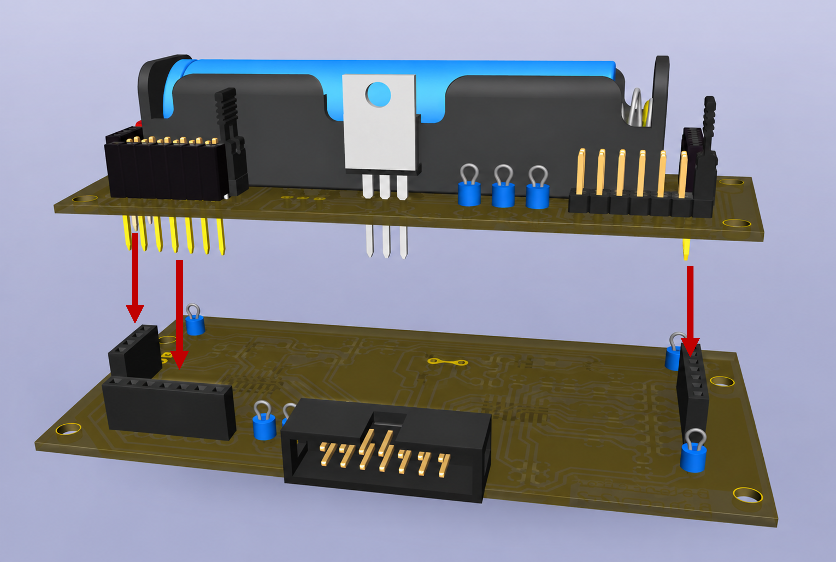
media/Instrucciones de uso/Manual - Celda en banco.png
