DeniseViltes/Tesis/Mediciones/Circuito final/Urocon/Banco de prueba  1/bus_pos-bus_neg_sw.xls

Save Time: | 2026-07-14 12:59:30
 |  | CH1 | CH2
Frequency: |  | ? | 0.693 Hz
Period: |  | ? | 1.444 S
SP: |  | 1000.000 uS | 1000.000 uS
PK-PK: |  | 6.400 V | 3.920 V
Units:(mV)
1 | 1000.000us | 5840 | 2720 | 3120
2 | 2000.000us | 5920 | 2800 | 3120
3 | 3000.000us | 5760 | 2720 | 3040
4 | 4000.000us | 5840 | 2800 | 3040
5 | 5000.000us | 5840 | 2800 | 3040
6 | 6000.000us | 5920 | 2800 | 3120
7 | 7000.000us | 5840 | 2720 | 3120
8 | 8000.000us | 5840 | 2800 | 3040
9 | 9000.000us | 5840 | 2800 | 3040
10 | 10000.000us | 5920 | 2800 | 3120
11 | 11000.000us | 5760 | 2720 | 3040
12 | 12000.000us | 5920 | 2720 | 3200
13 | 13000.000us | 5840 | 2720 | 3120
14 | 14000.000us | 5920 | 2800 | 3120
15 | 15000.000us | 5840 | 2720 | 3120
16 | 16000.000us | 5840 | 2800 | 3040
17 | 17000.000us | 5840 | 2800 | 3040
18 | 18000.000us | 5920 | 2800 | 3120
19 | 19000.000us | 5760 | 2720 | 3040
20 | 20000.000us | 5920 | 2800 | 3120
21 | 21000.000us | 5840 | 2800 | 3040
22 | 22000.000us | 5920 | 2800 | 3120
23 | 23000.000us | 5840 | 2720 | 3120
24 | 24000.000us | 5920 | 2800 | 3120
25 | 25000.000us | 5920 | 2720 | 3200
26 | 26000.000us | 5920 | 2800 | 3120
27 | 27000.000us | 5840 | 2720 | 3120
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
