DeniseViltes/Tesis/Mediciones/Circuito final/Urocon/Banco de prueba  1/data y bus_neg.xls

Save Time: | 2026-07-14 13:10:52
 |  | CH1 | CH2
Frequency: |  | 1.383 Hz | 0.873 Hz
Period: |  | 723.000 mS | 1.146 S
SP: |  | 1000.000 uS | 1000.000 uS
PK-PK: |  | 3.520 V | 4.000 V
Units:(mV)
1 | 1000.000us | 80 | 3280
2 | 2000.000us | 160 | 3360
3 | 3000.000us | 0 | 3280
4 | 4000.000us | 80 | 3360
5 | 5000.000us | 80 | 3280
6 | 6000.000us | 80 | 3360
7 | 7000.000us | 80 | 3280
8 | 8000.000us | 80 | 3360
9 | 9000.000us | 160 | 3280
10 | 10000.000us | 3520 | 3360
11 | 11000.000us | 0 | 3280
12 | 12000.000us | 3520 | 3280
13 | 13000.000us | 3520 | 3360
14 | 14000.000us | 3520 | 3360
15 | 15000.000us | 3440 | 3280
16 | 16000.000us | 3440 | 3280
17 | 17000.000us | 3440 | 3280
18 | 18000.000us | 3520 | 3440
19 | 19000.000us | 3440 | 2720
20 | 20000.000us | 3440 | 2720
21 | 21000.000us | 3520 | 2800
22 | 22000.000us | 3520 | 2800
23 | 23000.000us | 3440 | 2800
24 | 24000.000us | 3440 | 2800
25 | 25000.000us | 3440 | 2800
26 | 26000.000us | 3520 | 2800
27 | 27000.000us | 3440 | 2720
28 | 28000.000us | 3520 | 2800
29 | 29000.000us | 3440 | 2800
30 | 30000.000us | 3520 | 2800
31 | 31000.000us | 3440 | 2720
32 | 32000.000us | 3440 | 2800
33 | 33000.000us | 3520 | 2800
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
