DeniseViltes/Tesis/Mediciones/Circuito final/Urocon/Banco de prueba  1/data y clock.xls

Save Time: | 2026-07-14 14:40:35
 |  | CH1 | CH2
Frequency: |  | 2.843 Hz | 22.760 Hz
Period: |  | 351.750 mS | 43.938 mS
SP: |  | 1000.000 uS | 1000.000 uS
PK-PK: |  | 3.600 V | 3.600 V
Units:(mV)
1 | 1000.000us | 3440 | 3360
2 | 2000.000us | 3520 | 3440
3 | 3000.000us | 80 | 0
4 | 4000.000us | 80 | 0
5 | 5000.000us | 80 | 0
6 | 6000.000us | 80 | 3440
7 | 7000.000us | 0 | 0
8 | 8000.000us | 80 | 0
9 | 9000.000us | 80 | 80
10 | 10000.000us | 80 | 80
11 | 11000.000us | 0 | 0
12 | 12000.000us | 80 | 0
13 | 13000.000us | 80 | 0
14 | 14000.000us | 80 | 160
15 | 15000.000us | 0 | -80
16 | 16000.000us | 80 | 0
17 | 17000.000us | 80 | 80
18 | 18000.000us | 80 | 80
19 | 19000.000us | 0 | 0
20 | 20000.000us | 80 | 0
21 | 21000.000us | 0 | 80
22 | 22000.000us | 80 | 80
23 | 23000.000us | 0 | 0
24 | 24000.000us | 80 | 0
25 | 25000.000us | 80 | 80
26 | 26000.000us | 80 | 80
27 | 27000.000us | 0 | 0
28 | 28000.000us | 0 | 0
29 | 29000.000us | 80 | 0
30 | 30000.000us | 80 | 80
31 | 31000.000us | 0 | 0
32 | 32000.000us | 80 | 0
33 | 33000.000us | 80 | 80
34 | 34000.000us | 80 | 80
35 | 35000.000us | 80 | 0
36 | 36000.000us | 80 | 0
37 | 37000.000us | 80 | 0
38 | 38000.000us | 80 | 80
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
