DeniseViltes/Tesis/Mediciones/Circuito final/Urocon/Banco de prueba 2/data y bus neg.xls

Save Time: | 2026-07-14 16:44:58
 |  | CH1 | CH2
Frequency: |  | 3.368 Hz | ?
Period: |  | 296.889 mS | ?
SP: |  | 1000.000 uS | 1000.000 uS
PK-PK: |  | 3.520 V | 240.000 mV
Units:(mV)
1 | 1000.000us | 80 | 80
2 | 2000.000us | 80 | 80
3 | 3000.000us | 80 | 0
4 | 4000.000us | 80 | 80
5 | 5000.000us | 80 | 80
6 | 6000.000us | 160 | 80
7 | 7000.000us | 0 | 0
8 | 8000.000us | 80 | 80
9 | 9000.000us | 80 | 160
10 | 10000.000us | 160 | 160
11 | 11000.000us | 80 | 0
12 | 12000.000us | 160 | 80
13 | 13000.000us | 80 | 80
14 | 14000.000us | 160 | 160
15 | 15000.000us | 80 | 80
16 | 16000.000us | 160 | 80
17 | 17000.000us | 80 | 80
18 | 18000.000us | 80 | 80
19 | 19000.000us | 80 | 0
20 | 20000.000us | 80 | 80
21 | 21000.000us | 80 | 80
22 | 22000.000us | 160 | 80
23 | 23000.000us | 0 | 0
24 | 24000.000us | 80 | 80
25 | 25000.000us | 80 | 80
26 | 26000.000us | 160 | 160
27 | 27000.000us | 80 | 0
28 | 28000.000us | 80 | 80
29 | 29000.000us | 80 | 80
30 | 30000.000us | 160 | 80
31 | 31000.000us | 0 | 0
32 | 32000.000us | 80 | 80
33 | 33000.000us | 80 | 80
34 | 34000.000us | 160 | 80
35 | 35000.000us | 80 | 0
36 | 36000.000us | 80 | 80
37 | 37000.000us | 80 | 80
38 | 38000.000us | 80 | 80
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
