DeniseViltes/Tesis/Mediciones/Circuito final/Urocon/Banco de prueba 2/data y pmos gate.xls

Save Time: | 2026-07-14 16:46:45
 |  | CH1 | CH2
Frequency: |  | 3.378 Hz | ?
Period: |  | 296.000 mS | ?
SP: |  | 1000.000 uS | 1000.000 uS
PK-PK: |  | 3.600 V | 6.400 V
Units:(mV)
1 | 1000.000us | 3440 | 6240
2 | 2000.000us | 3520 | 6320
3 | 3000.000us | 3440 | 6240
4 | 4000.000us | 3520 | 6240
5 | 5000.000us | 3440 | 6320
6 | 6000.000us | 3440 | 6400
7 | 7000.000us | 80 | 6240
8 | 8000.000us | 80 | 6240
9 | 9000.000us | 80 | 6320
10 | 10000.000us | 80 | 6320
11 | 11000.000us | 80 | 6240
12 | 12000.000us | 80 | 6320
13 | 13000.000us | 80 | 6240
14 | 14000.000us | 160 | 6320
15 | 15000.000us | 80 | 6240
16 | 16000.000us | 80 | 6320
17 | 17000.000us | 80 | 6320
18 | 18000.000us | 160 | 6400
19 | 19000.000us | 0 | 6240
20 | 20000.000us | 80 | 6240
21 | 21000.000us | 80 | 6320
22 | 22000.000us | 80 | 6320
23 | 23000.000us | 0 | 6240
24 | 24000.000us | 80 | 6320
25 | 25000.000us | 80 | 6320
26 | 26000.000us | 80 | 6320
27 | 27000.000us | 0 | 6240
28 | 28000.000us | 80 | 6320
29 | 29000.000us | 80 | 6240
30 | 30000.000us | 160 | 6320
31 | 31000.000us | 80 | 6240
32 | 32000.000us | 80 | 6320
33 | 33000.000us | 80 | 6240
34 | 34000.000us | 80 | 6320
35 | 35000.000us | 80 | 6240
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
