DeniseViltes/Tesis/Ltspice/proyectos/matriz_2x2/runs/prueba_de_resistencias_en_tierra/Imagenes/1MAS_2MAS-RL_1k-tension_salida.txt.png

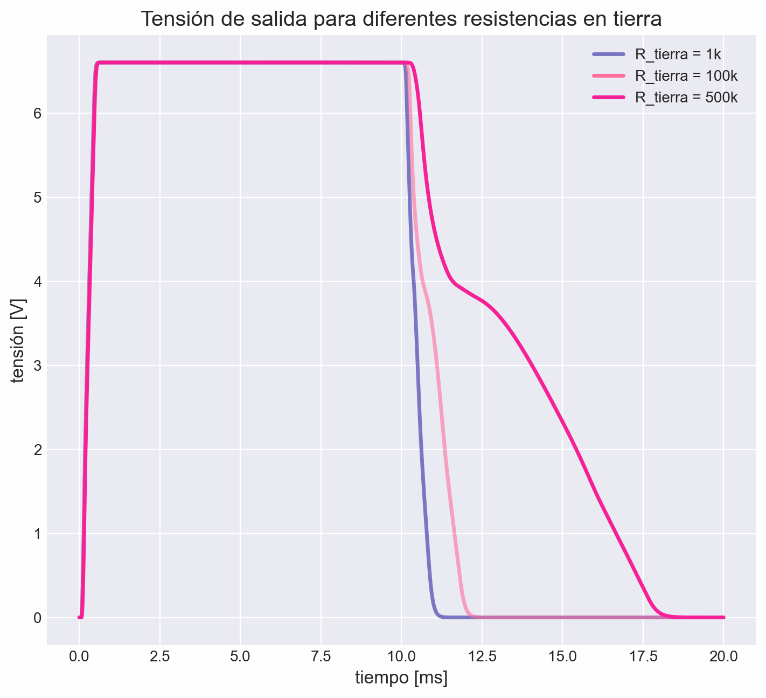
Ltspice/proyectos/matriz_2x2/runs/prueba_de_resistencias_en_tierra/Imagenes/1MAS_2MAS-RL_1k-tension_salida.txt.png
