DeniseViltes/Tesis/Ltspice/proyectos/nuevo_pmos/Prueba plaquita PMOS - Spice VGS PMOS con JFET y resistores de 470k y 220k.png

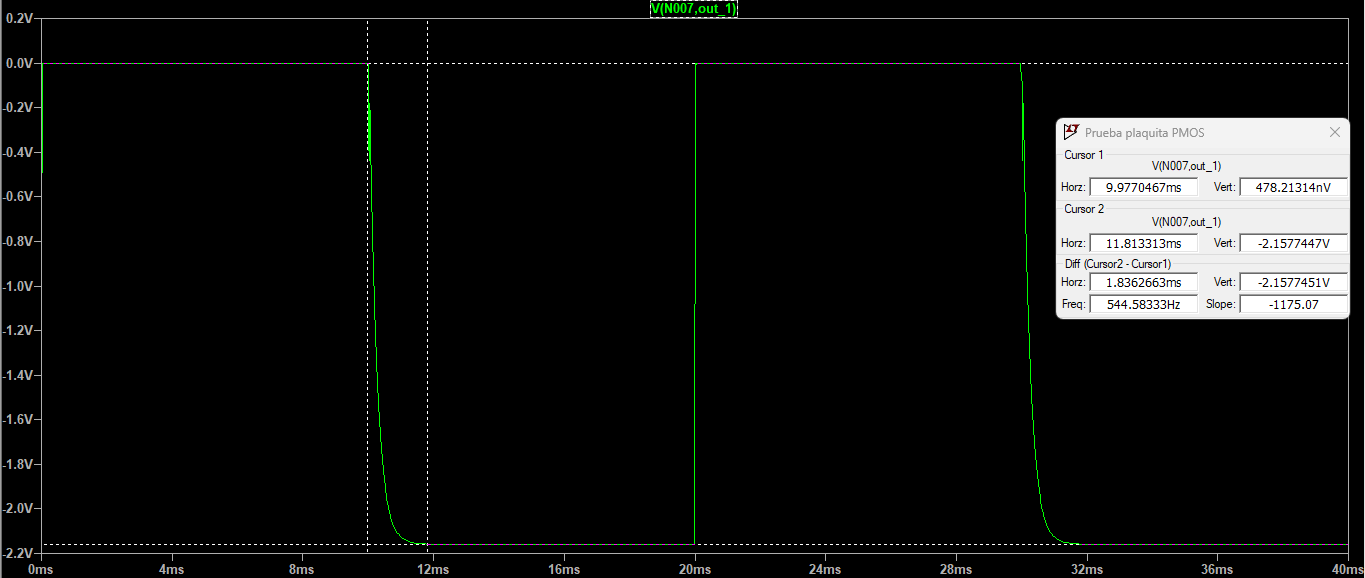
Ltspice/proyectos/nuevo_pmos/Prueba plaquita PMOS - Spice VGS PMOS con JFET y resistores de 470k y 220k.png
