DeniseViltes/Tesis/Ltspice/proyectos/nuevo_pmos/Prueba plaquita PMOS - Spice VGS PMOS sin JFET y resistores de 470k y 330k.png

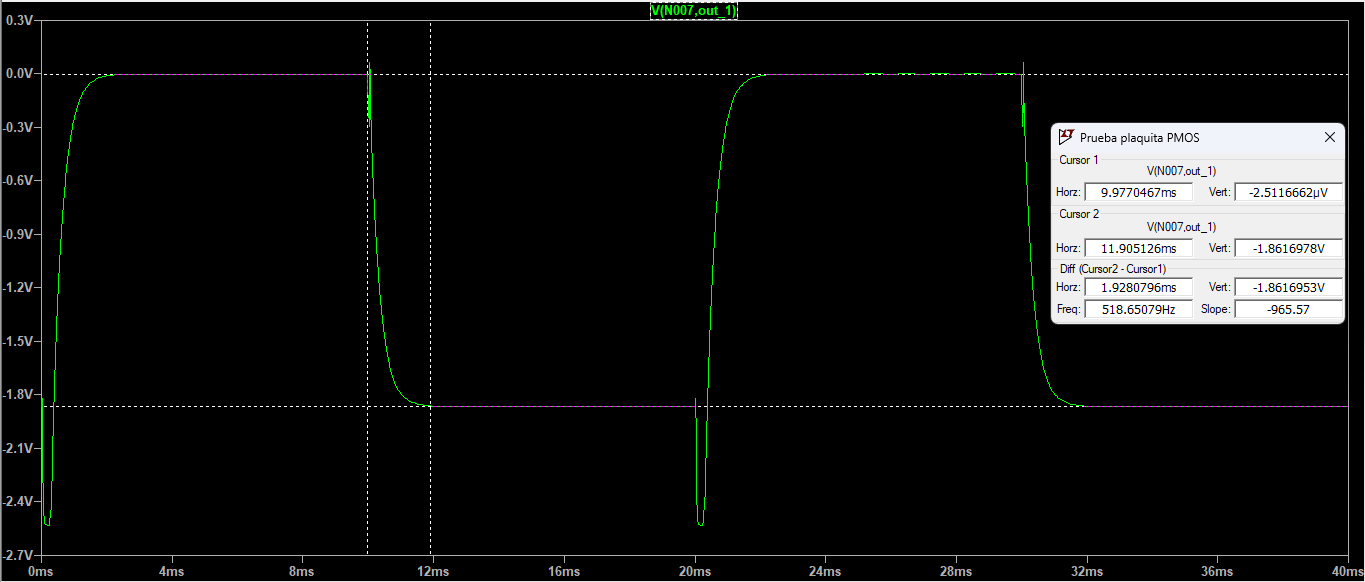
Ltspice/proyectos/nuevo_pmos/Prueba plaquita PMOS - Spice VGS PMOS sin JFET y resistores de 470k y 330k.png
