DeniseViltes/Tesis/media/Latex/Diseño del circuito/resultado de primera simulacion funcional.png

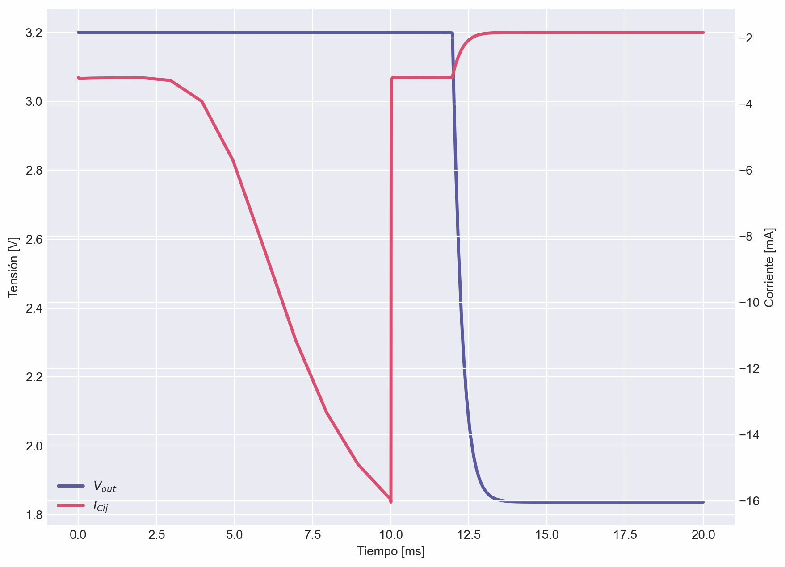
media/Latex/Diseño del circuito/resultado de primera simulacion funcional.png
