DeniseViltes/Tesis/Mediciones/Circuito final/Banco prueba/29-4_AO3401.png

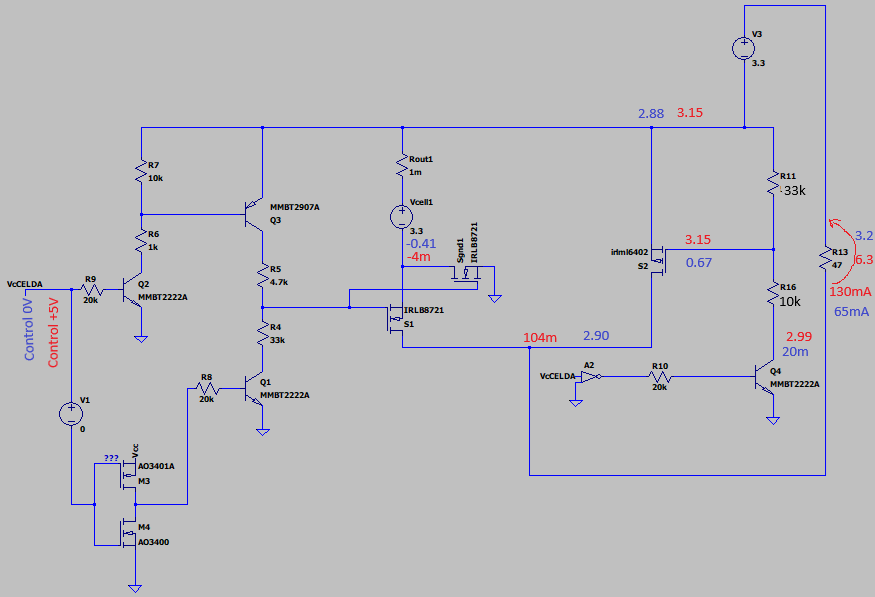
Mediciones/Circuito final/Banco prueba/29-4_AO3401.png
