DeniseViltes/Tesis/Mediciones/Circuito final/Banco prueba/IRLM6204 con tension de prueba de 13,2V.png

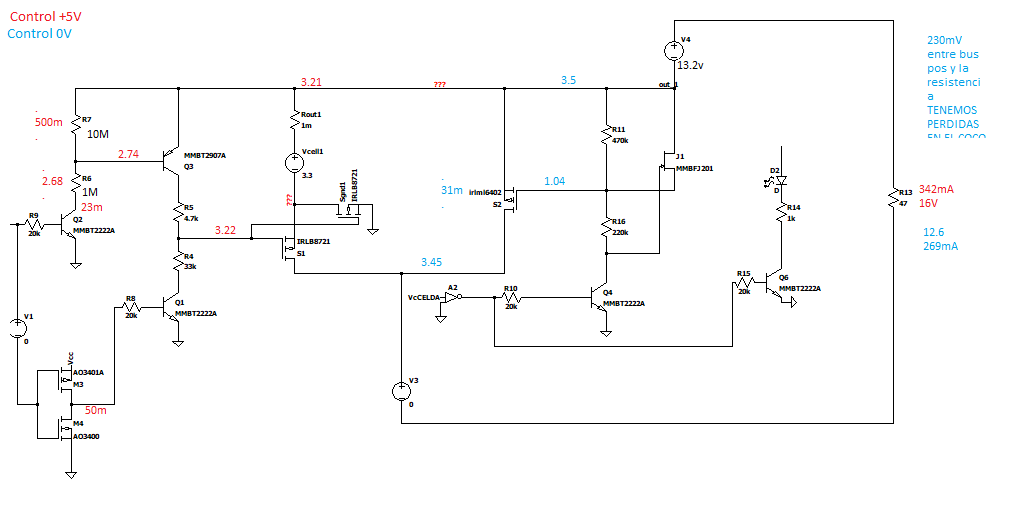
Mediciones/Circuito final/Banco prueba/IRLM6204 con tension de prueba de 13,2V.png
