DeniseViltes/Tesis/Mediciones/Circuito final/Banco prueba/IRLM6204 y fet.png

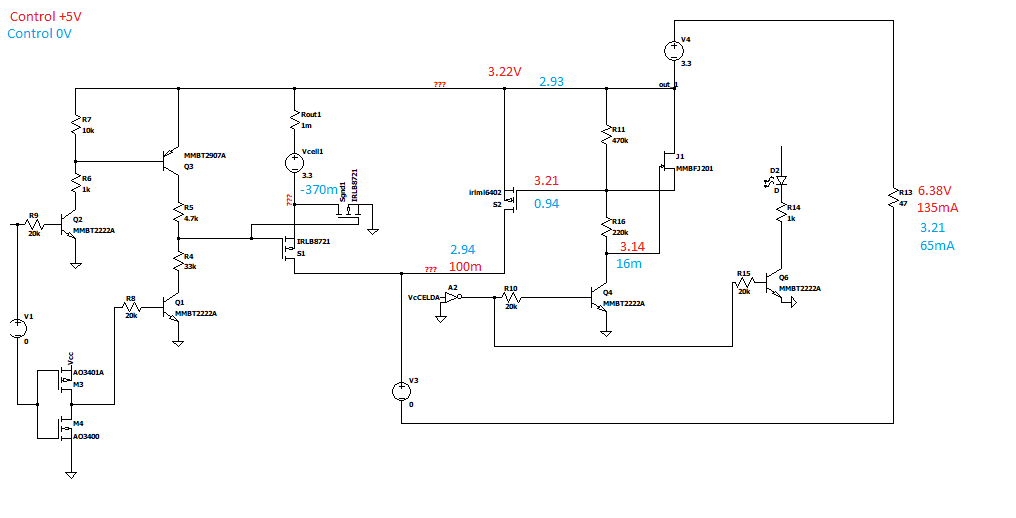
Mediciones/Circuito final/Banco prueba/IRLM6204 y fet.png
