DeniseViltes/Tesis/Mediciones/Circuito final/Celda 2.0/mediciones prueba celda2.0.png

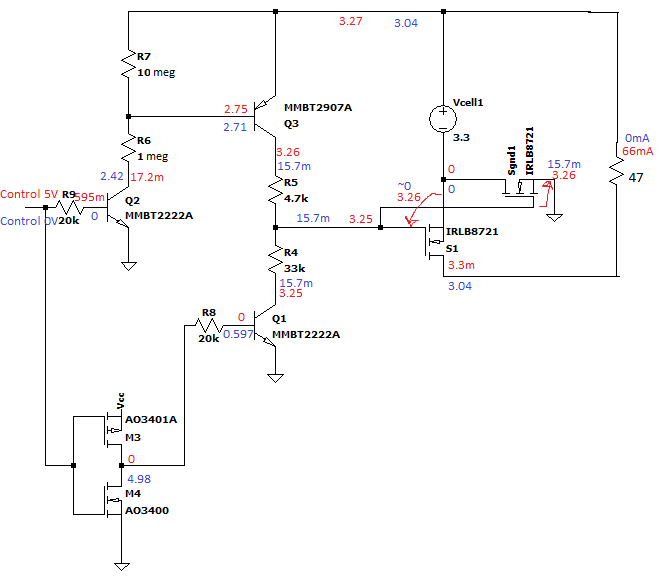
Mediciones/Circuito final/Celda 2.0/mediciones prueba celda2.0.png
