DeniseViltes/Tesis/Mediciones/Circuito final/Celda 2.1/Mediciones prueba celda 2.1.png

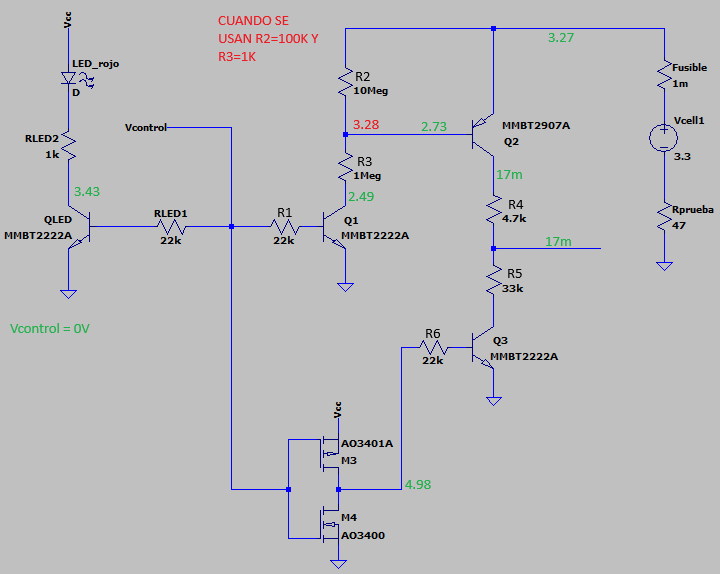
Mediciones/Circuito final/Celda 2.1/Mediciones prueba celda 2.1.png
