DeniseViltes/Tesis/Mediciones/Circuito final/Prueba jfet/Con fet.png

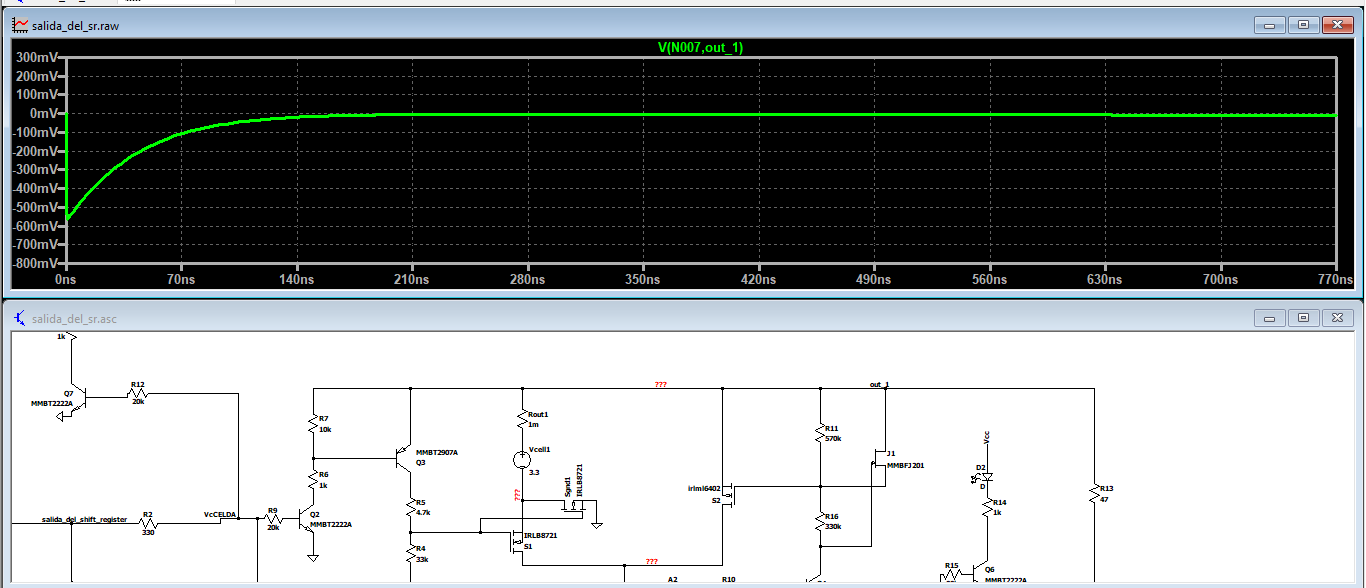
Mediciones/Circuito final/Prueba jfet/Con fet.png
