DeniseViltes/Tesis/Mediciones/Circuito final/Prueba jfet/salida con fet.png

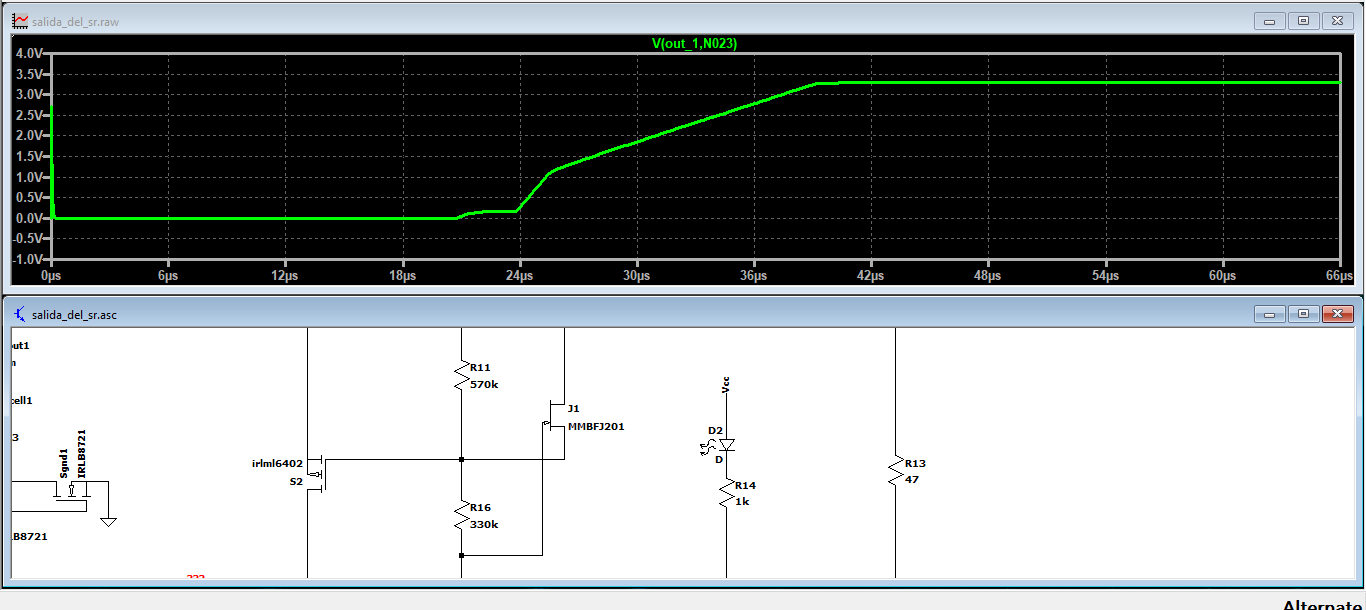
Mediciones/Circuito final/Prueba jfet/salida con fet.png
