DeniseViltes/Tesis/Mediciones/Circuito final/Prueba jfet/Salida sin fet.png

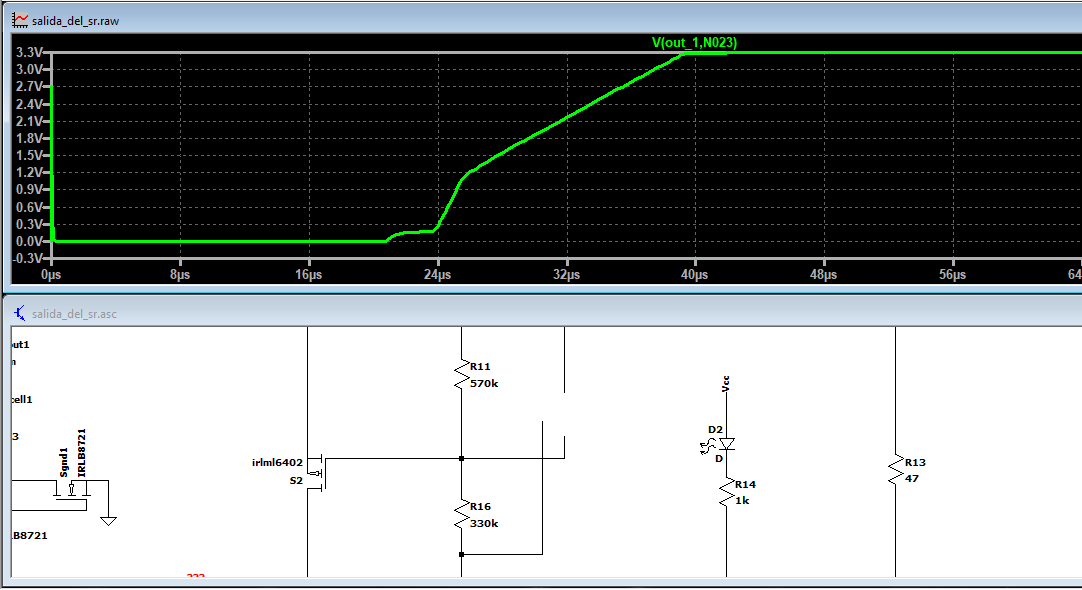
Mediciones/Circuito final/Prueba jfet/Salida sin fet.png
