DeniseViltes/Tesis/Mediciones/Circuito final/Prueba jfet/Sin fet.png

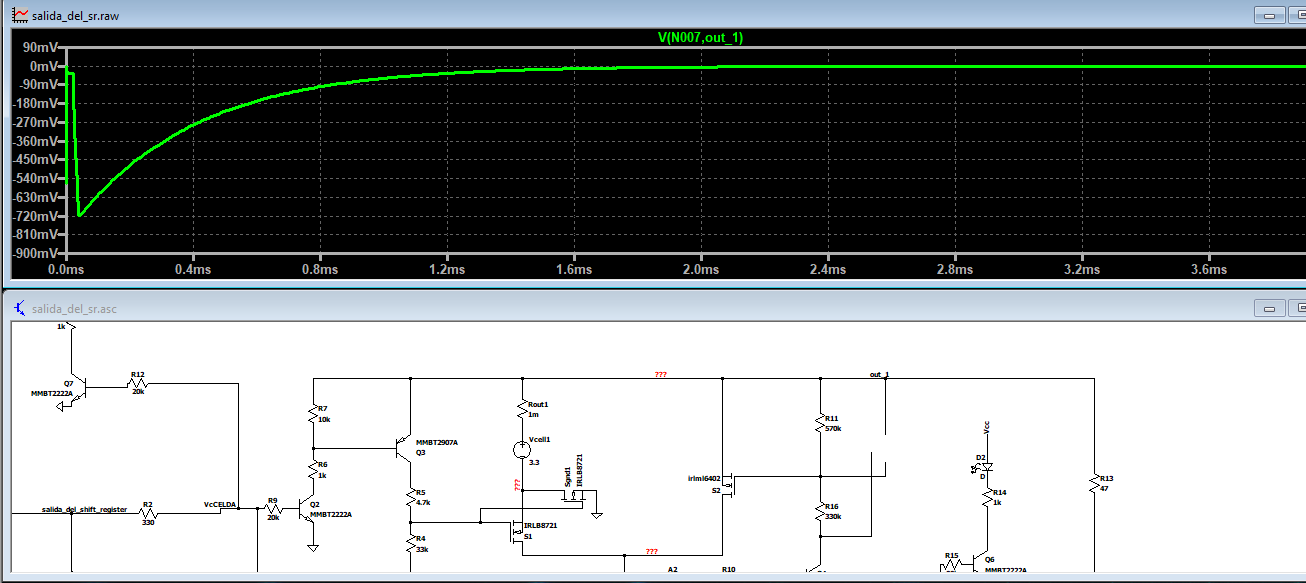
Mediciones/Circuito final/Prueba jfet/Sin fet.png
