DeniseViltes/Tesis/Mediciones/Circuito final/Urocon/Banco de prueba  1/salida con data y clock en sw en detalle.png

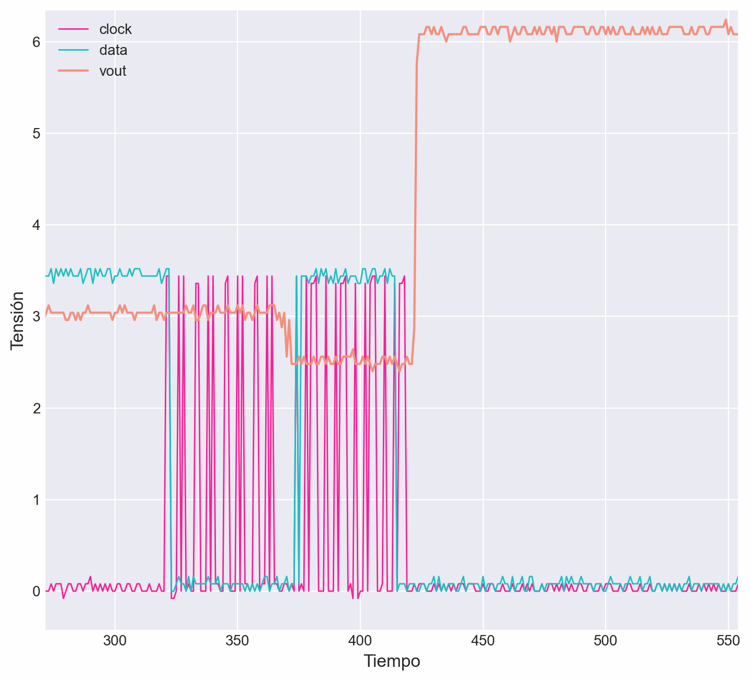
Mediciones/Circuito final/Urocon/Banco de prueba 1/salida con data y clock en sw en detalle.png
