DeniseViltes/Tesis/Mediciones/Circuito final/Urocon/Banco de prueba  1/salida y data con sw.png

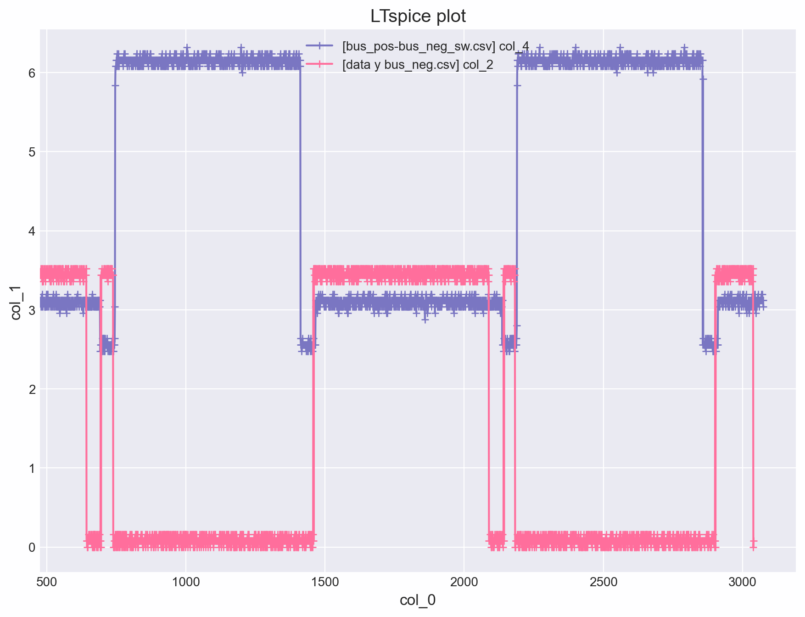
Mediciones/Circuito final/Urocon/Banco de prueba 1/salida y data con sw.png
