DeniseViltes/Tesis/Mediciones/Circuito final/Urocon/Banco de prueba  1/vgs pmos y nmos.png

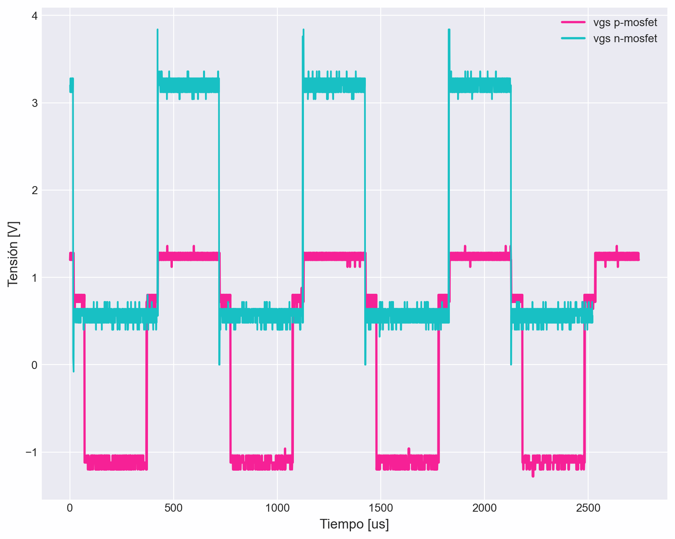
Mediciones/Circuito final/Urocon/Banco de prueba 1/vgs pmos y nmos.png
