DeniseViltes/Tesis/hardware/Archivos de fabricación/PDF/prototipo-B_Cu.pdf

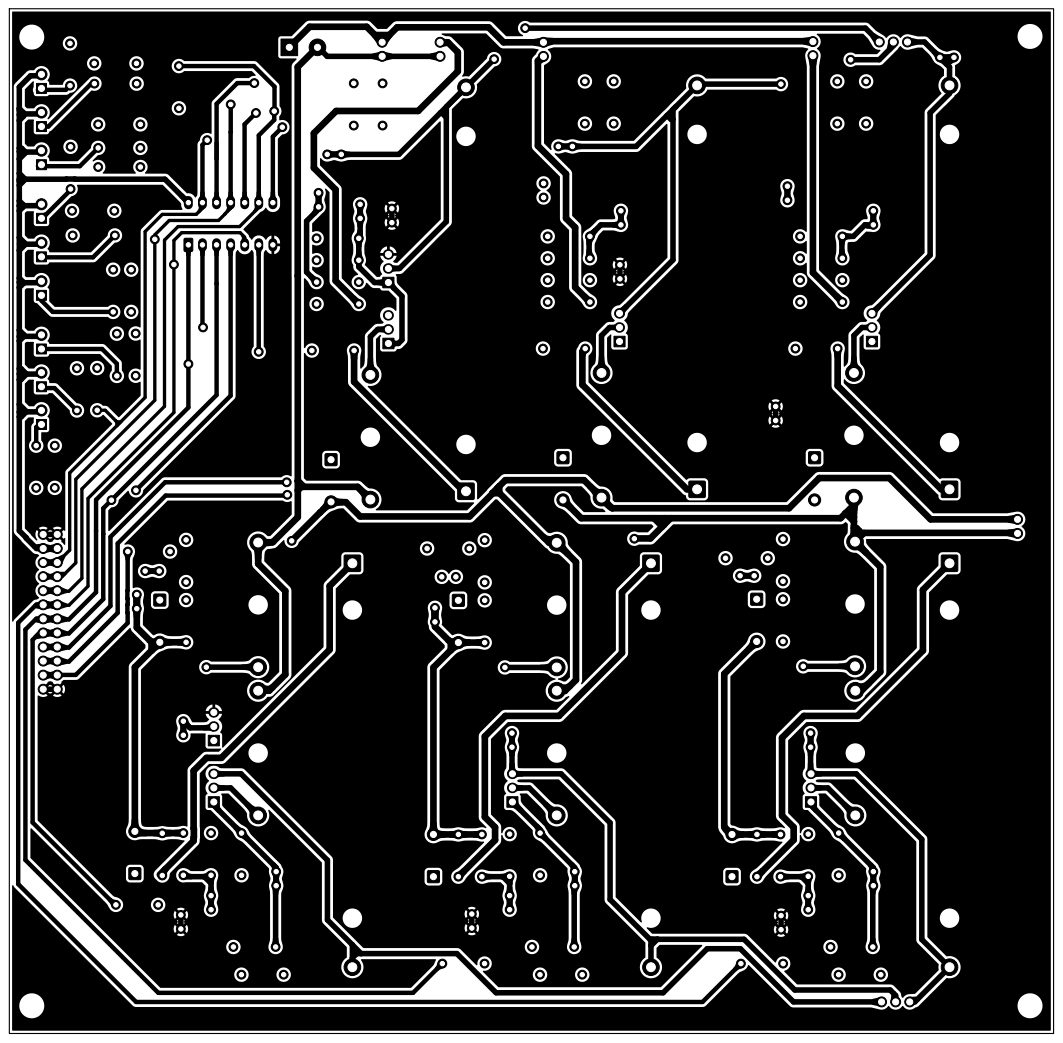
[picture p300: page 1]
