DeniseViltes/Tesis/hardware/Archivos de fabricación/PDF/prototipo-Edge_Cuts.pdf

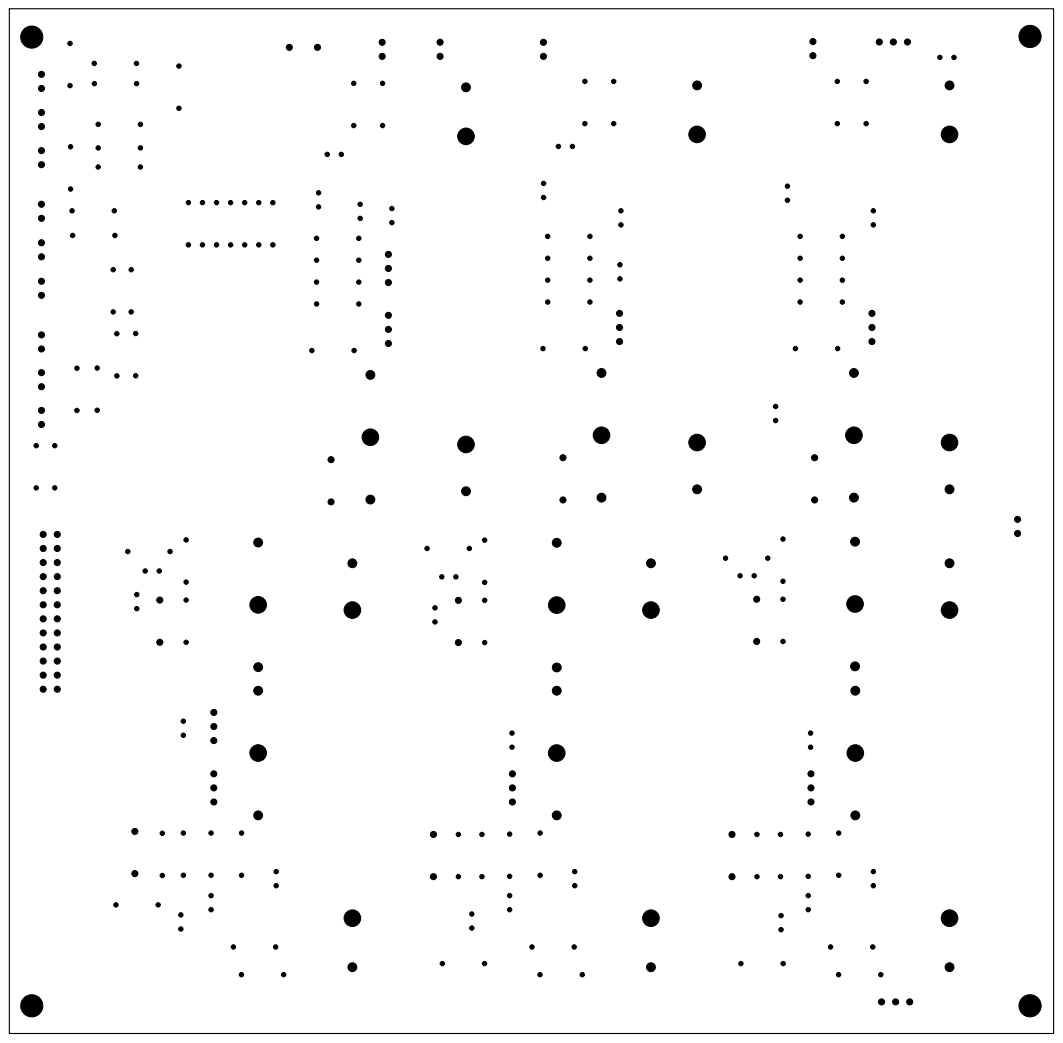
[picture p301: page 1]
