DeniseViltes/Tesis/hardware/Archivos de fabricación/PDF/prototipo-F_Cu.pdf

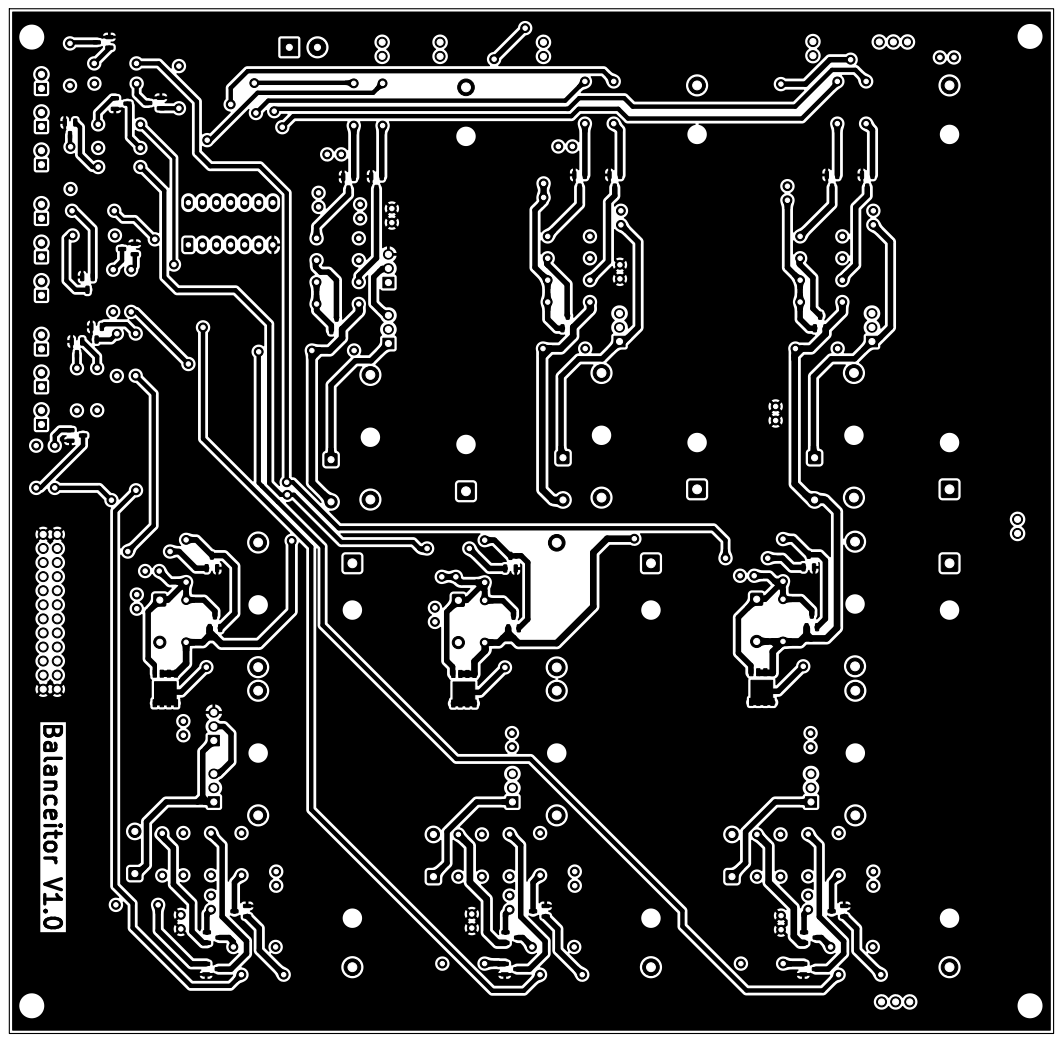
[picture p302: page 1]
