DeniseViltes/Tesis/hardware/Circuito Final/Ideas/Adaptador Mux analógico/adaptador mux-B_Cu.pdf

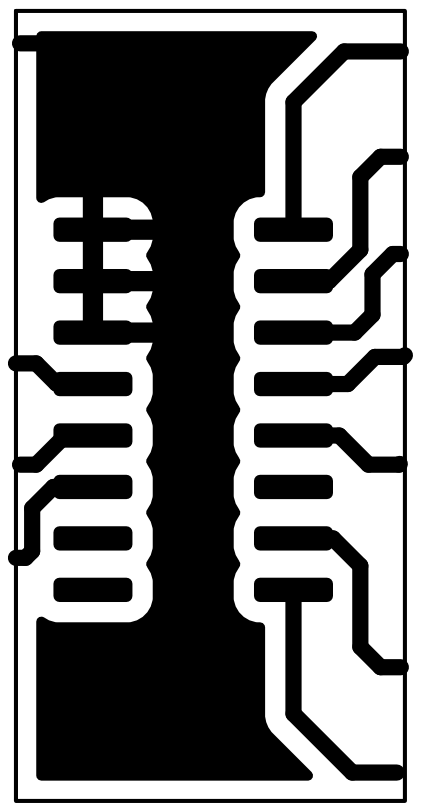
[picture p303: page 1]
