DeniseViltes/Tesis/hardware/Circuito Final/Ideas/Adaptador SR/adaptador sr-B_Cu.pdf

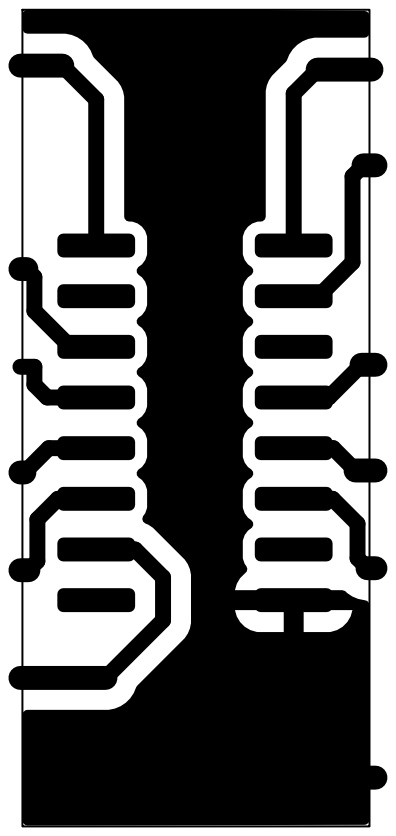
[picture p304: page 1]
