DeniseViltes/Tesis/hardware/Circuito Final/Ideas/Switch banco prueba/Prueba 2 del switch del banco.pdf

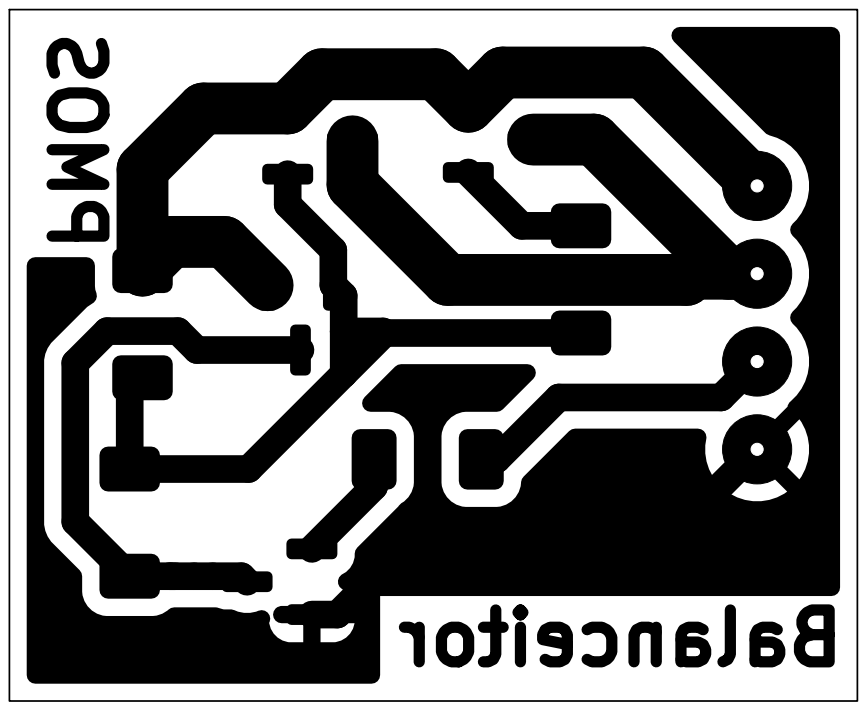
[picture p305: page 1]
