DeniseViltes/Tesis/hardware/Circuito Final/Ideas/Switch banco prueba/Prueba 1 del switch del banco.pdf

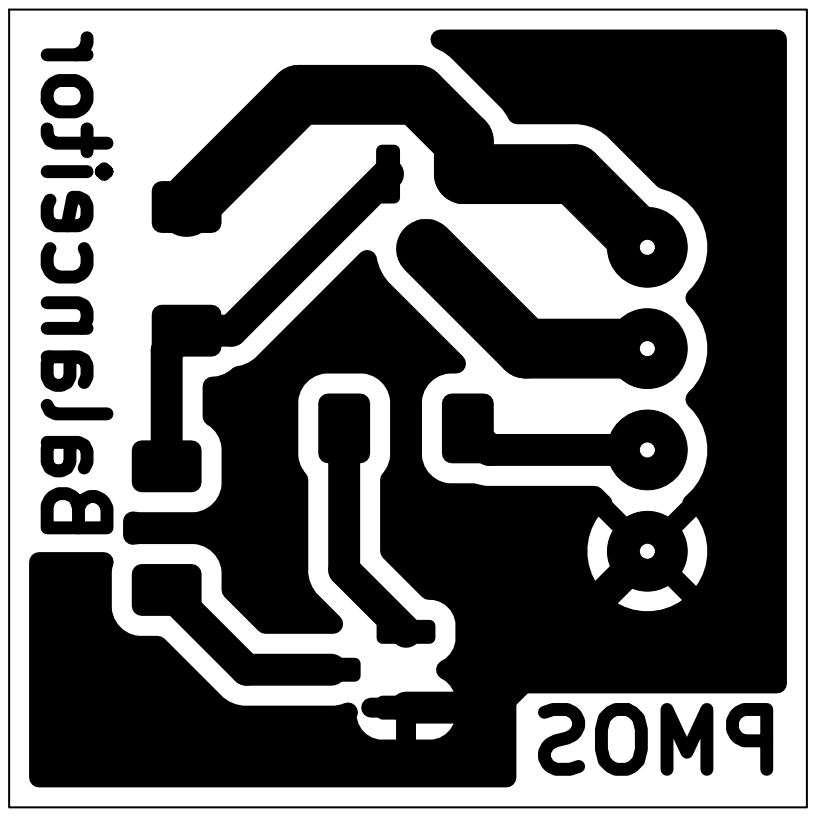
[picture p306: page 1]
