DeniseViltes/Tesis/media/Latex/Prototipo/esquematico.pdf

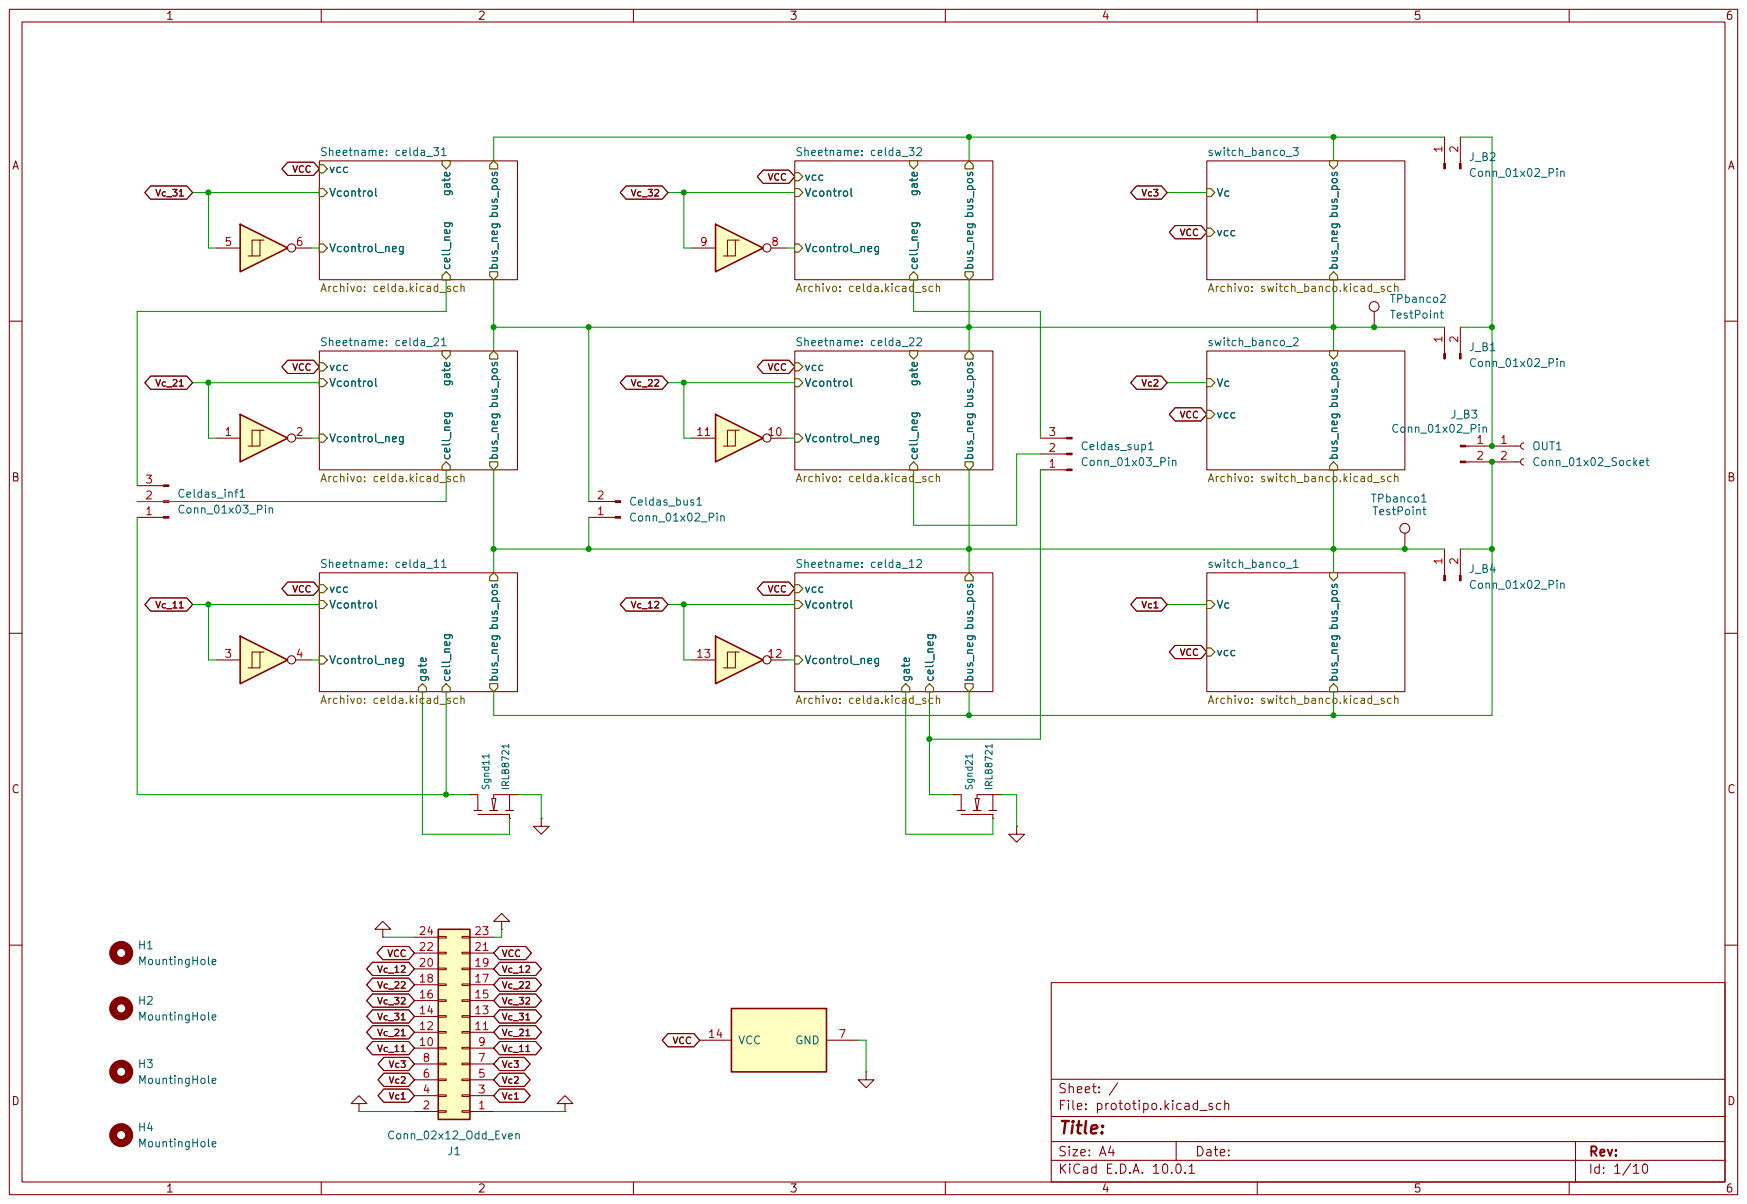
[picture p307: page 1]

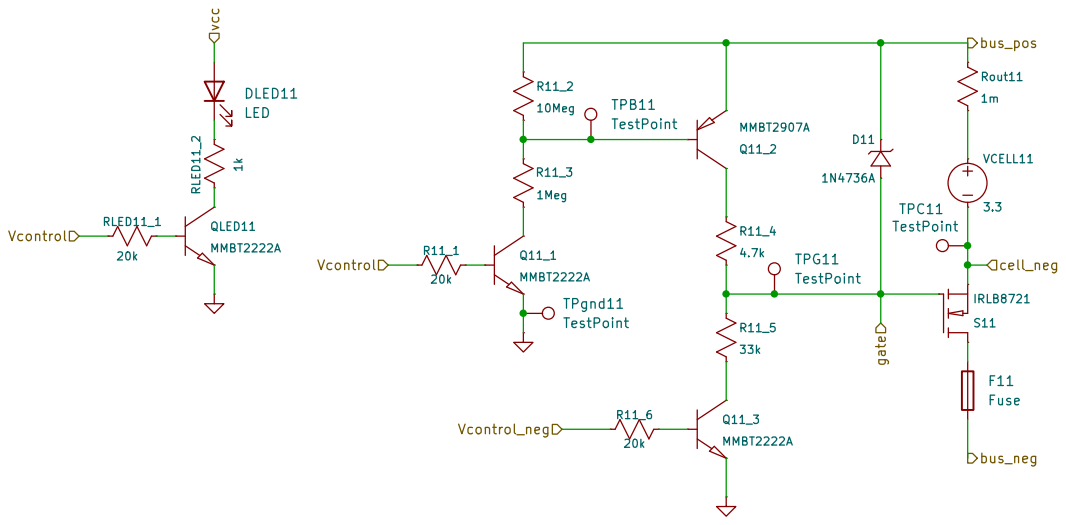
[picture p308: page 2]

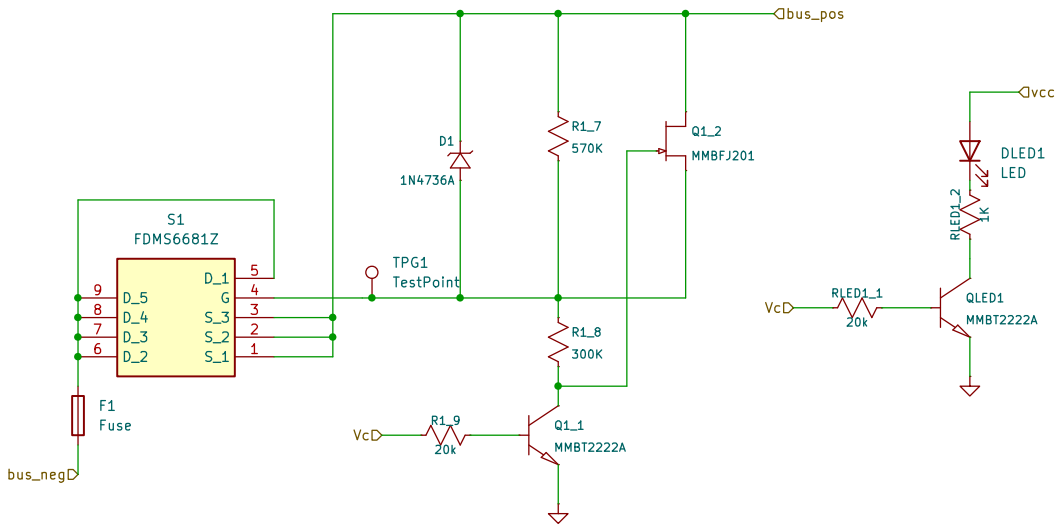
[picture p309: page 3]

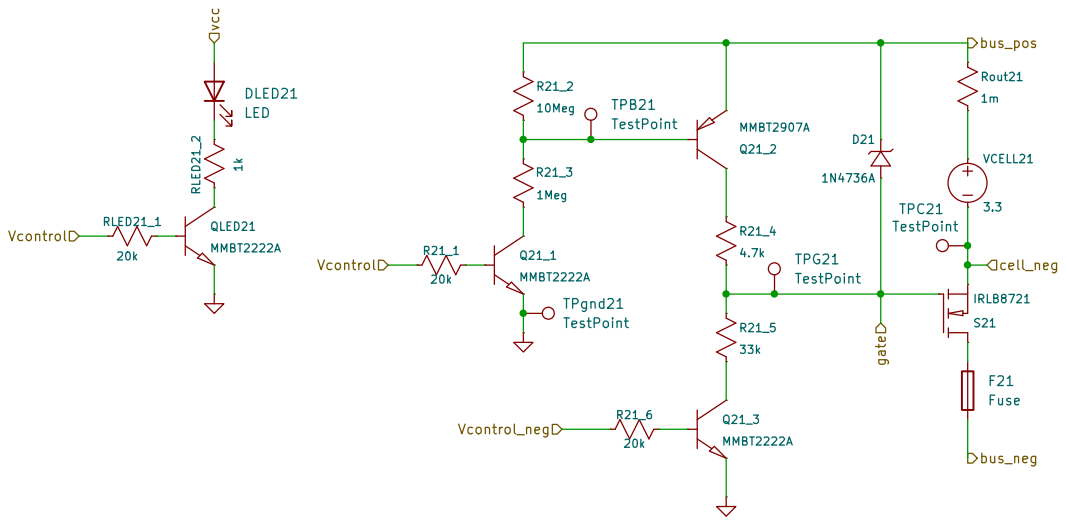
[picture p310: page 4]

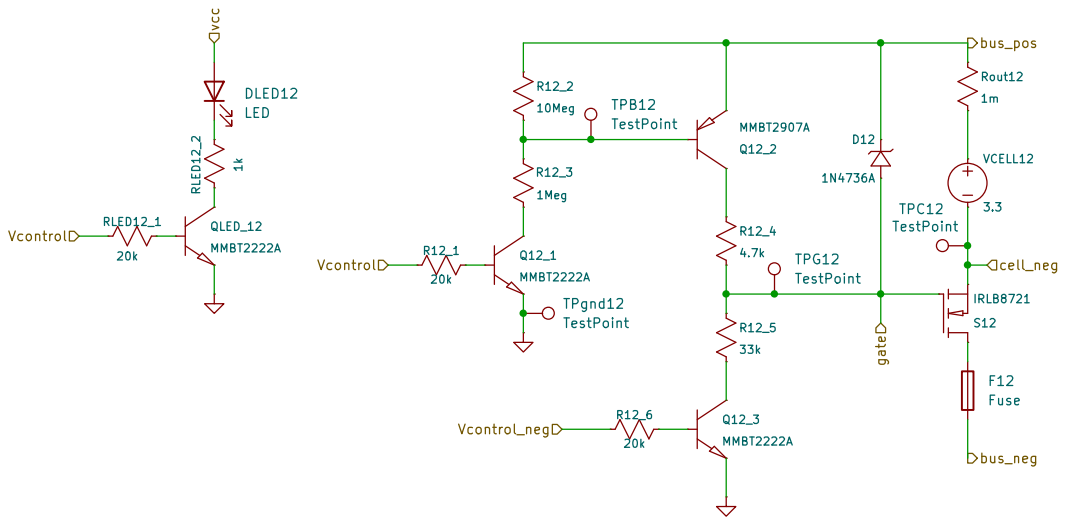
[picture p311: page 5]

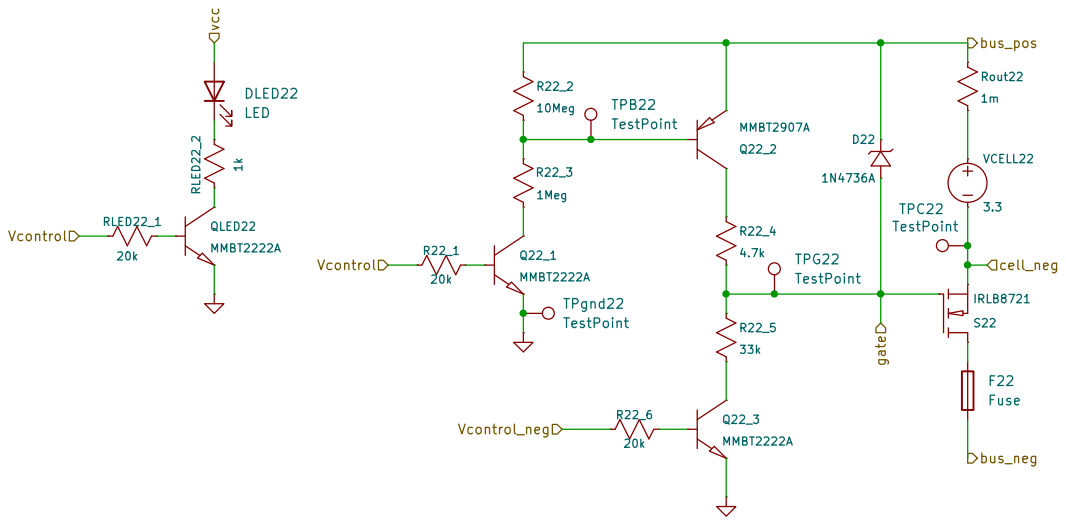
[picture p312: page 6]

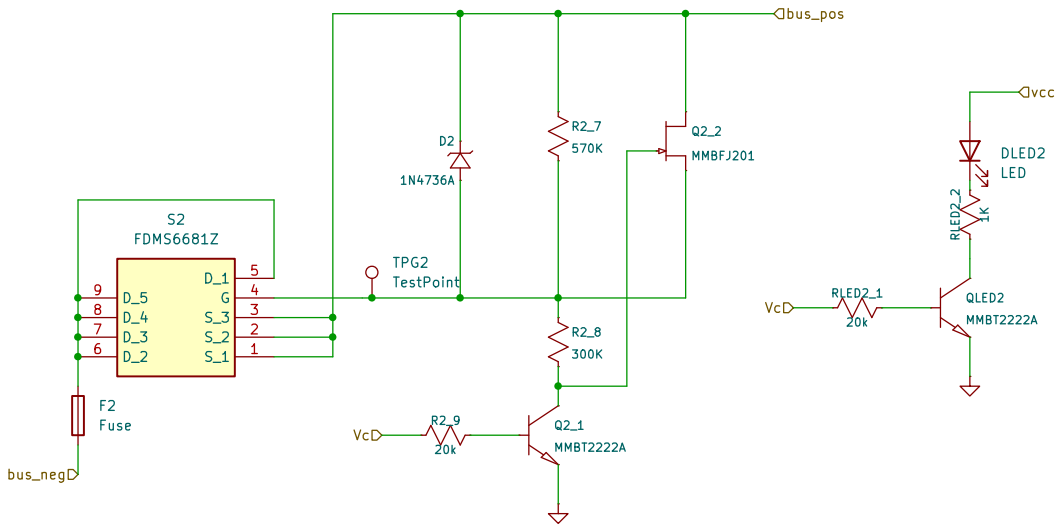
[picture p313: page 7]

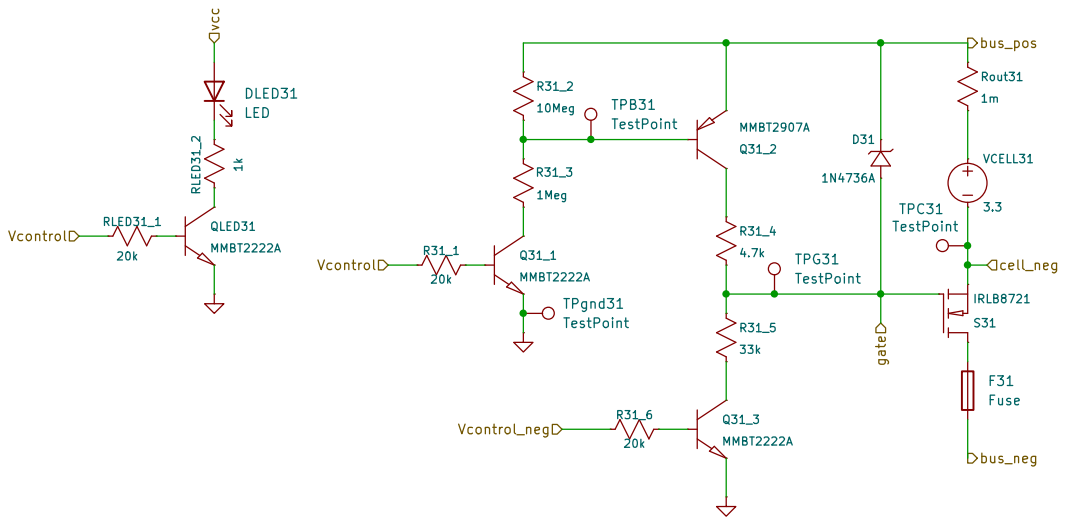
[picture p314: page 8]

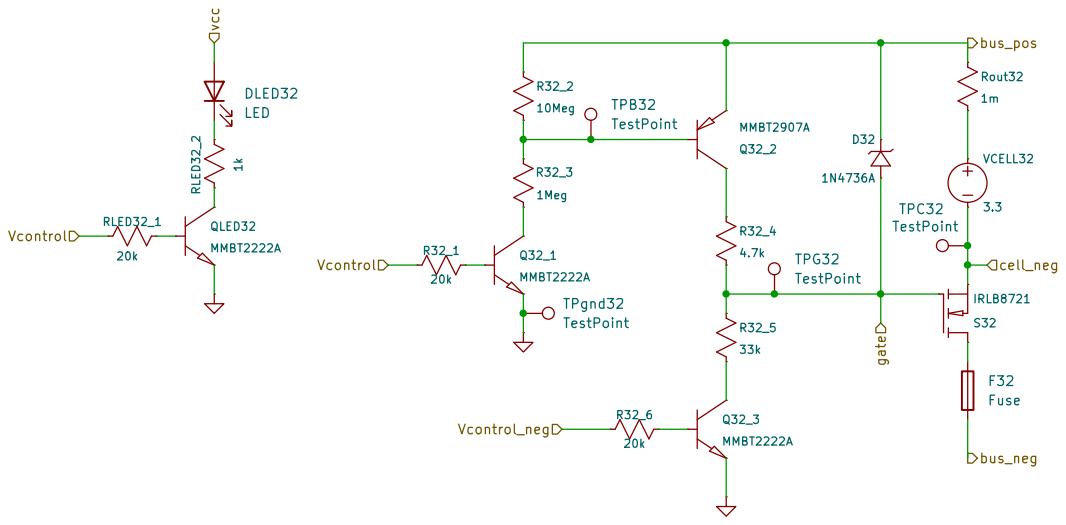
[picture p315: page 9]

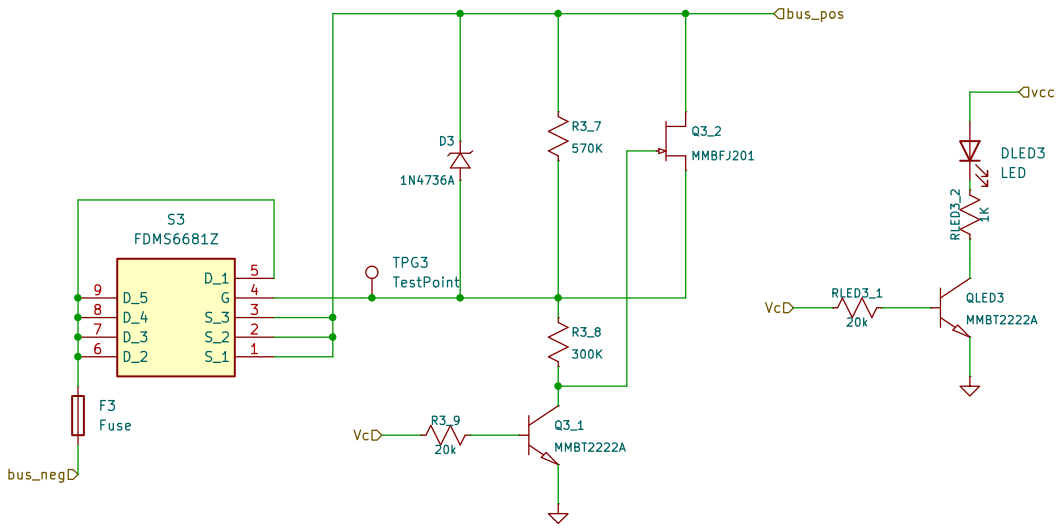
[picture p316: page 10]
