DeniseViltes/Tesis/media/Latex/Prototipo/pcb.pdf

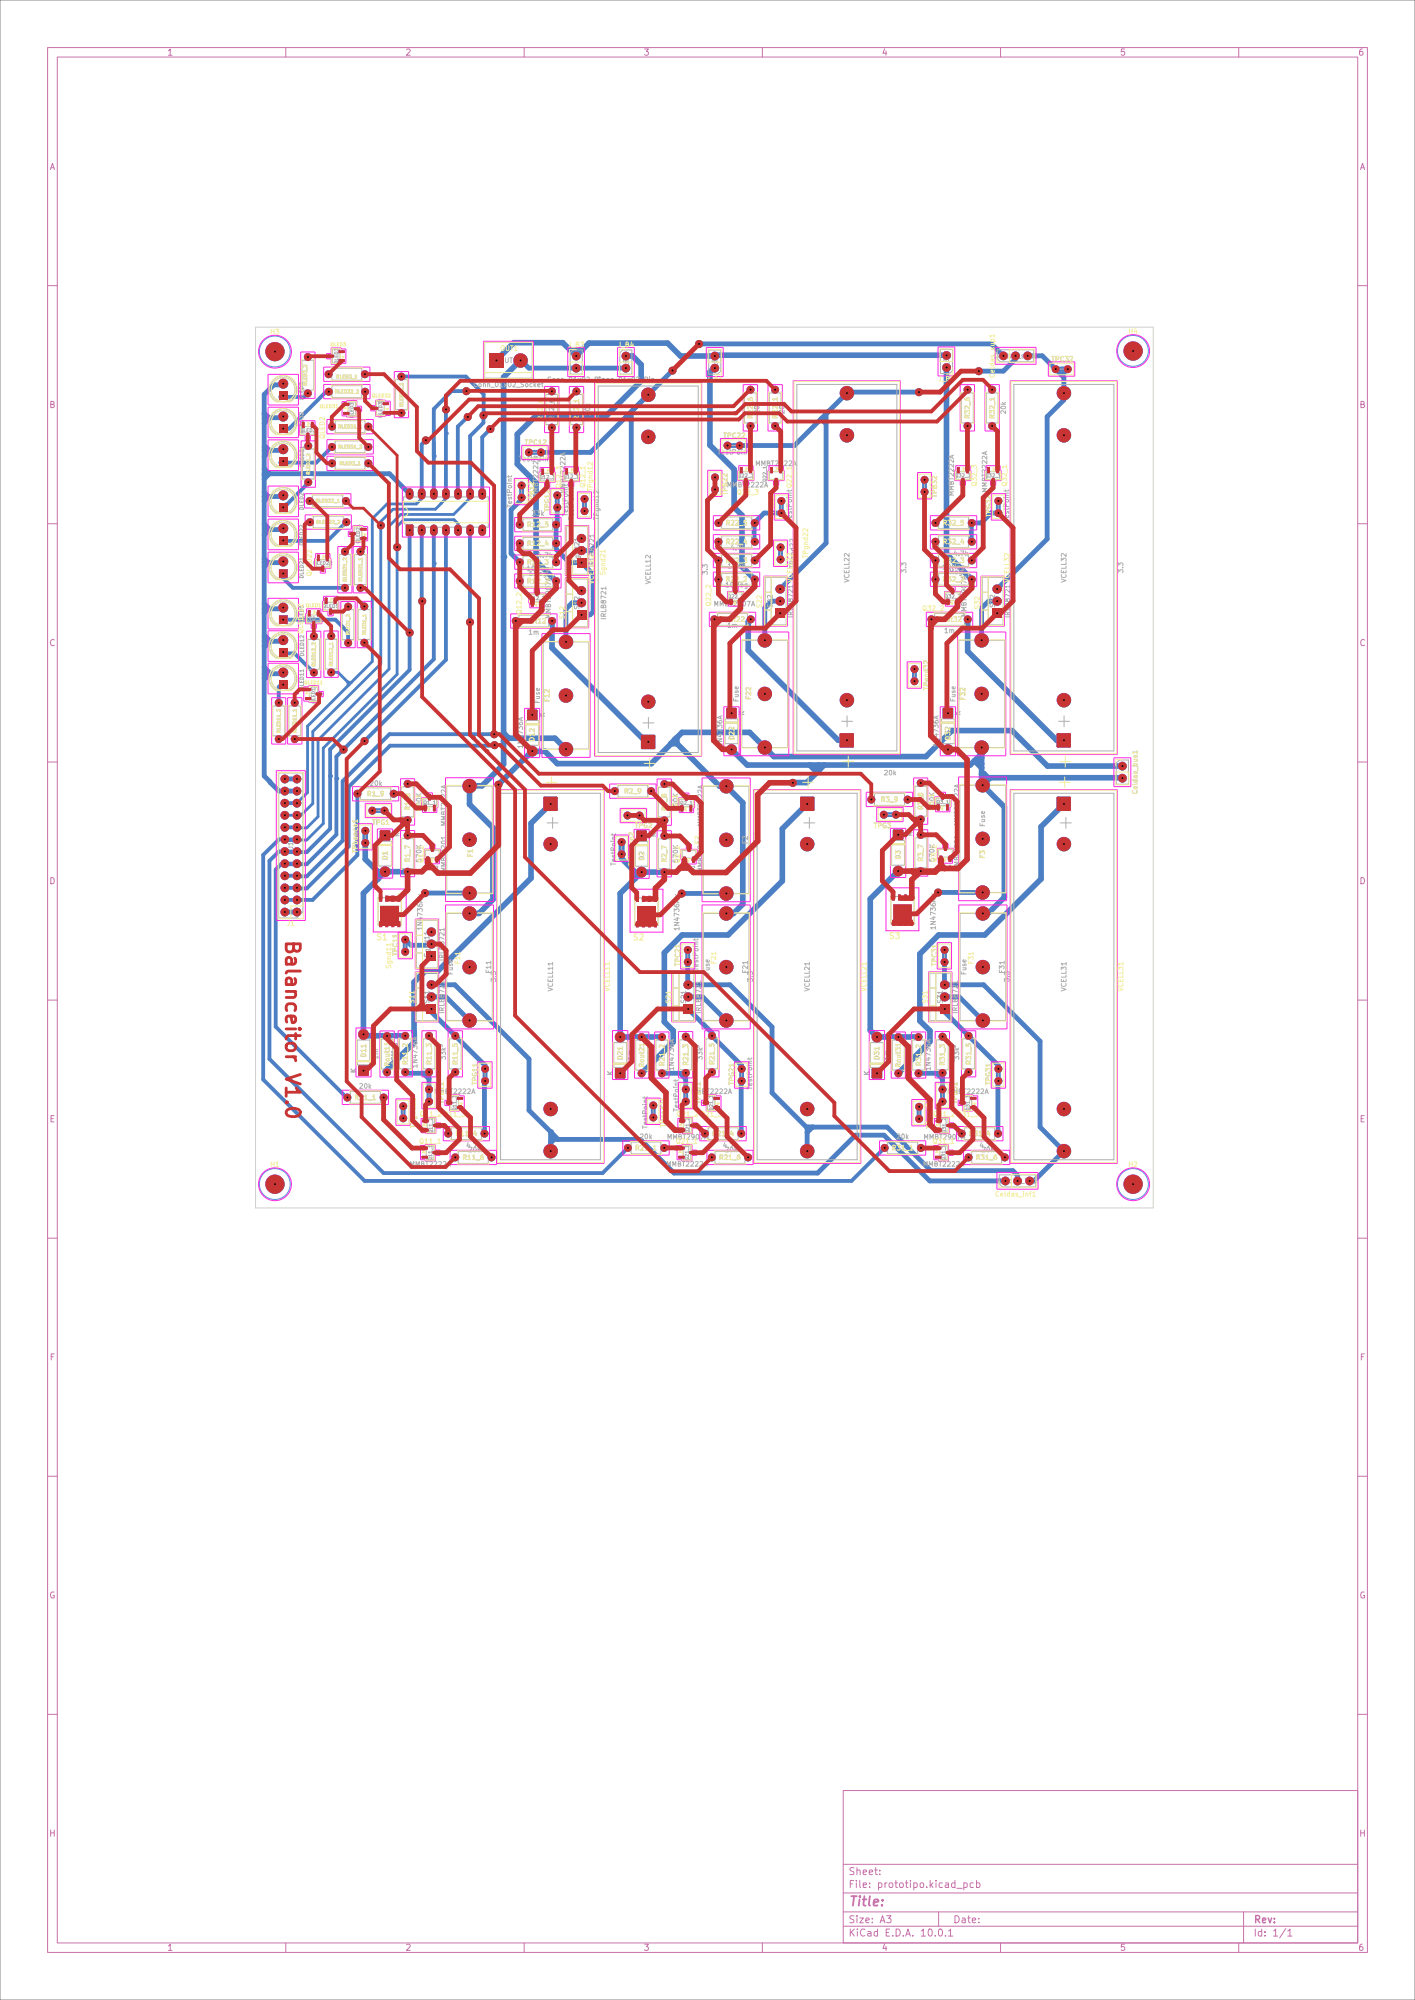
[picture p317: page 1]
