DeniseViltes/Tesis/Ltspice/descartables/prueba_switch_completo_tbjs_ideales.asc

M1: nmos; irlz44n
M2: pmos; irf4905
Q1: npn
Q2: pnp
Q3: npn
Q4: npn
R1: res; 10k
R2: res; 10Meg
R3: res; 1Meg
R4: res; 49k
R5: res; 10k
R6: res; 10k
R7: res; 100k
R8: res; 10k
R9: res; 1k
V1: voltage; 3.3
V2: voltage; PULSE(0 5 10m 1p 1p 10m 20m)
V3: voltage; PULSE(0 5 0 1p 1p 10m 20m)
Named nets: 0
.tran 0 20m 0 1m
.inc D:\\Users\\denis\\OneDrive\\Escritorio\\-\\Estudios\\Facultad\\Actuales\\Tesis\\Switch\\irlz44n.spi
.inc irf4905.spi
