DeniseViltes/Tesis/Ltspice/descartables/pruebas_de_cantidad.asc

Q1: npn; MMBT2222A
Q1_1: npn; MMBT2222A
Q2: npn; MMBT2222A
Q2_1: npn; MMBT2222A
Q3: npn; MMBT2222A
Q3_1: npn; MMBT2222A
Q4: pnp; MMBT2907A
Q5: npn; MMBT2222A
Q6: npn; MMBT2222A
Q7: npn; MMBT2222A
Q8: pnp; MMBT2907A
Q9: npn; MMBT2222A
Q10: npn; MMBT2222A
Q11: npn; MMBT2222A
Q11_1: npn; MMBT2222A
Q11_2: pnp; MMBT2907A
Q11_3: npn; MMBT2222A
Q12: pnp; MMBT2907A
Q12_1: npn; MMBT2222A
Q12_2: pnp; MMBT2907A
Q12_3: npn; MMBT2222A
Q13: npn; MMBT2222A
Q14: npn; MMBT2222A
Q15: pnp; MMBT2907A
Q16: npn; MMBT2222A
Q17: npn; MMBT2222A
Q18: pnp; MMBT2907A
Q19: npn; MMBT2222A
Q20: npn; MMBT2222A
Q21: pnp; MMBT2907A
Q21_1: npn; MMBT2222A
Q21_2: pnp; MMBT2907A
Q21_3: npn; MMBT2222A
Q22: npn; MMBT2222A
Q22_1: npn; MMBT2222A
Q22_2: pnp; MMBT2907A
Q22_3: npn; MMBT2222A
Q23: npn; MMBT2222A
Q24: pnp; MMBT2907A
Q25: npn; MMBT2222A
Q26: npn; MMBT2222A
Q27: pnp; MMBT2907A
Q28: npn; MMBT2222A
Q29: npn; MMBT2222A
Q30: npn; MMBT2222A
Q31: pnp; MMBT2907A
Q31_2: pnp; MMBT2907A
Q31_3: npn; MMBT2222A
Q32_2: pnp; MMBT2907A
Q32_3: npn; MMBT2222A
R1: res; 300k
R1_7: res; 570K
R1_8: res; 300K
R1_9: res; 20k
R2: res; 49.9k
R2_7: res; 570K
R2_8: res; 300K
R2_9: res; 20k
R3: res; 1Meg
R4: res; 10Meg
R5: res; 20k
R6: res; 300k
R7: res; 49.9k
R8: res; 1Meg
R9: res; 10Meg
R10: res; 20k
R11: res; 20k
R11_1: res; 20k
R11_2: res; 10Meg
R11_3: res; 1Meg
R11_4: res; 49.9k
R11_5: res; 300k
R11_6: res; 20k
R12: res; 20k
R12_1: res; 20k
R12_2: res; 10Meg
R12_3: res; 1Meg
R12_4: res; 49.9k
R12_5: res; 300k
R12_6: res; 20k
R13: res; 20k
R14: res; 300K
R15: res; 570K
R16: res; 300k
R17: res; 49.9k
R18: res; 1Meg
R19: res; 10Meg
R20: res; 20k
R21: res; 300k
R21_1: res; 20k
R21_2: res; 10Meg
R21_3: res; 1Meg
R21_4: res; 49.9k
R21_5: res; 300k
R21_6: res; 20k
R22: res; 49.9k
R22_1: res; 20k
R22_2: res; 10Meg
R22_3: res; 1Meg
R22_4: res; 49.9k
R22_5: res; 300k
R22_6: res; 20k
R23: res; 1Meg
R24: res; 10Meg
R25: res; 20k
R26: res; 20k
R27: res; 20k
R28: res; 20k
R29: res; 300K
R30: res; 570K
R31: res; 300k
R32: res; 49.9k
R33: res; 1Meg
R34: res; 10Meg
R35: res; 20k
R36: res; 300k
R37: res; 49.9k
R38: res; 1Meg
R39: res; 10Meg
R40: res; 20k
R41: res; 20k
R42: res; 20k
R43: res; 300k
R44: res; 49.9k
R45: res; 1Meg
R46: res; 10Meg
R47: res; 20k
R48: res; 20k
R49: res; 300k
R50: res; 49.9k
R51: res; 1Meg
R52: res; 10Meg
R53: res; 20k
R54: res; 20k
R55: res; 300k
R56: res; 49.9k
R57: res; 1Meg
R58: res; 10Meg
R59: res; 20k
R60: res; 300k
R61: res; 49.9k
R62: res; 1Meg
R63: res; 10Meg
R64: res; 20k
R65: res; 20k
R66: res; 20k
R67: res; 20k
R68: res; 300K
R69: res; 570K
R70: res; 300k
R71: res; 49.9k
R72: res; 1Meg
R73: res; 10Meg
R74: res; 20k
R75: res; 20k
RL: res; 1k
Rout1: res; 1m
Rout2: res; 1m
Rout3: res; 1m
Rout4: res; 1m
Rout5: res; 1m
Rout6: res; 1m
Rout7: res; 1m
Rout8: res; 1m
Rout9: res; 1m
Rout10: res; 1m
Rout11: res; 1m
Rout12: res; 1m
Rout13: res; 1m
Rout21: res; 1m
Rout22: res; 1m
S1: pmos; AO3401A
S2: pmos; AO3401A
S3: nmos; IRLB8721
S4: nmos; IRLB8721
S5: pmos; AO3401A
S6: pmos; AO3401A
S7: nmos; IRLB8721
S8: nmos; IRLB8721
S9: nmos; IRLB8721
S10: nmos; IRLB8721
S11: nmos; IRLB8721
S12: nmos; IRLB8721
S13: nmos; IRLB8721
S14: nmos; IRLB8721
S15: pmos; AO3401A
S16: nmos; IRLB8721
S21: nmos; IRLB8721
S22: nmos; IRLB8721
S31: nmos; IRLB8721
S32: nmos; IRLB8721
Vcell1: voltage; 3.3
Vcell2: voltage; 3.3
Vcell3: voltage; 3.3
Vcell4: voltage; 3.3
Vcell5: voltage; 3.3
Vcell6: voltage; 3.3
Vcell7: voltage; 3.3
Vcell8: voltage; 3.3
Vcell9: voltage; 3.3
Vcell10: voltage; 3.3
Vcell11: voltage; 3.3
Vcell12: voltage; 3.3
Vcell13: voltage; 3.3
Vcell21: voltage; 3.3
Vcell22: voltage; 3.3
Vcontrol1: voltage; PULSE(0 5 0 1p 1p 10m 20m)
Vcontrol2: voltage; PULSE(0 5 10m 1p 1p 10m 20m)
Vgnd: voltage; 0
Vmedir: voltage; 0
Voff: voltage; 0
Von: voltage; 0
Named nets: 0, VcMAS, VcMENOS, VcOFF, VcON, out_neg, out_1, out_pos
.tran 0 40m 0 10u
.MODEL MMBT2222A  NPN (IS=25.4f NF=1.00 BF=274 VAF=114 
+ IKF=0.121 ISE=14.3p NE=2.00 BR=4.00 NR=1.00 
+ VAR=24.0 IKR=0.300 RE=0.219 RB=0.877 RC=87.7m 
+ XTB=1.5 CJE=27.6p VJE=1.10 MJE=0.500 CJC=14.2p VJC=0.300 
+ MJC=0.300 TF=622p TR=124n EG=1.12 )
.MODEL MMBT2907A  PNP (IS=60.7f NF=1.00 BF=312 VAF=139 
+ IKF=0.219 ISE=26.0p NE=2.00 BR=4.00 NR=1.00 
+ VAR=20.0 IKR=0.540 RE=85.8m RB=0.343 RC=34.3m 
+ XTB=1.5 CJE=50.4p VJE=1.10 MJE=0.500 CJC=23.1p VJC=0.300 
+ MJC=0.300 TF=758p TR=123n EG=1.12 )
.model IRF530 VDMOS(Rg=3 Vto=4 Rd=50m Rs=12m Rb=60m Kp=5 lambda=.01 Cgdmax=1n Cgdmin=.26n Cgs=.2n Cjo=.4n Is=52p ksubthres=.1 mfg=International_Rectifier Vds=100 Ron=160m Qg=26n)
.model AONS32304 VDMOS(Kp=239 Rs=0.42m Rd=1.2m Rg=3.0 Vto=2.16 VtoTc=-2.8m Bex=-2.07 mtriode=1.1 Ksubthres=0.1 Lambda=0.158 Cgdmax=1420p Cgdmin=288p Cgs=5352p tt=19n A=0.7 Is=2.35E-11 N=1.017 Eg=1.07 Rb=0.1m Trb1=-1 BV=33 IBV=250u M=0.456 Vj=0.56 Cjo=1090.0pF mfg=AOS Vds=30 Ron=1.8m Qg=40n)
.inc SiDR140DP_PS.LIB
.inc AO3401A.sub
.inc IRLB8721.sub
.op
