DeniseViltes/Tesis/Ltspice/proyectos/pruebas_eliminar_cell_neg/Pruebas aumentar cell_neg.asc

CL: cap; 10µ
I_GND: voltage; 0
Minv1_1: pmos; AO3401A
Minv1_2: pmos; AO3401A
Minv1_3: pmos; AO3401A
Minv1_4: pmos; AO3401A
Minv2_1: nmos; AO3400
Minv2_2: nmos; AO3400
Minv2_3: nmos; AO3400
Minv2_4: nmos; AO3400
Q1_1: npn; MMBT2222A
Q1_2: npn; MMBT2222A
Q1_3: npn; MMBT2222A
Q1_4: npn; MMBT2222A
Q2_1: pnp; MMBT2907A
Q2_2: pnp; MMBT2907A
Q2_3: pnp; MMBT2907A
Q2_4: pnp; MMBT2907A
Q3_1: npn; MMBT2222A
Q3_2: npn; MMBT2222A
Q3_3: npn; MMBT2222A
Q3_4: npn; MMBT2222A
Q4_1: npn; MMBT2222A
Q4_2: npn; MMBT2222A
Q4_3: npn; MMBT2222A
Q4_4: npn; MMBT2222A
Q5_1: njf; MMBFJ201
Q5_2: njf; MMBFJ201
Q5_3: njf; MMBFJ201
Q5_4: njf; MMBFJ201
R1_1: res; 22k
R1_2: res; 22k
R1_3: res; 22k
R1_4: res; 22k
R2_1: res; 560k
R2_2: res; 560k
R2_3: res; 560k
R2_4: res; 560k
R3_1: res; 56k
R3_2: res; 56k
R3_3: res; 56k
R3_4: res; 56k
R4_1: res; 4.7k
R4_2: res; 4.7k
R4_3: res; 4.7k
R4_4: res; 4.7k
R5_1: res; 33k
R5_2: res; 33k
R5_3: res; 33k
R5_4: res; 33k
R6_1: res; 22k
R6_2: res; 22k
R6_3: res; 22k
R6_4: res; 22k
R7_1: res; 560k
R7_2: res; 560k
R7_3: res; 560k
R7_4: res; 560k
R8_1: res; 330k
R8_2: res; 330k
R8_3: res; 330k
R8_4: res; 330k
R9_1: res; 22k
R9_2: res; 22k
R9_3: res; 22k
R9_4: res; 22k
Rbase_1: res; 560k
Rbase_2: res; 560k
Rbase_3: res; 560k
Rbase_4: res; 560k
Rfuse_1: res; 1m
Rfuse_2: res; 1m
Rfuse_3: res; 1m
Rfuse_4: res; 1m
Rin1_1: res; 330
Rin1_2: res; 330
Rin1_3: res; 330
Rin1_4: res; 330
Rin2_1: res; 330
Rin2_2: res; 330
Rin2_3: res; 330
Rin2_4: res; 330
RL: res; 47
S1_1: nmos; IRLB8721
S1_2: nmos; IRLB8721
S1_3: nmos; IRLB8721
S1_4: nmos; IRLB8721
S2_1: pmos; irlml6402
S2_2: pmos; irlml6402
S2_3: pmos; irlml6402
S2_4: pmos; irlml6402
Vc: voltage; 5
Vcell1: voltage; 3.2
Vcell2: voltage; 3.2
Vcell3: voltage; 3.2
Vcell4: voltage; 3.2
Vcontrol1: voltage; PULSE(0 5 0 1p 1p 10m 20m)
Vcontrol2: voltage; PULSE(0 5 10m 1p 1p 10m 20m)
Voff: voltage; 0
Von: voltage; 5
Named nets: 0, VcMAS, VcMENOS, VcOFF, VcON, Vcc, bus_pos2, bus_neg1, cell_neg1, cell_neg2, bus_pos1, cell_neg3, cell_neg4, bus_pos3, bus_pos4
.tran 0 40m 0 10u
.MODEL MMBT2222A  NPN (IS=25.4f NF=1.00 BF=274 VAF=114 IKF=0.121 ISE=14.3p NE=2.00 BR=4.00 NR=1.00 VAR=24.0 IKR=0.300 RE=0.219 RB=0.877 RC=87.7m XTB=1.5 CJE=27.6p VJE=1.10 MJE=0.500 CJC=14.2p VJC=0.300 MJC=0.300 TF=622p TR=124n EG=1.12)
.MODEL MMBT2907A  PNP (IS=60.7f NF=1.00 BF=312 VAF=139 IKF=0.219 ISE=26.0p NE=2.00 BR=4.00 NR=1.00 VAR=20.0 IKR=0.540 RE=85.8m RB=0.343 RC=34.3m XTB=1.5 CJE=50.4p VJE=1.10 MJE=0.500 CJC=23.1p VJC=0.300 MJC=0.300 TF=758p TR=123n EG=1.12)
.model AONS32304 VDMOS(Kp=239 Rs=0.42m Rd=1.2m Rg=3.0 Vto=2.16 VtoTc=-2.8m Bex=-2.07 mtriode=1.1 Ksubthres=0.1 Lambda=0.158 Cgdmax=1420p Cgdmin=288p Cgs=5352p tt=19n A=0.7 Is=2.35E-11 N=1.017 Eg=1.07 Rb=0.1m Trb1=-1 BV=33 IBV=250u M=0.456 Vj=0.56 Cjo=1090.0pF mfg=AOS Vds=30 Ron=1.8m Qg=40n)
.model MMBFJ201 NJF(BETA=0.000896 IS=3E-12 VTO=-0.794 LAMBDA=0.02 RD=0.001 RS=0.0013)
.inc AO3401A.sub
.inc IRLB8721.sub
.inc 1N4736A.sub
.inc FDMS6681Z.lib
.inc 1N4730A.sub
.model LED_RED D(Is=2e-9 N=2.2 Rs=10 Bv=5 Ibv=0.1 Cjo=20p M=0.4 Vj=0.65)
.inc irlml6402.spi
.include AO3400.lib
.include AO3401A.sub
