DeniseViltes/Tesis/Ltspice/proyectos/prueba_jfet/Prueba JFETs.asc

Fusible1: res; 1m
Fusible3: res; 1m
Fusible4: res; 1m
Fusible5: res; 1m
J1: njf; MMBFJ201
J2: njf; MMBF4393
LED1: LED
LED2: LED
LED3: LED
LED4: LED
LED5: LED
LED6: LED
Minv1: pmos; AO3401A
Minv2: nmos; AO3400
Minv3: pmos; AO3401A
Minv4: nmos; AO3400
Minv5: pmos; AO3401A
Minv6: nmos; AO3400
Q1: npn; MMBT2222A
Q2: pnp; MMBT2907A
Q3: npn; MMBT2222A
Q4: npn; MMBT2222A
Q5: npn; MMBT2222A
Q6: npn; MMBT2222A
Q7: pnp; MMBT2907A
Q8: npn; MMBT2222A
Q9: npn; MMBT2222A
Q10: npn; MMBT2222A
Q11: pnp; MMBT2907A
Q12: npn; MMBT2222A
Qled1: npn; MMBT2222A
Qled2: npn; MMBT2222A
Qled3: npn; MMBT2222A
Qled4: npn; MMBT2222A
Qled5: npn; MMBT2222A
Qled6: npn; MMBT2222A
R1: res; 20k
R2: res; 100k
R3: res; 10k
R4: res; 4.7k
R5: res; 33k
R6: res; 20k
R7: res; 570k
R8: res; 330k
R9: res; 20k
R10: res; 33k
R11: res; 4.7k
R12: res; 10k
R13: res; 100k
R14: res; 20k
R15: res; 20k
R16: res; 20k
R17: res; 570k
R18: res; 330k
R19: res; 33k
R20: res; 4.7k
R21: res; 10k
R22: res; 100k
R23: res; 20k
R24: res; 20k
R25: res; 20k
R26: res; 570k
R27: res; 330k
Rdiv1: res; 10K
Rdiv2: res; 10K
Rdiv: res; 10K
RL1: res; 47
RL2: res; 47
RL: res; 47
Rled1: res; 560
Rled2: res; 20k
Rled3: res; 560
Rled4: res; 20k
Rled5: res; 560
Rled6: res; 20k
Rled7: res; 560
Rled8: res; 20k
Rled11: res; 20k
Rled12: res; 560
Rled21: res; 20k
Rled22: res; 560
Rsr1: res; 330
Rsr2: res; 330
Rsr: res; 330
S1: nmos; IRLB8721
S2: pmos; irlml6402
S3: nmos; IRLB8721
S4: pmos; irlml6402
S5: nmos; IRLB8721
S6: pmos; irlml6402
Sgnd1: nmos; IRLB8721
Sgnd2: nmos; IRLB8721
Sgnd3: nmos; IRLB8721
vcc1: voltage; 5
Vcell1: voltage; 3.3
Vcell2: voltage; 3.3
Vcell3: voltage; 3.3
Vcell4: voltage; 3.3
Vcell5: voltage; 3.3
Vcell6: voltage; 3.3
vcontrol1: voltage; PULSE(0 5 0 1p 1p 10m 20m)
vcontrol2: voltage; PULSE(0 5 10m 1p 1p 10m 20m)
Named nets: 0, Vcc, PULSO, bus_pos1, bus_neg1, PULSO_neg, bus_pos2, bus_neg2, bus_pos3, bus_neg3
.include AO3400.lib
.include AO3401A.sub
.include irlml6402.spi
para habilitar la salida del sr, ~OE tiene que estar a tierra
.tran 0 40m 0 10u uic
.MODEL MMBT2222A  NPN (IS=25.4f NF=1.00 BF=274 VAF=114 IKF=0.121 ISE=14.3p NE=2.00 BR=4.00 NR=1.00 VAR=24.0 IKR=0.300 RE=0.219 RB=0.877 RC=87.7m XTB=1.5 CJE=27.6p VJE=1.10 MJE=0.500 CJC=14.2p VJC=0.300 MJC=0.300 TF=622p TR=124n EG=1.12)
.MODEL MMBT2907A  PNP (IS=60.7f NF=1.00 BF=312 VAF=139 IKF=0.219 ISE=26.0p NE=2.00 BR=4.00 NR=1.00 VAR=20.0 IKR=0.540 RE=85.8m RB=0.343 RC=34.3m XTB=1.5 CJE=50.4p VJE=1.10 MJE=0.500 CJC=23.1p VJC=0.300 MJC=0.300 TF=758p TR=123n EG=1.12)
.model AONS32304 VDMOS(Kp=239 Rs=0.42m Rd=1.2m Rg=3.0 Vto=2.16 VtoTc=-2.8m Bex=-2.07 mtriode=1.1 Ksubthres=0.1 Lambda=0.158 Cgdmax=1420p Cgdmin=288p Cgs=5352p tt=19n A=0.7 Is=2.35E-11 N=1.017 Eg=1.07 Rb=0.1m Trb1=-1 BV=33 IBV=250u M=0.456 Vj=0.56 Cjo=1090.0pF mfg=AOS Vds=30 Ron=1.8m Qg=40n)
.model MMBFJ201 NJF(BETA=0.000896 IS=3E-12 VTO=-0.794 LAMBDA=0.02 RD=0.001 RS=0.0013)
.model LED_RED D(Is=2e-9 N=2.2 Rs=10 Bv=5 Ibv=0.1 Cjo=20p M=0.4 Vj=0.65)
.inc AO3401A.sub
.inc IRLB8721.sub
.inc 1N4736A.sub
.inc FDMS6681Z.lib
.inc 1N4730A.sub
.inc MMBF4393.lib
.options plotwinsize=0
.options numdgt=6
.options reltol=0.001 abstol=1u
.options solver=alternate
.op
Con el JFET original (MMBFJ201):
Con el nuevo JFET (MMBF4393):
Sin JFET:
