DeniseViltes/Tesis/Ltspice/proyectos/circuito_modular/Testeo de cell_neg.asc

D1: LED
D2: LED
D3: LED
D4: LED
D5: LED
D6: LED
D7: LED
D13: LED
M1: pmos; AO3401A
M2: nmos; AO3400
M3: pmos; AO3401A
M4: nmos; AO3400
M5: pmos; AO3401A
M6: nmos; AO3400
M9: pmos; AO3401A
M10: nmos; AO3400
Q1: npn; MMBT2222A
Q2: njf; MMBFJ201
Q2_1: npn; MMBT2222A
Q3: npn; MMBT2222A
Q4: pnp; MMBT2907A
Q5: npn; MMBT2222A
Q6: npn; MMBT2222A
Q7: npn; MMBT2222A
Q8: npn; MMBT2222A
Q9: njf; MMBFJ201
Q10: npn; MMBT2222A
Q11: npn; MMBT2222A
Q12: npn; MMBT2222A
Q13: pnp; MMBT2907A
Q14: npn; MMBT2222A
Q15: npn; MMBT2222A
Q16: npn; MMBT2222A
Q17: njf; MMBFJ201
Q18: npn; MMBT2222A
Q19: npn; MMBT2222A
Q20: pnp; MMBT2907A
Q21: npn; MMBT2222A
Q22: npn; MMBT2222A
Q22_1: npn; MMBT2222A
Q22_2: pnp; MMBT2907A
Q22_3: npn; MMBT2222A
Q23: npn; MMBT2222A
Q24: njf; MMBFJ201
R1: res; 33k
R2: res; 4.7k
R2_7: res; 560k
R2_8: res; 330k
R2_9: res; 22k
R3: res; 10k
R4: res; 100k
R5: res; 22k
R6: res; 22k
R7: res; 1k
R8: res; 22k
R9: res; 22k
R10: res; 560k
R11: res; 1k
R12: res; 22k
R13: res; 1k
R14: res; 22k
R15: res; 1k
R16: res; 330k
R17: res; 33k
R18: res; 22k
R19: res; 4.7k
R20: res; 10k
R21: res; 100k
R22: res; 22k
R22_1: res; 22k
R22_2: res; 100k
R22_3: res; 10k
R22_4: res; 4.7k
R22_5: res; 33k
R22_6: res; 22k
R23: res; 22k
R24: res; 22k
R25: res; 560k
R26: res; 1k
R27: res; 22k
R28: res; 1k
R29: res; 22k
R30: res; 330k
R31: res; 33k
R32: res; 4.7k
R33: res; 10k
R34: res; 100k
R35: res; 22k
R36: res; 22k
R37: res; 22k
R38: res; 560k
R39: res; 1k
R40: res; 22k
R41: res; 1k
R42: res; 22k
R43: res; 330k
RL: res; 4
Rout1: res; 1m
Rout2: res; 1m
Rout3: res; 1m
Rout22: res; 1m
S1: nmos; IRLB8721
S2: pmos; irlml6402
S3: nmos; IRLB8721
S4: pmos; irlml6402
S5: nmos; IRLB8721
S6: pmos; irlml6402
S7: nmos; IRLB8721
S8: pmos; irlml6402
S22: nmos; IRLB8721
Vc: voltage; 5
Vcell1: voltage; 3.2
Vcell2: voltage; 3.2
Vcell3: voltage; 3.2
Vcell22: voltage; 3.2
Vcontrol1: voltage; PULSE(0 5 0 1p 1p 10m 20m)
Vcontrol2: voltage; PULSE(0 5 10m 1p 1p 10m 20m)
Voff: voltage; 0
Von: voltage; 5
Named nets: 0, VcMAS, VcMENOS, VcOFF, VcON, out_2, Vcc
.tran 0 40m 0 10u
.MODEL MMBT2222A  NPN (IS=25.4f NF=1.00 BF=274 VAF=114 IKF=0.121 ISE=14.3p NE=2.00 BR=4.00 NR=1.00 VAR=24.0 IKR=0.300 RE=0.219 RB=0.877 RC=87.7m XTB=1.5 CJE=27.6p VJE=1.10 MJE=0.500 CJC=14.2p VJC=0.300 MJC=0.300 TF=622p TR=124n EG=1.12)
.MODEL MMBT2907A  PNP (IS=60.7f NF=1.00 BF=312 VAF=139 IKF=0.219 ISE=26.0p NE=2.00 BR=4.00 NR=1.00 VAR=20.0 IKR=0.540 RE=85.8m RB=0.343 RC=34.3m XTB=1.5 CJE=50.4p VJE=1.10 MJE=0.500 CJC=23.1p VJC=0.300 MJC=0.300 TF=758p TR=123n EG=1.12)
.model AONS32304 VDMOS(Kp=239 Rs=0.42m Rd=1.2m Rg=3.0 Vto=2.16 VtoTc=-2.8m Bex=-2.07 mtriode=1.1 Ksubthres=0.1 Lambda=0.158 Cgdmax=1420p Cgdmin=288p Cgs=5352p tt=19n A=0.7 Is=2.35E-11 N=1.017 Eg=1.07 Rb=0.1m Trb1=-1 BV=33 IBV=250u M=0.456 Vj=0.56 Cjo=1090.0pF mfg=AOS Vds=30 Ron=1.8m Qg=40n)
.model MMBFJ201 NJF(BETA=0.000896 IS=3E-12 VTO=-0.794 LAMBDA=0.02 RD=0.001 RS=0.0013)
.inc AO3401A.sub
.inc IRLB8721.sub
.inc 1N4736A.sub
.inc FDMS6681Z.lib
.inc 1N4730A.sub
.model LED_RED D(Is=2e-9 N=2.2 Rs=10 Bv=5 Ibv=0.1 Cjo=20p M=0.4 Vj=0.65)
.inc irlml6402.spi
.include AO3400.lib
.include AO3401A.sub
.op
.step param vcell 2.5 3.65 0.1
.step param vcell list 2.5 2.8 3.0 3.2 3.3 3.45 3.65
