DeniseViltes/Tesis/Ltspice/proyectos/nuevo_pmos/prueba de potencia - 5 bancos_AO3401.asc

A1: inv
A2: inv
A3: inv
A4: inv
A5: inv
A6: inv
A7: inv
A8: inv
A9: inv
D1: LED
D2: LED
D3: LED
D4: LED
D5: LED
D6: LED
D7: LED
D8: LED
D9: LED
D10: LED
D11: LED
D12: LED
D13: LED
D14: LED
Q1: npn; MMBT2222A
Q1_1: npn; MMBT2222A
Q2: npn; MMBT2222A
Q2_1: npn; MMBT2222A
Q3: npn; MMBT2222A
Q3_1: npn; MMBT2222A
Q4: npn; MMBT2222A
Q5: npn; MMBT2222A
Q6: npn; MMBT2222A
Q7: npn; MMBT2222A
Q8: npn; MMBT2222A
Q9: npn; MMBT2222A
Q10: npn; MMBT2222A
Q11: npn; MMBT2222A
Q12: npn; MMBT2222A
Q12_1: npn; MMBT2222A
Q12_2: pnp; MMBT2907A
Q12_3: npn; MMBT2222A
Q13: pnp; MMBT2907A
Q14: npn; MMBT2222A
Q15: npn; MMBT2222A
Q16: pnp; MMBT2907A
Q17: npn; MMBT2222A
Q18: npn; MMBT2222A
Q19: npn; MMBT2222A
Q20: npn; MMBT2222A
Q21: npn; MMBT2222A
Q21_1: npn; MMBT2222A
Q21_2: pnp; MMBT2907A
Q21_3: npn; MMBT2222A
Q22: npn; MMBT2222A
Q22_1: npn; MMBT2222A
Q22_2: pnp; MMBT2907A
Q22_3: npn; MMBT2222A
Q23: pnp; MMBT2907A
Q24: npn; MMBT2222A
Q25: npn; MMBT2222A
Q26: pnp; MMBT2907A
Q27: npn; MMBT2222A
Q28: npn; MMBT2222A
Q29: npn; MMBT2222A
Q30: npn; MMBT2222A
Q31_1: npn; MMBT2222A
Q31_2: pnp; MMBT2907A
Q32_1: npn; MMBT2222A
Q32_2: pnp; MMBT2907A
R1: res; 4
R1_7: res; 570K
R1_8: res; 330K
R1_9: res; 20k
R2: res; 33k
R2_7: res; 47k
R2_8: res; 10k
R2_9: res; 20k
R3: res; 1k
R3_7: res; 47k
R3_8: res; 10k
R3_9: res; 20k
R4: res; 20k
R5: res; 1k
R6: res; 20k
R7: res; 1k
R8: res; 20k
R9: res; 1k
R10: res; 20k
R11: res; 1k
R12: res; 20k
R12_1: res; 20k
R12_2: res; 10k
R12_3: res; 1k
R12_4: res; 4.7k
R12_5: res; 33k
R12_6: res; 20k
R13: res; 1k
R14: res; 20k
R15: res; 1k
R16: res; 1m
R17: res; 1m
R18: res; 20k
R19: res; 1k
R20: res; 20k
R21: res; 4.7k
R21_1: res; 20k
R21_2: res; 10k
R21_3: res; 1k
R21_4: res; 4.7k
R21_5: res; 33k
R21_6: res; 20k
R22: res; 10K
R22_1: res; 20k
R22_2: res; 10k
R22_3: res; 1k
R22_4: res; 4.7k
R22_5: res; 33k
R22_6: res; 20k
R23: res; 100K
R24: res; 20k
R25: res; 33k
R26: res; 4.7k
R27: res; 1k
R28: res; 10k
R29: res; 20k
R30: res; 20k
R31: res; 20k
R31_1: res; 20k
R31_2: res; 100K
R31_3: res; 10K
R31_4: res; 4.7k
R31_5: res; 33k
R31_6: res; 20k
R32: res; 20k
R32_1: res; 20k
R32_2: res; 10k
R32_3: res; 1k
R32_4: res; 4.7k
R32_5: res; 33k
R32_6: res; 20k
R33: res; 47k
R34: res; 1m
R35: res; 1m
R36: res; 1k
R37: res; 20k
R38: res; 1k
R39: res; 20k
R40: res; 1k
R41: res; 20k
R42: res; 10k
R43: res; 33k
R44: res; 4.7k
R45: res; 10K
R46: res; 100K
R47: res; 20k
R48: res; 33k
R49: res; 4.7k
R50: res; 1k
R51: res; 10k
R52: res; 20k
R53: res; 20k
R54: res; 20k
R55: res; 20k
R56: res; 47k
R57: res; 1m
R58: res; 1m
R59: res; 1k
R60: res; 20k
R61: res; 1k
R62: res; 20k
R63: res; 1k
R64: res; 20k
R65: res; 10k
Rout1: res; 1m
Rout2: res; 1m
Rout3: res; 1m
Rout4: res; 1m
Rout12: res; 1m
Rout21: res; 1m
Rout22: res; 1m
Rout31: res; 1m
Rout32: res; 1m
S1: pmos; AO3401A
S2: pmos; AO3401A
S3: nmos; IRLB8721
S4: pmos; AO3401A
S5: nmos; IRLB8721
S6: pmos; AO3401A
S7: nmos; IRLB8721
S8: nmos; IRLB8721
S9: pmos; AO3401A
S10: pmos; AO3401A
S12: nmos; IRLB8721
S21: nmos; IRLB8721
S22: nmos; IRLB8721
S31: nmos; IRLB8721
S32: nmos; IRLB8721
Sgnd12: nmos; IRLB8721
V1: voltage; 0
Vcell1: voltage; 3.3
Vcell2: voltage; 3.3
Vcell3: voltage; 3.3
Vcell4: voltage; 3.3
Vcell12: voltage; 3.3
Vcell21: voltage; 3.3
Vcell22: voltage; 3.3
Vcell31: voltage; 3.3
Vcell32: voltage; 3.3
Vcontrol1: voltage; PULSE(0 5 0 1p 1p 10m 20m)
Vcontrol2: voltage; PULSE(0 5 10m 1p 1p 10m 20m)
Vcontrol3: voltage; PULSE(0 5 1m 1p 1p 10m 20m)
Vcontrol4: voltage; PULSE(0 5 10.1m 1p 1p 10m 20m)
Voff: voltage; 0
Von: voltage; 5
Named nets: 0, VcMAS, VcMENOS, VcOFF, VcON, out_neg, out_1, out_pos, VcMAS_delayed, VcMENOS_delayed, out_2
.tran 0 40m 0 10u
.MODEL MMBT2222A  NPN (IS=25.4f NF=1.00 BF=274 VAF=114 IKF=0.121 ISE=14.3p NE=2.00 BR=4.00 NR=1.00 VAR=24.0 IKR=0.300 RE=0.219 RB=0.877 RC=87.7m XTB=1.5 CJE=27.6p VJE=1.10 MJE=0.500 CJC=14.2p VJC=0.300 MJC=0.300 TF=622p TR=124n EG=1.12)
.MODEL MMBT2907A  PNP (IS=60.7f NF=1.00 BF=312 VAF=139 IKF=0.219 ISE=26.0p NE=2.00 BR=4.00 NR=1.00 VAR=20.0 IKR=0.540 RE=85.8m RB=0.343 RC=34.3m XTB=1.5 CJE=50.4p VJE=1.10 MJE=0.500 CJC=23.1p VJC=0.300 MJC=0.300 TF=758p TR=123n EG=1.12)
.model AONS32304 VDMOS(Kp=239 Rs=0.42m Rd=1.2m Rg=3.0 Vto=2.16 VtoTc=-2.8m Bex=-2.07 mtriode=1.1 Ksubthres=0.1 Lambda=0.158 Cgdmax=1420p Cgdmin=288p Cgs=5352p tt=19n A=0.7 Is=2.35E-11 N=1.017 Eg=1.07 Rb=0.1m Trb1=-1 BV=33 IBV=250u M=0.456 Vj=0.56 Cjo=1090.0pF mfg=AOS Vds=30 Ron=1.8m Qg=40n)
.model MMBFJ201 NJF(BETA=0.000896 IS=3E-12 VTO=-0.794 LAMBDA=0.02 RD=0.001 RS=0.0013)
.inc AO3401A.sub
.inc IRLB8721.sub
.inc 1N4736A.sub
.inc FDMS6681Z.lib
.inc 1N4730A.sub
.inc irlml6402.spi
.model LED_RED D(Is=2e-9 N=2.2 Rs=10 Bv=5 Ibv=0.1 Cjo=20p M=0.4 Vj=0.65)
.op
.options plotwinsize=0
.options numdgt=6
.options reltol=0.001 abstol=1u
.options solver=alternate
