DeniseViltes/Tesis/Ltspice/proyectos/modo_carga/prueba_de_modo_carga-1Banco.asc

A5: inv
A6: inv
C5: cap; 1µ; IC=0
C6: cap; 1µ; IC=0
D1: zener; 1N4730A
D4: LED
D5: LED
D11: zener; 1N4730A
D12: zener; 1N4730A
D14: LED
I1: current; 10m
Q1: npn; MMBT2222A
Q1_1: npn; MMBT2222A
Q1_2: njf; MMBFJ201
Q3: npn; MMBT2222A
Q11: npn; MMBT2222A
Q11_2: pnp; MMBT2907A
Q11_3: npn; MMBT2222A
Q12_1: npn; MMBT2222A
Q12_2: pnp; MMBT2907A
Q12_3: npn; MMBT2222A
Q14_1: npn; MMBT2222A
R1: res; 1k
R1_7: res; 47k
R1_8: res; 30k
R1_9: res; 20k
R2: res; 20k
R3: res; 1k
R4: res; 20k
R11_1: res; 20k
R11_2: res; 10Meg
R11_3: res; 1Meg
R11_4: res; 4.7k
R11_5: res; 33k
R11_6: res; 20k
R12_1: res; 20k
R12_2: res; 10Meg
R12_3: res; 1Meg
R12_4: res; 4.7k
R12_5: res; 33k
R12_6: res; 20k
R19: res; 1k
R20: res; 20k
Rout11: res; 1m
Rout12: res; 1m
S1: pmos; AO3401A
S11: nmos; IRLB8721
S12: nmos; IRLB8721
Sgnd11: nmos; IRLB8721
Sgnd12: nmos; IRLB8721
V1: voltage; 0
V2: voltage; 3.3
Vcontrol1: voltage; PULSE(0 5 0 1p 1p 10m 20m)
Vcontrol2: voltage; PULSE(0 5 10m 1p 1p 10m 20m)
Vcontrol3: voltage; PULSE(0 5 1m 1p 1p 10m 20m)
Vcontrol4: voltage; PULSE(0 5 10.1m 1p 1p 10m 20m)
Voff: voltage; 0
Von: voltage; 5
Named nets: 0, VcMAS, VcMENOS, VcOFF, VcON, out_neg, out_pos, VcMAS_delayed, VcMENOS_delayed
.tran 0 20m 0 10u uic
.MODEL MMBT2222A  NPN (IS=25.4f NF=1.00 BF=274 VAF=114 IKF=0.121 ISE=14.3p NE=2.00 BR=4.00 NR=1.00 VAR=24.0 IKR=0.300 RE=0.219 RB=0.877 RC=87.7m XTB=1.5 CJE=27.6p VJE=1.10 MJE=0.500 CJC=14.2p VJC=0.300 MJC=0.300 TF=622p TR=124n EG=1.12)
.MODEL MMBT2907A  PNP (IS=60.7f NF=1.00 BF=312 VAF=139 IKF=0.219 ISE=26.0p NE=2.00 BR=4.00 NR=1.00 VAR=20.0 IKR=0.540 RE=85.8m RB=0.343 RC=34.3m XTB=1.5 CJE=50.4p VJE=1.10 MJE=0.500 CJC=23.1p VJC=0.300 MJC=0.300 TF=758p TR=123n EG=1.12)
.model AONS32304 VDMOS(Kp=239 Rs=0.42m Rd=1.2m Rg=3.0 Vto=2.16 VtoTc=-2.8m Bex=-2.07 mtriode=1.1 Ksubthres=0.1 Lambda=0.158 Cgdmax=1420p Cgdmin=288p Cgs=5352p tt=19n A=0.7 Is=2.35E-11 N=1.017 Eg=1.07 Rb=0.1m Trb1=-1 BV=33 IBV=250u M=0.456 Vj=0.56 Cjo=1090.0pF mfg=AOS Vds=30 Ron=1.8m Qg=40n)
.model MMBFJ201 NJF(BETA=0.000896 IS=3E-12 VTO=-0.794 LAMBDA=0.02 RD=0.001 RS=0.0013)
.inc modelos\\AO3401A.sub
.inc modelos\\IRLB8721.sub
.inc modelos\\1N4736A.sub
.options plotwinsize=0
.options numdgt=6
.options reltol=0.001 abstol=1u
.options solver=alternate
.inc modelos\\FDMS6681Z.lib
.inc modelos\\1N4730A.sub
.model LED_RED D(Is=2e-9 N=2.2 Rs=10 Bv=5 Ibv=0.1 Cjo=20p M=0.4 Vj=0.65)
