DeniseViltes/Tesis/codigo/python/simulador_config/resultados/version3.3 seleccionadas/mas-menos-mas.asc

A1: inv
A2: inv
A3: inv
A4: inv
A5: inv
A6: inv
CL: cap; 100u
D1: zener; 1N4730A
D2: zener; 1N4730A
D3: zener; 1N4730A
D4: LED
D5: LED
D6: LED
D7: LED
D8: LED
D9: LED
D10: LED
D11: zener; 1N4730A
D12: zener; 1N4730A
D13: LED
D14: LED
D21: zener; 1N4730A
D22: zener; 1N4730A
D31: zener; 1N4730A
D32: zener; 1N4730A
Q1: npn; MMBT2222A
Q1_1: npn; MMBT2222A
Q1_2: njf; MMBFJ201
Q2: npn; MMBT2222A
Q2_1: npn; MMBT2222A
Q2_2: njf; MMBFJ201
Q3: npn; MMBT2222A
Q3_1: npn; MMBT2222A
Q3_2: njf; MMBFJ201
Q4: npn; MMBT2222A
Q5: npn; MMBT2222A
Q6: npn; MMBT2222A
Q7: npn; MMBT2222A
Q8: npn; MMBT2222A
Q9: npn; MMBT2222A
Q10: npn; MMBT2222A
Q11: npn; MMBT2222A
Q11_2: pnp; MMBT2907A
Q11_3: npn; MMBT2222A
Q12_1: npn; MMBT2222A
Q12_2: pnp; MMBT2907A
Q12_3: npn; MMBT2222A
Q14_1: npn; MMBT2222A
Q21_1: npn; MMBT2222A
Q21_2: pnp; MMBT2907A
Q21_3: npn; MMBT2222A
Q22_1: npn; MMBT2222A
Q22_2: pnp; MMBT2907A
Q22_3: npn; MMBT2222A
Q31_1: npn; MMBT2222A
Q31_2: pnp; MMBT2907A
Q32_1: npn; MMBT2222A
Q32_2: pnp; MMBT2907A
R1: res; 1k
R1_7: res; 47k
R1_8: res; 30k
R1_9: res; 20k
R2: res; 20k
R2_7: res; 47k
R2_8: res; 10k
R2_9: res; 20k
R3: res; 1k
R3_7: res; 47k
R3_8: res; 10k
R3_9: res; 20k
R4: res; 20k
R5: res; 1k
R6: res; 20k
R7: res; 1k
R8: res; 20k
R9: res; 1k
R10: res; 20k
R11: res; 1k
R11_1: res; 20k
R11_2: res; 10Meg
R11_3: res; 1Meg
R11_4: res; 4.7k
R11_5: res; 33k
R11_6: res; 20k
R12: res; 20k
R12_1: res; 20k
R12_2: res; 10Meg
R12_3: res; 1Meg
R12_4: res; 4.7k
R12_5: res; 33k
R12_6: res; 20k
R13: res; 1k
R14: res; 20k
R15: res; 1k
R16: res; 1m
R17: res; 1m
R18: res; 20k
R19: res; 1k
R20: res; 20k
R21_1: res; 20k
R21_2: res; 10Meg
R21_3: res; 1Meg
R21_4: res; 4.7k
R21_5: res; 33k
R21_6: res; 20k
R22_1: res; 20k
R22_2: res; 10Meg
R22_3: res; 1Meg
R22_4: res; 4.7k
R22_5: res; 33k
R22_6: res; 20k
R31_1: res; 20k
R31_2: res; 10Meg
R31_3: res; 1Meg
R31_4: res; 4.7k
R31_5: res; 33k
R31_6: res; 20k
R32_1: res; 20k
R32_2: res; 10Meg
R32_3: res; 1Meg
R32_4: res; 4.7k
R32_5: res; 33k
R32_6: res; 20k
RL2: res; 1m
RL: res; 3.2
Rout11: res; 10m
Rout12: res; 10m
Rout21: res; 10m
Rout22: res; 10m
Rout31: res; 10m
Rout32: res; 10m
S1: pmos; AO3401A
S2: pmos; AO3401A
S4: pmos; AO3401A
S11: nmos; IRLB8721
S12: nmos; IRLB8721
S21: nmos; IRLB8721
S22: nmos; IRLB8721
S31: nmos; IRLB8721
S32: nmos; IRLB8721
Sgnd11: nmos; IRLB8721
Sgnd12: nmos; IRLB8721
V1: voltage; 0
Vcell11: voltage; 3.3
Vcell12: voltage; 3.3
Vcell21: voltage; 3.3
Vcell22: voltage; 3.3
Vcell31: voltage; 3.3
Vcell32: voltage; 3.3
Vcontrol1: voltage; PULSE(0 5 0 100n 100n 10m 20m)
Vcontrol2: voltage; PULSE(0 5 10m 100n 100n 10m 20m)
Voff1: voltage; 0
Von1: voltage; 5
Von2: voltage; 5
Named nets: 0, VcMAS, VcMENOS, VcOFF, VcON, out_neg, out_1, out_pos, out_2, VCC
.tran 0 40m 0 10u
.MODEL MMBT2222A  NPN (IS=25.4f NF=1.00 BF=274 VAF=114 IKF=0.121 ISE=14.3p NE=2.00 BR=4.00 NR=1.00 VAR=24.0 IKR=0.300 RE=0.219 RB=0.877 RC=87.7m XTB=1.5 CJE=27.6p VJE=1.10 MJE=0.500 CJC=14.2p VJC=0.300 MJC=0.300 TF=622p TR=124n EG=1.12)
.MODEL MMBT2907A  PNP (IS=60.7f NF=1.00 BF=312 VAF=139 IKF=0.219 ISE=26.0p NE=2.00 BR=4.00 NR=1.00 VAR=20.0 IKR=0.540 RE=85.8m RB=0.343 RC=34.3m XTB=1.5 CJE=50.4p VJE=1.10 MJE=0.500 CJC=23.1p VJC=0.300 MJC=0.300 TF=758p TR=123n EG=1.12)
.model AONS32304 VDMOS(Kp=239 Rs=0.42m Rd=1.2m Rg=3.0 Vto=2.16 VtoTc=-2.8m Bex=-2.07 mtriode=1.1 Ksubthres=0.1 Lambda=0.158 Cgdmax=1420p Cgdmin=288p Cgs=5352p tt=19n A=0.7 Is=2.35E-11 N=1.017 Eg=1.07 Rb=0.1m Trb1=-1 BV=33 IBV=250u M=0.456 Vj=0.56 Cjo=1090.0pF mfg=AOS Vds=30 Ron=1.8m Qg=40n)
.model MMBFJ201 NJF(BETA=0.000896 IS=3E-12 VTO=-0.794 LAMBDA=0.02 RD=0.001 RS=0.0013)
.inc AO3401A.sub
.inc IRLB8721.sub
.inc 1N4736A.sub
.options plotwinsize=0
.options numdgt=6
.options reltol=0.001 abstol=1u
.options solver=alternate
.inc FDMS6681Z.lib
.inc 1N4730A.sub
.model LED_RED D(Is=2e-9 N=2.2 Rs=10 Bv=5 Ibv=0.1 Cjo=20p M=0.4 Vj=0.65)
.options solver=alternate
.options abstol=1u
