DeniseViltes/Tesis/Ltspice/proyectos/matriz_2x2/runs/mosfet_en_tierra/version2.6-prueba_mosfet-drain_a_tierra.asc

A1: inv
A2: inv
A3: inv
A4: inv
C1: cap; 10n
D1: zener; 1N4730A
D2: zener; 1N4730A
D14: zener; 1N4730A
D15: zener; 1N4730A
D24: zener; 1N4730A
D25: zener; 1N4730A
M3: nmos; IRLB8721
M4: nmos; IRLB8721
Q1_1: npn; MMBT2222A
Q1_2: njf; MMBFJ201
Q2_1: npn; MMBT2222A
Q2_2: njf; MMBFJ201
Q14_1: npn; MMBT2222A
Q14_2: pnp; MMBT2907A
Q14_3: npn; MMBT2222A
Q15_1: npn; MMBT2222A
Q15_2: pnp; MMBT2907A
Q15_3: npn; MMBT2222A
Q24_1: npn; MMBT2222A
Q24_2: pnp; MMBT2907A
Q24_3: npn; MMBT2222A
Q25_1: npn; MMBT2222A
Q25_2: pnp; MMBT2907A
Q25_3: npn; MMBT2222A
R1: res; 1m
R1_7: res; 570K
R1_8: res; 300K
R1_9: res; 20k
R2_7: res; 570K
R2_8: res; 300K
R2_9: res; 20k
R14_1: res; 20k
R14_2: res; 10Meg
R14_3: res; 1Meg
R14_4: res; 49.9k
R14_5: res; 300k
R14_6: res; 20k
R15_1: res; 20k
R15_2: res; 10Meg
R15_3: res; 1Meg
R15_4: res; 49.9k
R15_5: res; 300k
R15_6: res; 20k
R24_1: res; 20k
R24_2: res; 10Meg
R24_3: res; 1Meg
R24_4: res; 49.9k
R24_5: res; 300k
R24_6: res; 20k
R25_1: res; 20k
R25_2: res; 10Meg
R25_3: res; 1Meg
R25_4: res; 49.9k
R25_5: res; 300k
R25_6: res; 20k
RL: res; 10
Rout14: res; 1m
Rout15: res; 1m
Rout24: res; 1m
Rout25: res; 1m
S1: pmos; AO3401A
S2: pmos; AO3401A
S14: nmos; IRLB8721
S15: nmos; IRLB8721
S24: nmos; IRLB8721
S25: nmos; IRLB8721
Vcell14: voltage; 3.2
Vcell15: voltage; 3.2
Vcell24: voltage; 3.2
Vcell25: voltage; 3.2
Vcontrol1: voltage; PULSE(0 3.3 0 1p 1p 10m 20m)
Vcontrol2: voltage; PULSE(0 3.3 10m 1p 1p 10m 20m)
Vcontrol3: voltage; PULSE(0 5 1m 1p 1p 10m 20m)
Vcontrol4: voltage; PULSE(0 5 10.1m 1p 1p 10m 20m)
Voff: voltage; 0
Von: voltage; 3.3
Named nets: 0, VcMAS, VcMENOS, VcOFF, VcON, out_neg, out_1, out_pos, VcMAS_delayed, VcMENOS_delayed
.tran 0 20m 0 10u
.MODEL MMBT2222A  NPN (IS=25.4f NF=1.00 BF=274 VAF=114 IKF=0.121 ISE=14.3p NE=2.00 BR=4.00 NR=1.00 VAR=24.0 IKR=0.300 RE=0.219 RB=0.877 RC=87.7m XTB=1.5 CJE=27.6p VJE=1.10 MJE=0.500 CJC=14.2p VJC=0.300 MJC=0.300 TF=622p TR=124n EG=1.12)
.MODEL MMBT2907A  PNP (IS=60.7f NF=1.00 BF=312 VAF=139 IKF=0.219 ISE=26.0p NE=2.00 BR=4.00 NR=1.00 VAR=20.0 IKR=0.540 RE=85.8m RB=0.343 RC=34.3m XTB=1.5 CJE=50.4p VJE=1.10 MJE=0.500 CJC=23.1p VJC=0.300 MJC=0.300 TF=758p TR=123n EG=1.12)
.model AONS32304 VDMOS(Kp=239 Rs=0.42m Rd=1.2m Rg=3.0 Vto=2.16 VtoTc=-2.8m Bex=-2.07 mtriode=1.1 Ksubthres=0.1 Lambda=0.158 Cgdmax=1420p Cgdmin=288p Cgs=5352p tt=19n A=0.7 Is=2.35E-11 N=1.017 Eg=1.07 Rb=0.1m Trb1=-1 BV=33 IBV=250u M=0.456 Vj=0.56 Cjo=1090.0pF mfg=AOS Vds=30 Ron=1.8m Qg=40n)
.model MMBFJ201 NJF(BETA=0.000896 IS=3E-12 VTO=-0.794 LAMBDA=0.02 RD=0.001 RS=0.0013)
.inc AO3401A.sub
.inc IRLB8721.sub
.lib 1N4730A.sub
.options plotwinsize=0
.options numdgt=6
.options reltol=0.001 abstol=1u
.options solver=alternate
.include irf4905.spi
;.step param TD list 100n 200n 500n 1u
.param TD = 500n         ; Tiempo muerto (dead-time)
.param VTH = 2.5         ; Umbral de detección de señal alta
