DeniseViltes/Tesis/prototipo/untitled.kicad_sch

## KiCad design prototipo/untitled.kicad_sch (2025-11-12)

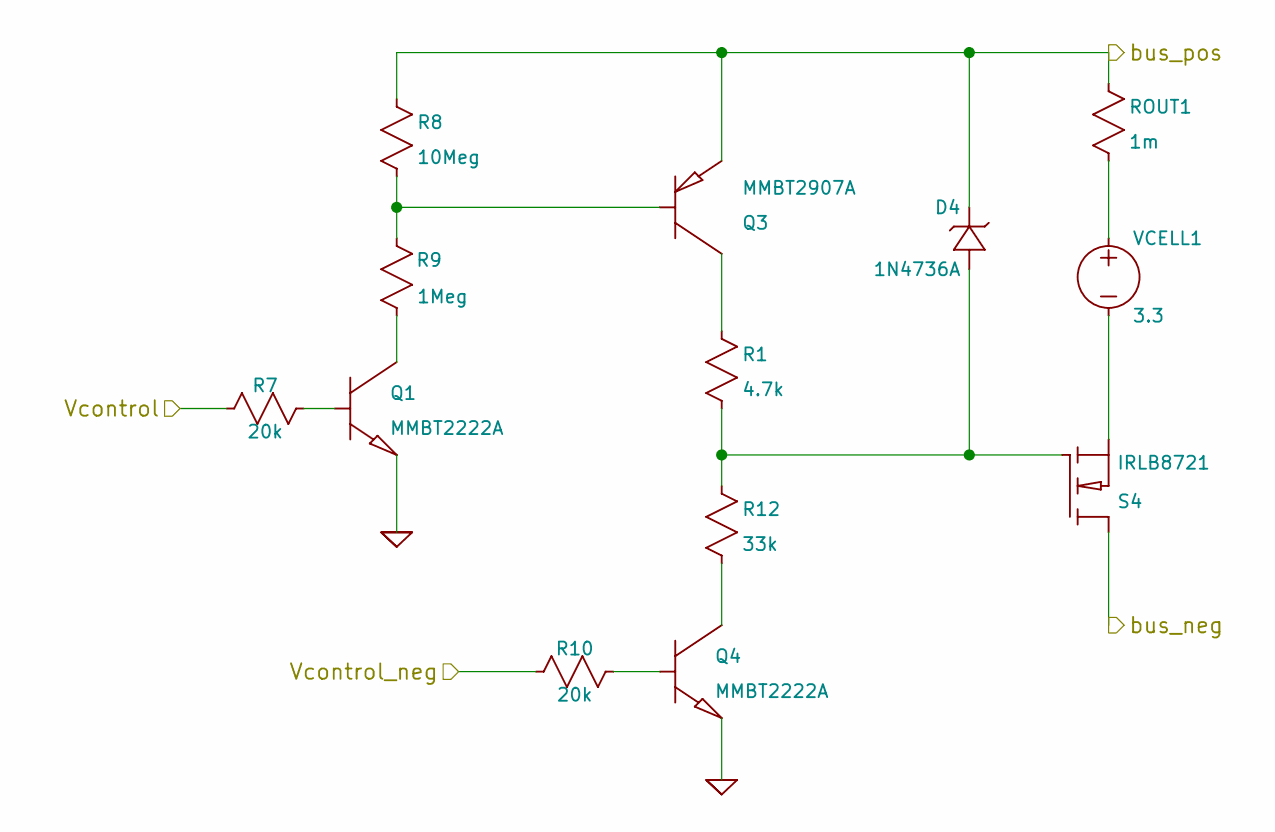
[picture p339: schematic untitled.kicad_sch]

Parts:
D4: 1N4736A; D_DO-41_SOD81_P7.62mm_Horizontal
Q1, Q4: MMBT2222A; SOT-23-3
Q3: MMBT2907A; SOT-23-3
R1: 4.7k; R_Axial_DIN0207_L6.3mm_D2.5mm_P7.62mm_Horizontal
R7, R10: 20k; R_Axial_DIN0207_L6.3mm_D2.5mm_P7.62mm_Horizontal
R8: 10Meg; R_Axial_DIN0207_L6.3mm_D2.5mm_P7.62mm_Horizontal
R9: 1Meg; R_Axial_DIN0207_L6.3mm_D2.5mm_P7.62mm_Horizontal
R12: 33k; R_Axial_DIN0207_L6.3mm_D2.5mm_P7.62mm_Horizontal
ROUT1: 1m; R_Axial_DIN0207_L6.3mm_D2.5mm_P7.62mm_Horizontal
S4: IRLB8721; TO-220-3_Vertical
VCELL1: 3.3; BatteryHolder_MPD_BK-18650-PC2

Connections:
0: Q1.2 (E), Q4.2 (E)
unnamed: D4.1 (+), R1.2, R12.1, S4.1 (G)
unnamed: Q1.1 (B), R7.1
unnamed: Q1.3 (C), R9.2
unnamed: Q3.1 (B), R8.2, R9.1
unnamed: Q3.3 (C), R1.1
unnamed: Q4.1 (B), R10.1
unnamed: Q4.3 (C), R12.2
unnamed: ROUT1.2, VCELL1.1 (+)
unnamed: S4.3 (S), VCELL1.2 (-)
Vcontrol: R7.2
Vcontrol_neg: R10.2
bus_neg: S4.2 (D)
bus_pos: D4.2 (-), Q3.2 (E), R8.1, ROUT1.1
