DeniseViltes/Tesis/Prototipo_/Prototipo/prototipo_nuevo.kicad_sch

## KiCad design Prototipo_/Prototipo/prototipo_nuevo.kicad_sch (2025-11-12)

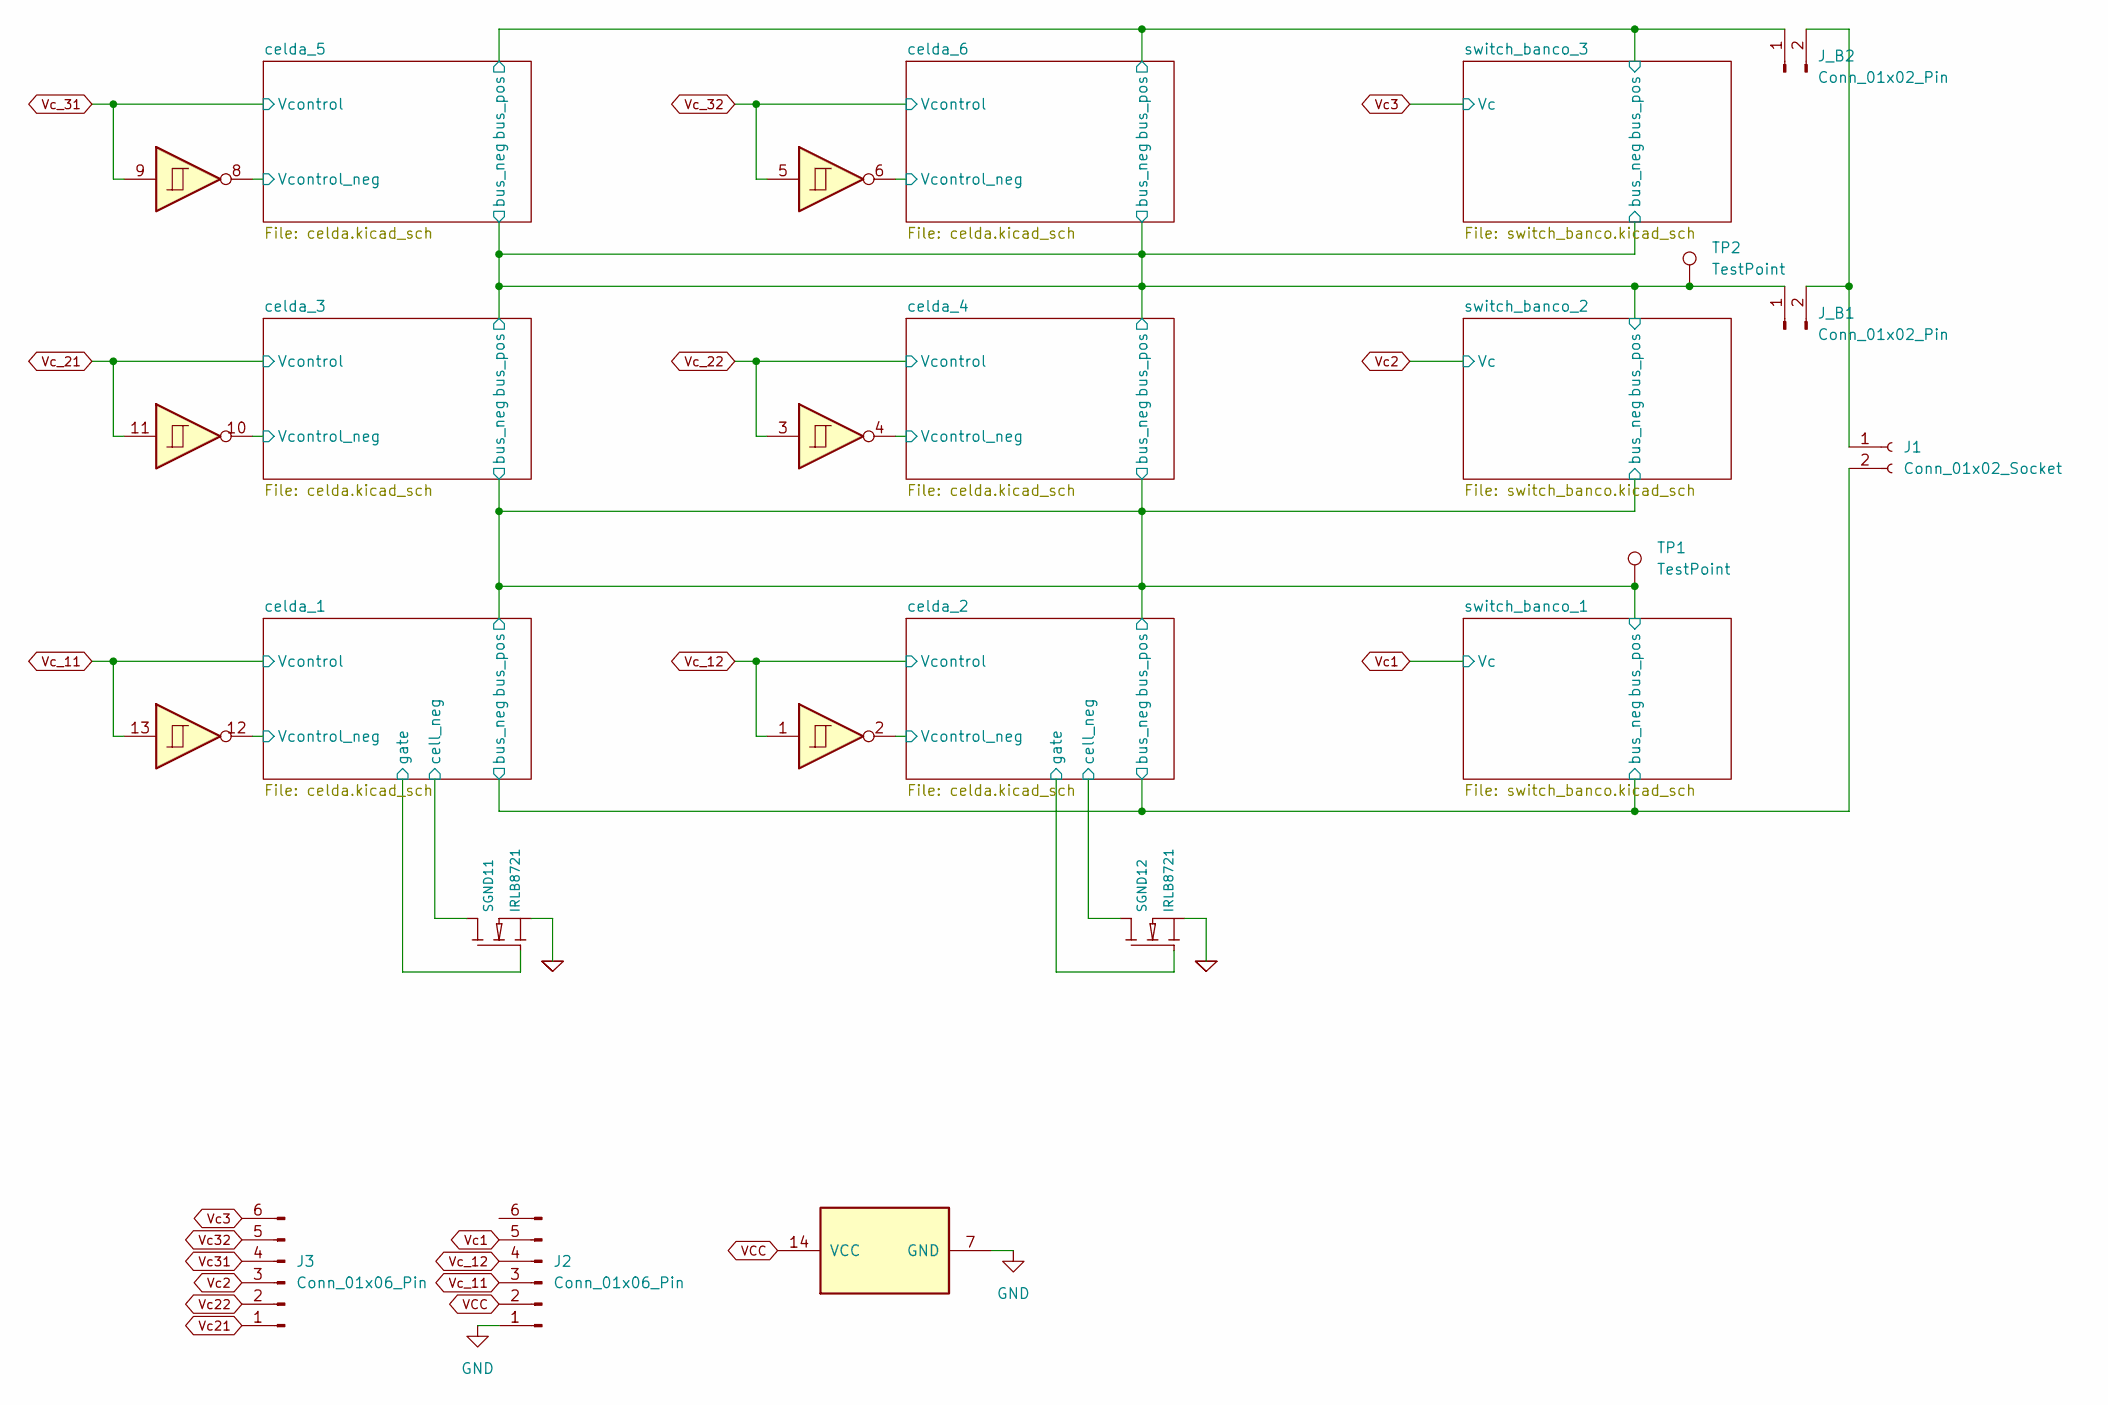
[picture p340: schematic prototipo_nuevo.kicad_sch]

Parts:
A1: DIP-14_W7.62mm_LongPads
J1: Conn_01x02_Socket; TerminalBlock_MaiXu_MX126-5.0-02P_1x02_P5.00mm
J2, J3: Conn_01x06_Pin; JST_VH_B6P-VH-B_1x06_P3.96mm_Vertical
J_B1, J_B2: Conn_01x02_Pin; JST_VH_B2P-VH_1x02_P3.96mm_Vertical
SGND11, SGND12: IRLB8721; TO-220-3_Vertical
TP1, TP2: TestPoint; TestPoint_Bridge_Pitch2.54mm_Drill1.0mm

Connections:
0: SGND11.3 (S), SGND12.3 (S)
GND: A1.7 (GND), J2.1
unnamed: J1.1, J_B1.2, J_B2.2
VCC: A1.14 (VCC), J2.2
Vc1: J2.5
Vc2: J3.3
Vc3: J3.6
Vc21: J3.1
Vc22: J3.2
Vc31: J3.4
Vc32: J3.5
Vc_11: A1.13, J2.3
Vc_12: A1.1, J2.4
Vc_21: A1.11
Vc_22: A1.3
Vc_31: A1.9
Vc_32: A1.5
Vcontrol_neg: A1.2, A1.4, A1.6, A1.8, A1.10, A1.12
bus_neg: J1.2, J_B1.1, TP2.1
bus_pos: J_B2.1, TP1.1
cell_neg: SGND11.2 (D), SGND12.2 (D)
gate: SGND11.1 (G), SGND12.1 (G)
