DeniseViltes/Tesis/codigo/firmware/Controlador/Final/Core/Inc/cli.h

/*
 * cli.h
 *
 *  Created on: 12 jun 2026
 *      Author: ---
 */

#ifndef INC_CLI_H_
#define INC_CLI_H_

#include "stm32f1xx_hal.h"
#include <ctype.h>


//Me copio del CLI del Prototipo

/* Inicializa la CLI (imprime banner y arranca RX por IT) */
void CLI_Init(UART_HandleTypeDef *huart);

/* Debe llamarse desde HAL_UART_RxCpltCallback */
void CLI_RxCallback(UART_HandleTypeDef *huart);


void CLI_Process(void);

#endif /* INC_CLI_H_ */
